TheJustMoose/74HC-CPU/hard/!CMD_DEC/Flags/pdf/Flags-B_Cu.pdf

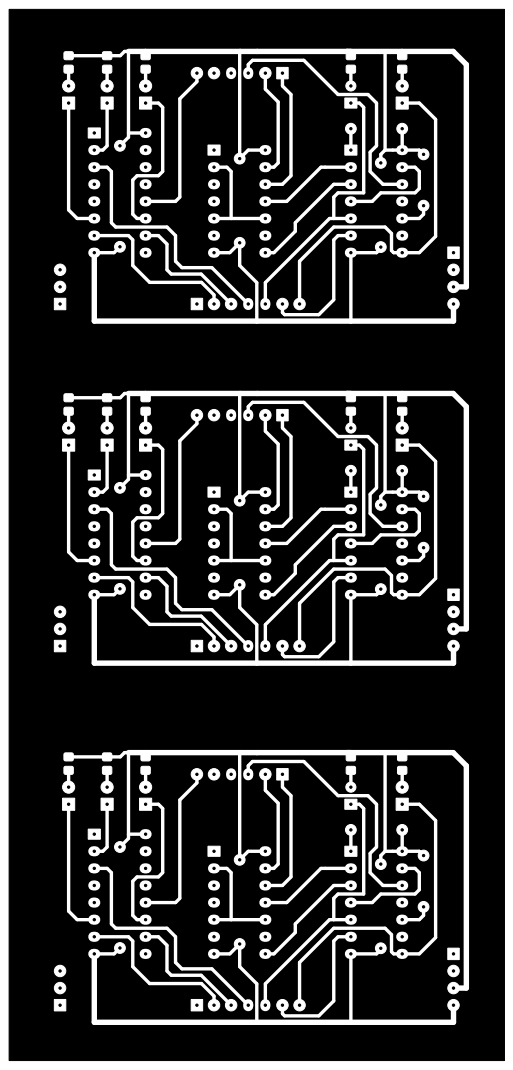
[picture p27: page 1]
