TheJustMoose/74HC-CPU/hard/!CMD_DEC/Flags/pdf/Flags-F_Cu.pdf

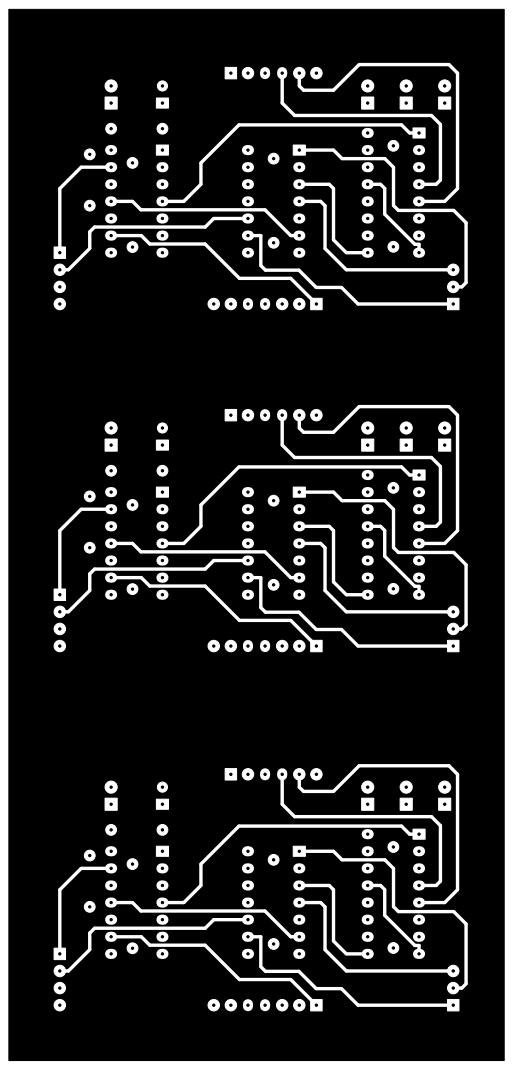
[picture p28: page 1]
