TheJustMoose/74HC-CPU/hard/!ALU/LSR/pdf/LSR-F_Cu.pdf

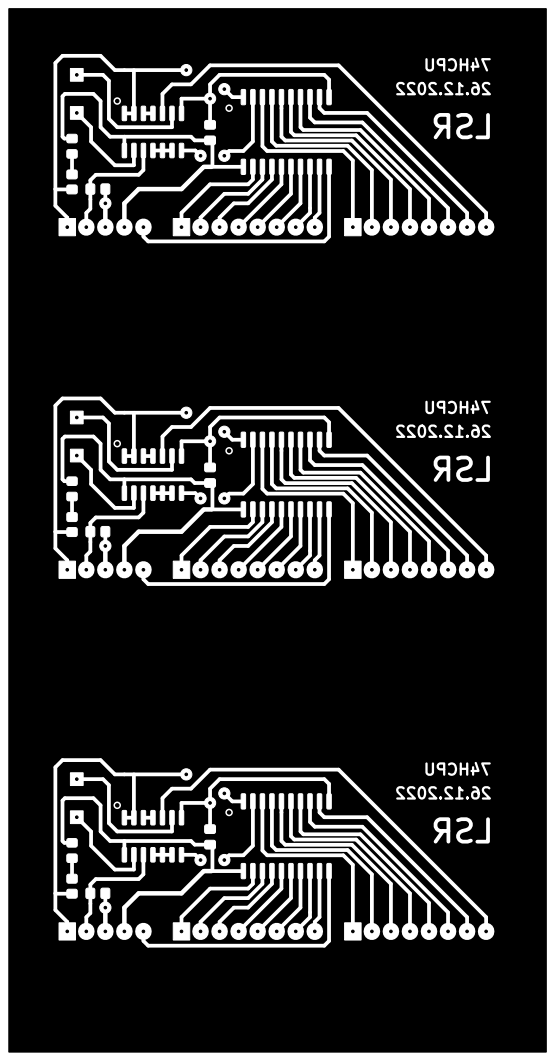
[picture p29: page 1]
