TheJustMoose/74HC-CPU/hard/!ALU/SWAP/pdf/SWAP-F_Cu.pdf

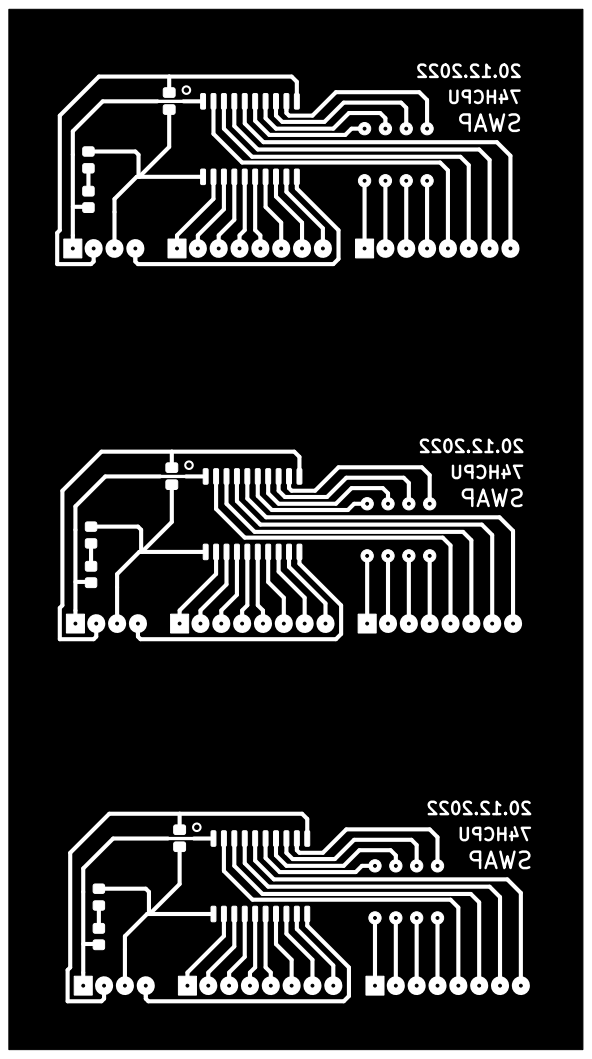
[picture p30: page 1]
