TheJustMoose/74HC-CPU/hard/!ALU/MOV/pdf/MOV-F_Cu.pdf

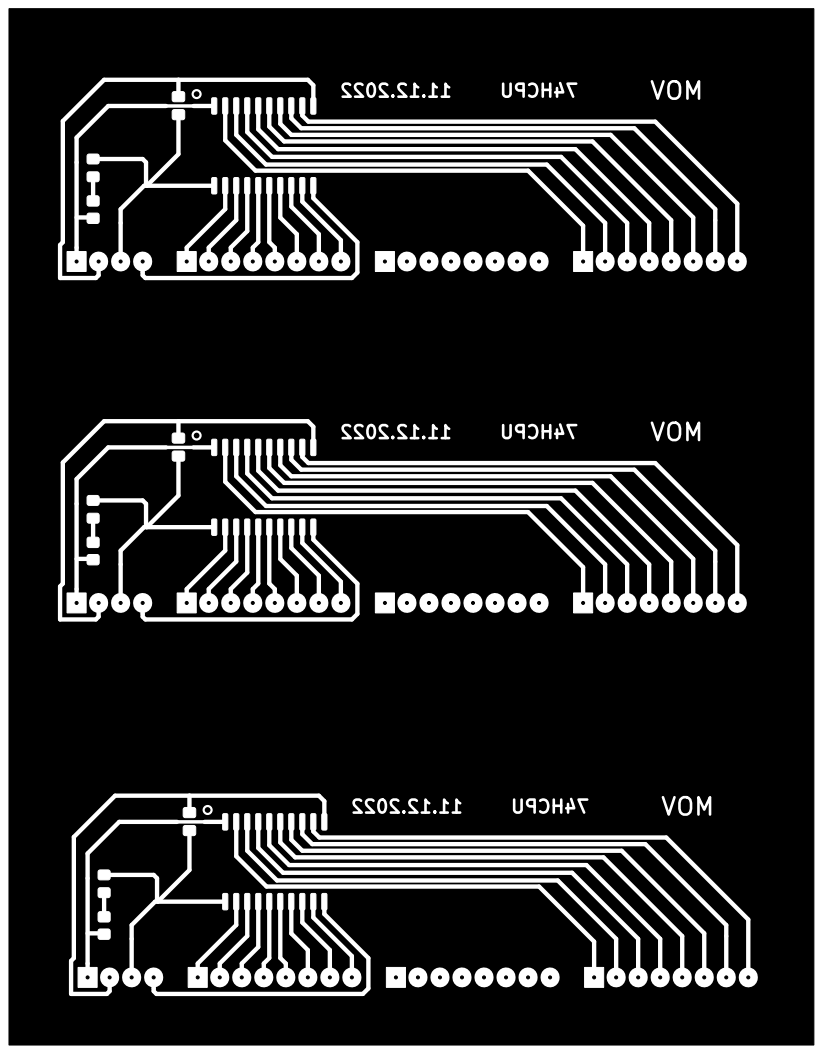
[picture p31: page 1]
