TheJustMoose/74HC-CPU/hard/!ALU/CMP/pdf/CMP-B_Cu.pdf

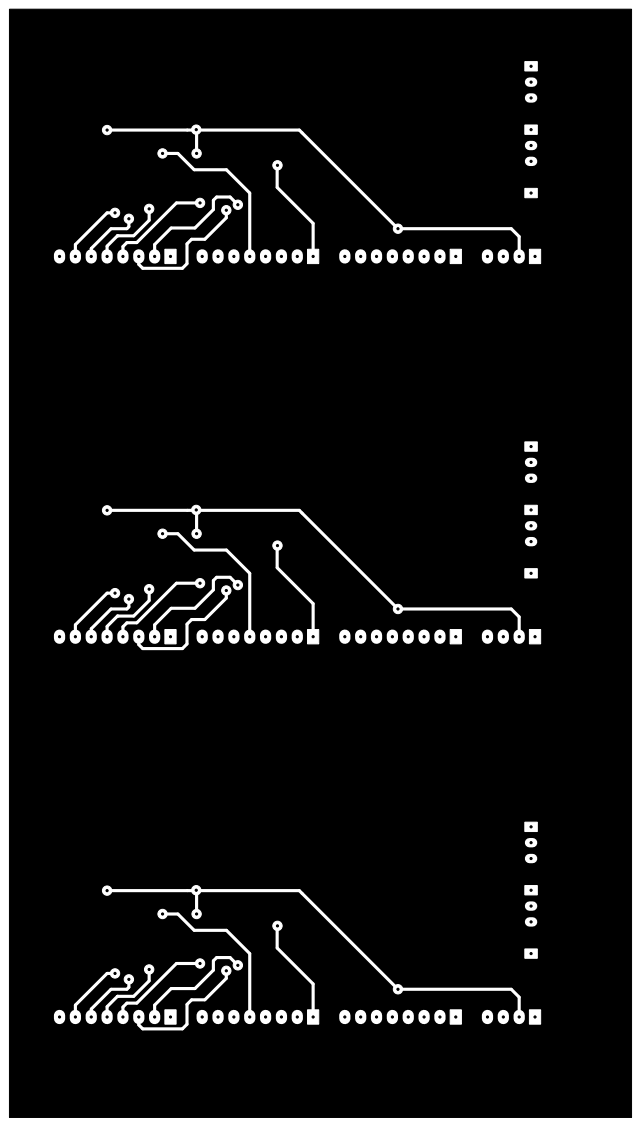
[picture p32: page 1]
