TheJustMoose/74HC-CPU/hard/!ALU/CMP/pdf/CMP-F_Cu.pdf

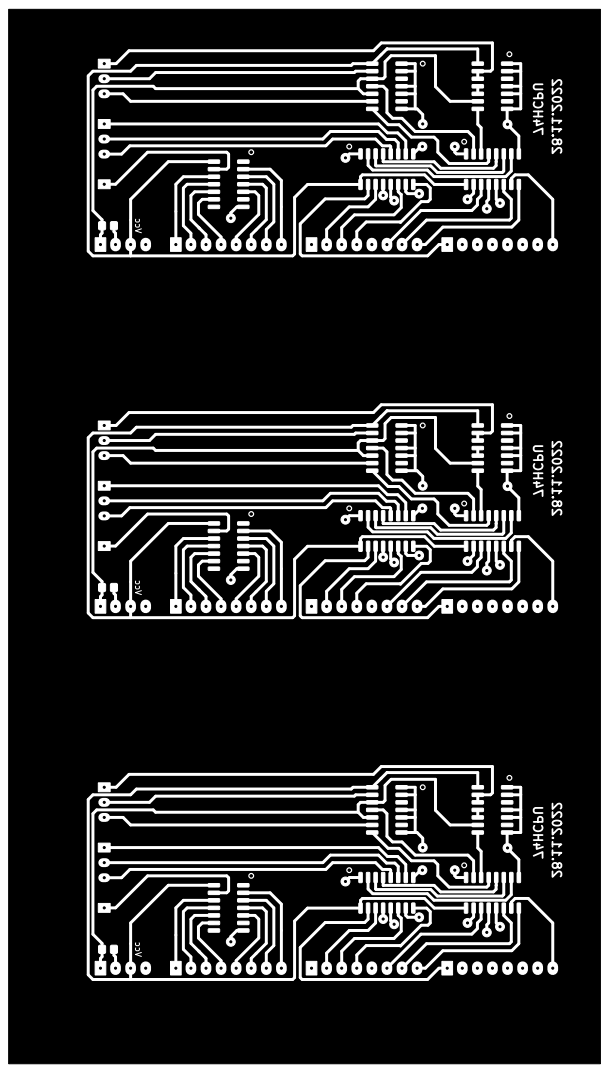
[picture p33: page 1]
