TheJustMoose/74HC-CPU/hard/!ALU/ADD/pdf/ADD-B_Cu.pdf

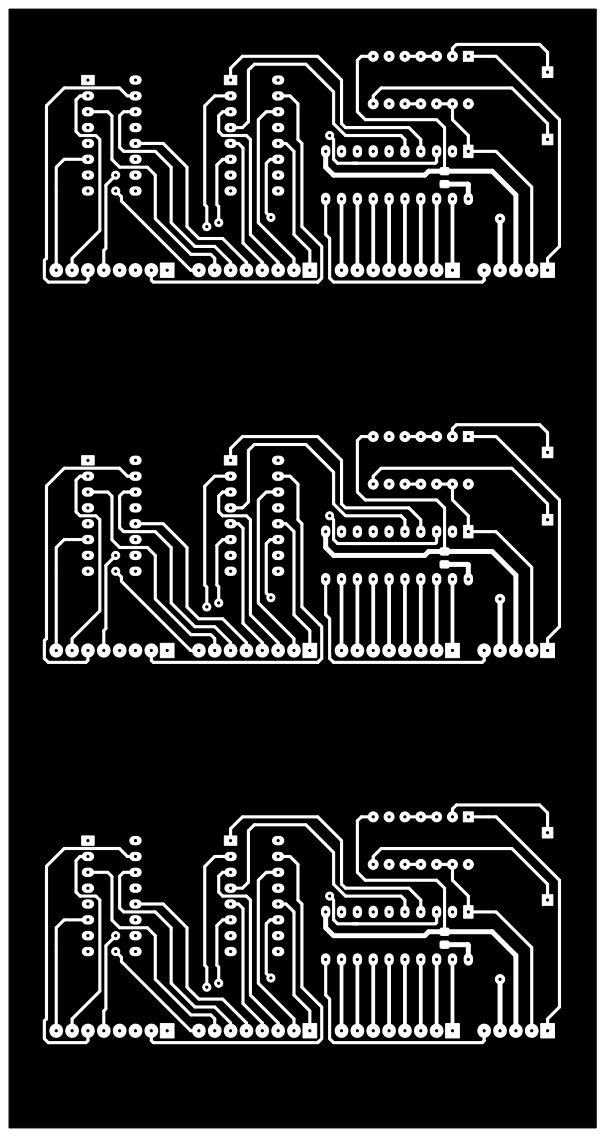
[picture p34: page 1]
