TheJustMoose/74HC-CPU/hard/!ALU/ADD/pdf/ADD-F_Cu.pdf

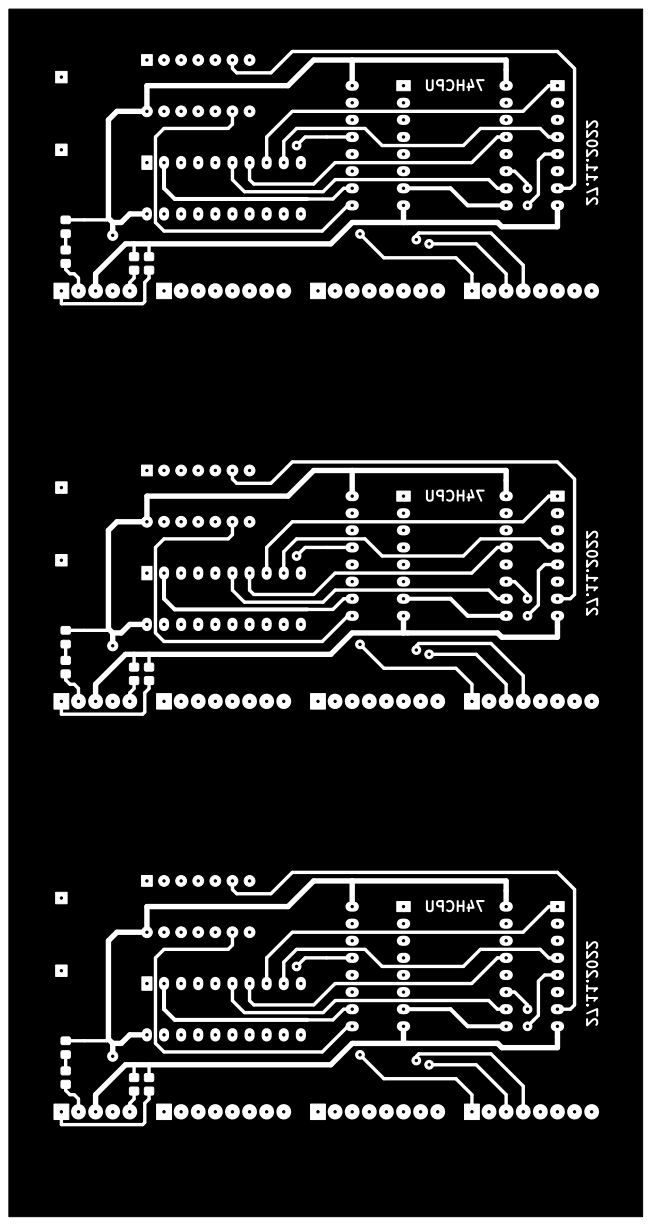
[picture p35: page 1]
