TheJustMoose/74HC-CPU/hard/Proto/273/pdf/273-F_Cu.pdf

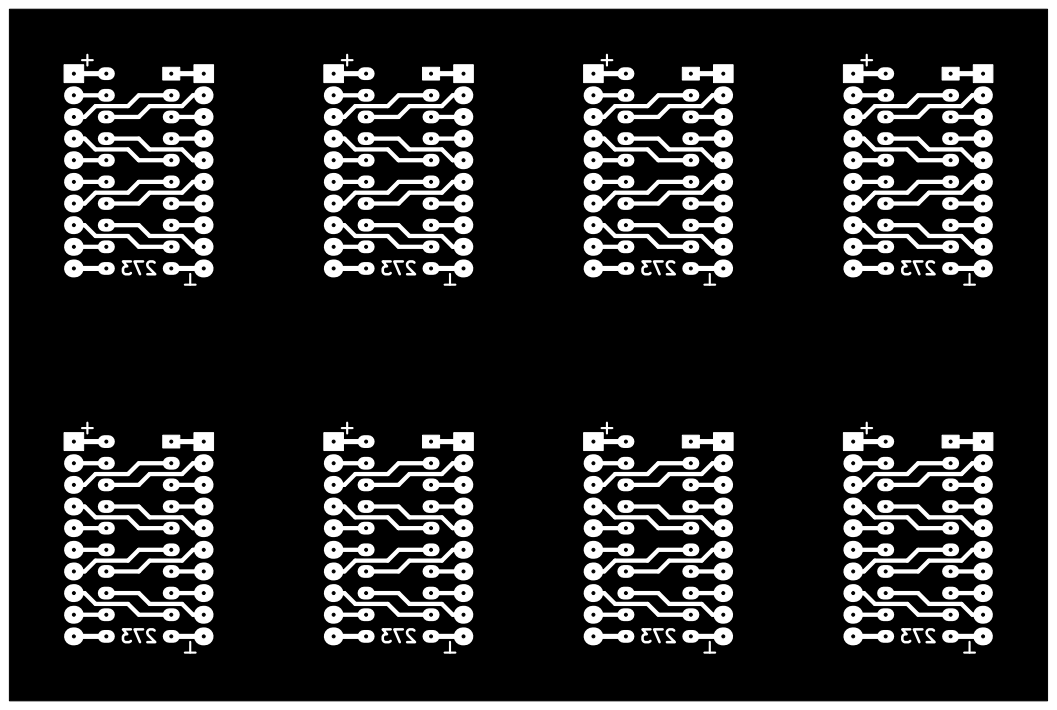
[picture p36: page 1]
