TheJustMoose/74HC-CPU/hard/!ALU/AND_SMD/pdf/AND-B_Cu.pdf

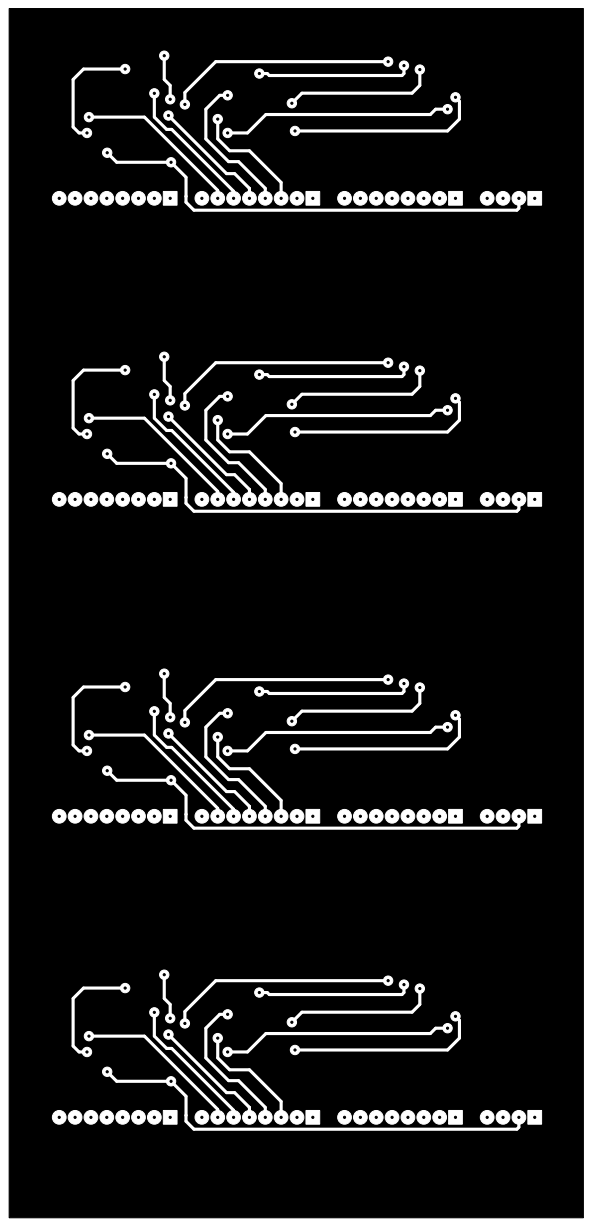
[picture p37: page 1]
