TheJustMoose/74HC-CPU/hard/!ALU/AND_SMD/pdf/AND-F_Cu.pdf

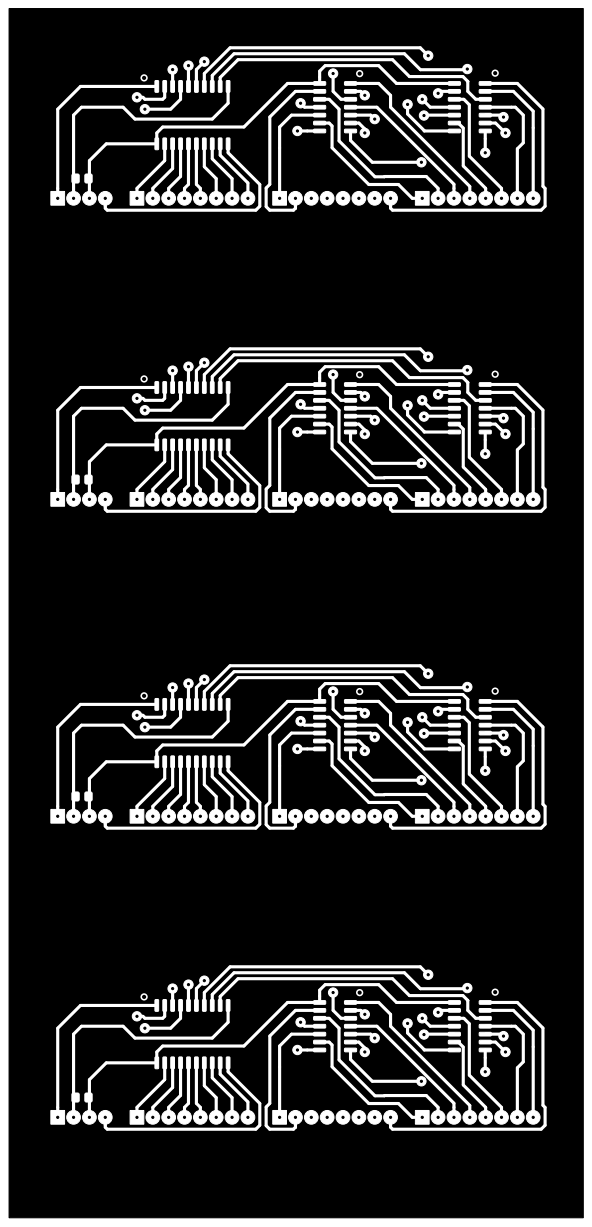
[picture p38: page 1]
