TheJustMoose/74HC-CPU/Trash/MUX8x1-v3/pdf/MUX8x1-v3-B_Cu.pdf

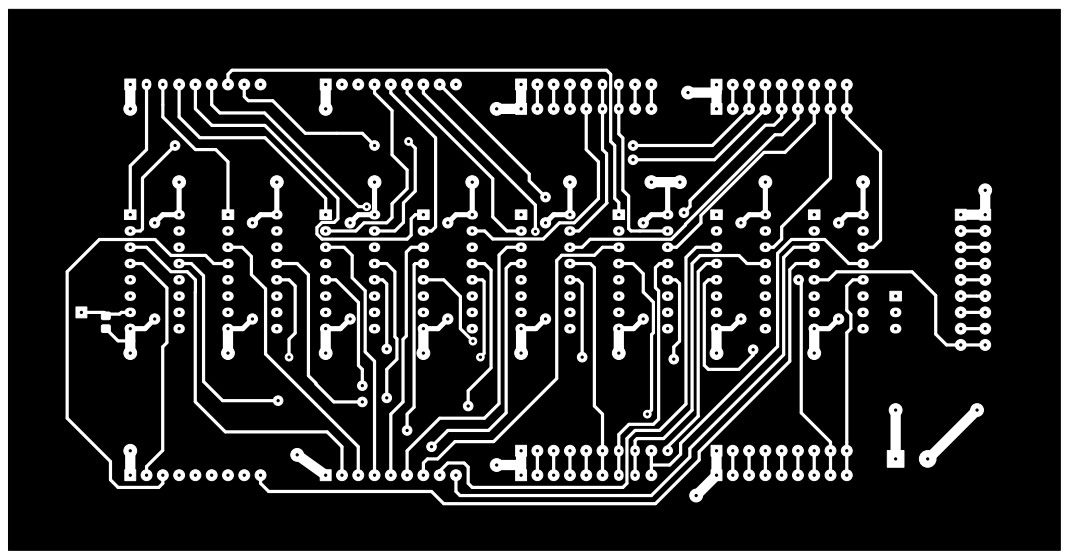
[picture p39: page 1]
