TheJustMoose/74HC-CPU/Trash/MUX8x1-v3/pdf/MUX8x1-v3-F_Cu.pdf

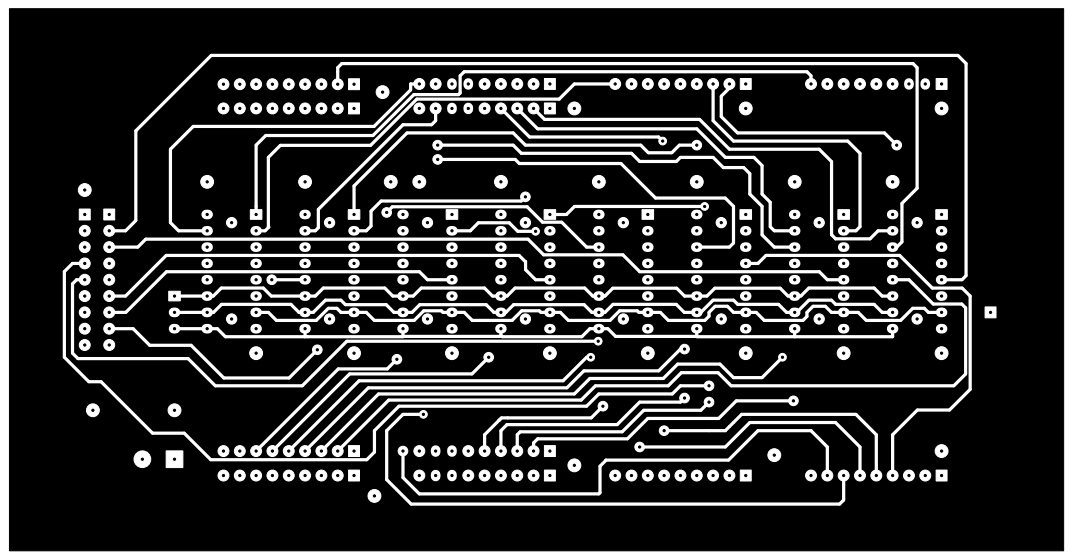
[picture p40: page 1]
