TheJustMoose/74HC-CPU/Trash/MUX8x1-v3/pdf/MUX8x1-v3-In2_Cu.pdf

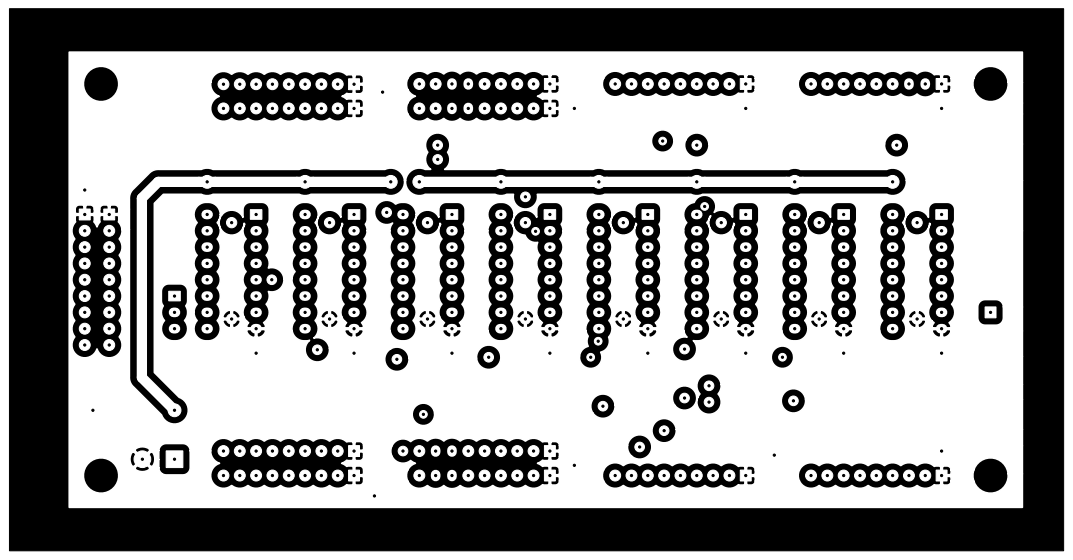
[picture p41: page 1]
