TheJustMoose/74HC-CPU/Trash/MUX4x1-v2/pdf/MUX4x1-B_Cu.pdf

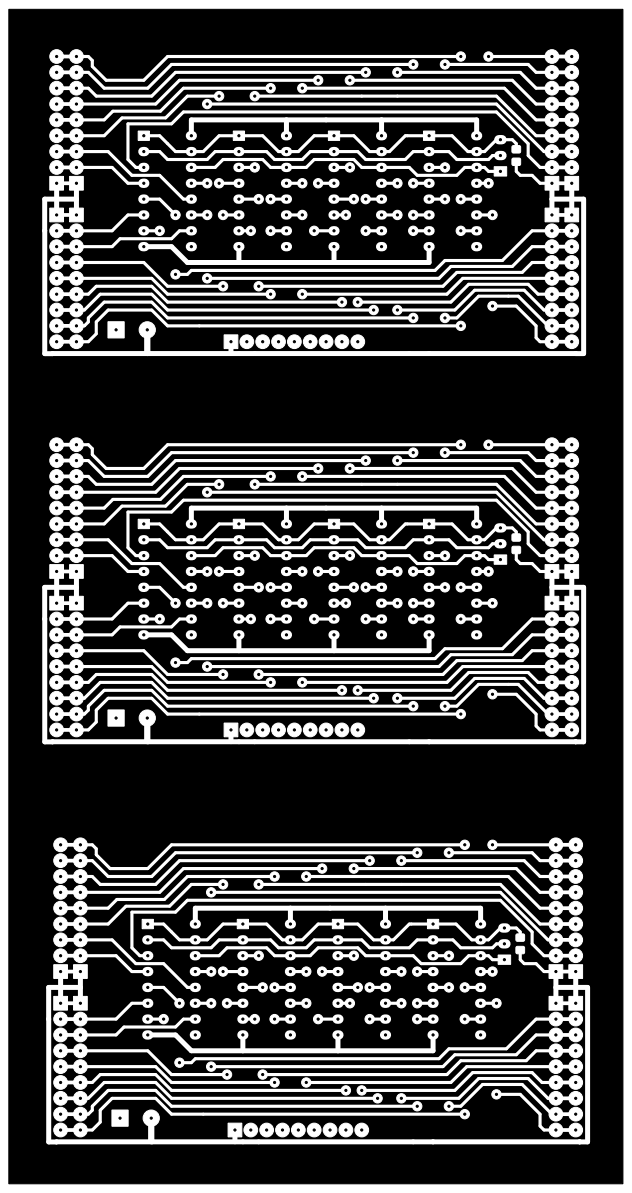
[picture p42: page 1]
