TheJustMoose/74HC-CPU/Trash/MUX4x1-v2/pdf/MUX4x1-F_Cu.pdf

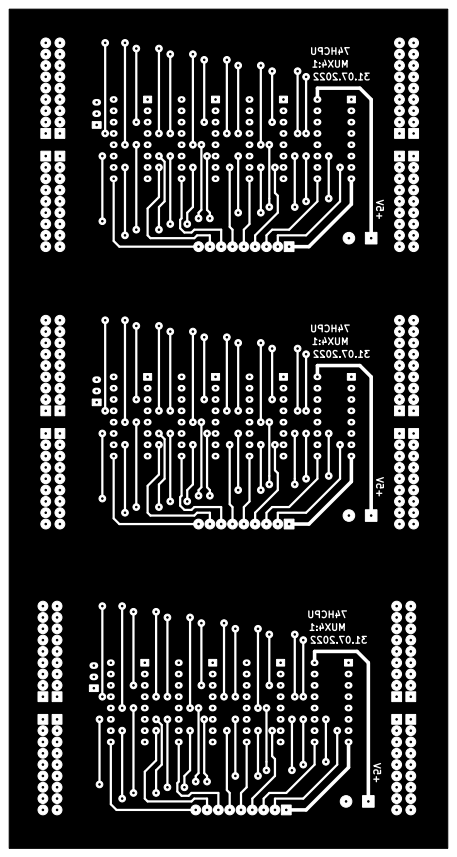
[picture p43: page 1]
