TheJustMoose/74HC-CPU/Trash/Regs-v2/pdf/Regs-v2-B_Cu.pdf

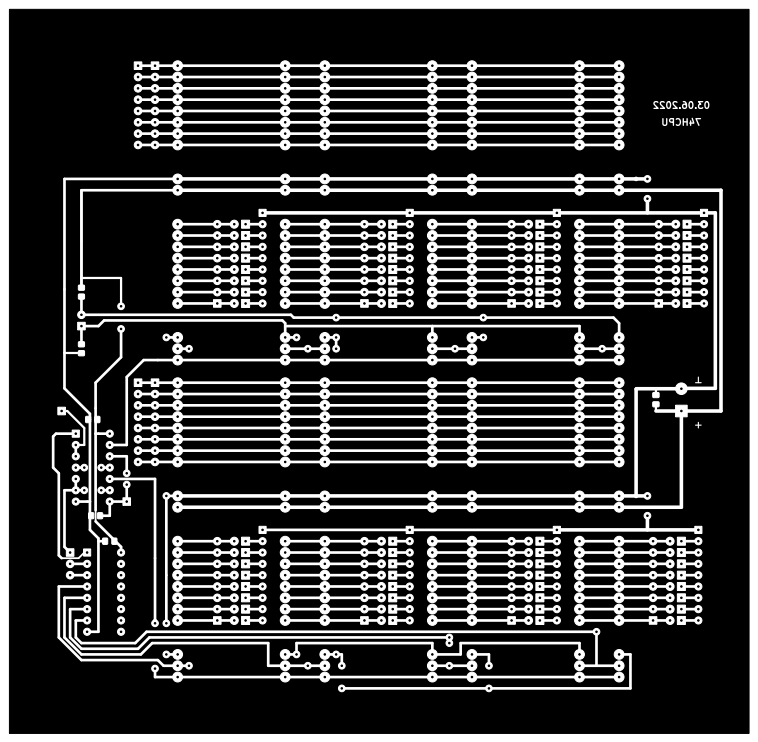
[picture p44: page 1]
