TheJustMoose/74HC-CPU/hard/!ADDR_CNT/STACK16/STACK16.kicad_pcb

## KiCad design hard/!ADDR_CNT/STACK16/STACK16.kicad_pcb (2024-06-18)

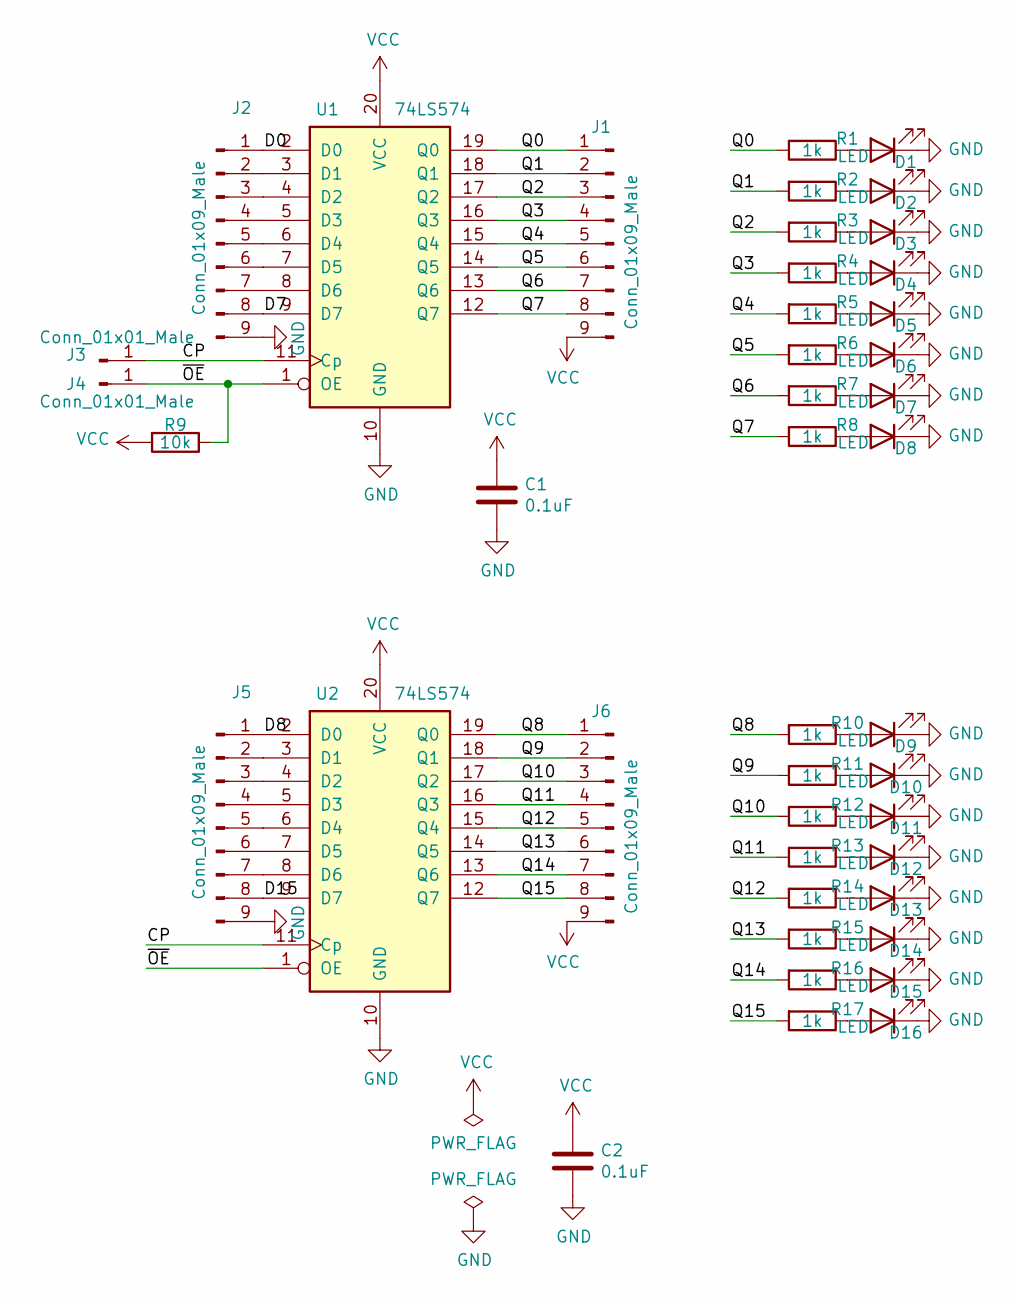
[picture p74: schematic STACK16.sch]

Parts:
C1, C2: 0.1uF; C_0805_2012Metric_Pad1.18x1.45mm_HandSolder
D1, D2, D3, D4, D5, D6, D7, D8, D9, D10, D11, D12, D13, D14, D15, D16: LED; LED_0805_2012Metric_Pad1.15x1.40mm_HandSolder
J1, J2, J5, J6: Conn_01x09_Male; PinHeader_1x09_P2.54mm_Vertical
J3, J4: Conn_01x01_Male; PinHeader_1x01_P2.54mm_Horizontal
R1, R2, R3, R4, R5, R6, R7, R8, R10, R11, R12, R13, R14, R15, R16, R17: 1k; R_0805_2012Metric_Pad1.20x1.40mm_HandSolder
R9: 10k; R_0805_2012Metric_Pad1.20x1.40mm_HandSolder
U1, U2: 74LS574; SO-20_12.8x7.5mm_P1.27mm

Connections:
/CP: J3.1, U1.11 (Cp), U2.11 (Cp)
/D0: J2.1, U1.2 (D0)
/D7: J2.8, U1.9 (D7)
/D8: J5.1, U2.2 (D0)
/D15: J5.8, U2.9 (D7)
/Q0: J1.1, R1.2, U1.19 (Q0)
/Q1: J1.2, R2.2, U1.18 (Q1)
/Q2: J1.3, R3.2, U1.17 (Q2)
/Q3: J1.4, R4.2, U1.16 (Q3)
/Q4: J1.5, R5.2, U1.15 (Q4)
/Q5: J1.6, R6.2, U1.14 (Q5)
/Q6: J1.7, R7.2, U1.13 (Q6)
/Q7: J1.8, R8.2, U1.12 (Q7)
/Q8: J6.1, R10.2, U2.19 (Q0)
/Q9: J6.2, R11.2, U2.18 (Q1)
/Q10: J6.3, R12.2, U2.17 (Q2)
/Q11: J6.4, R13.2, U2.16 (Q3)
/Q12: J6.5, R14.2, U2.15 (Q4)
/Q13: J6.6, R15.2, U2.14 (Q5)
/Q14: J6.7, R16.2, U2.13 (Q6)
/Q15: J6.8, R17.2, U2.12 (Q7)
/~OE: J4.1, R9.1, U1.1 (OE), U2.1 (OE)
GND: C1.2, C2.2, D1.1 (K), D2.1 (K), D3.1 (K), D4.1 (K), D5.1 (K), D6.1 (K), D7.1 (K), D8.1 (K), D9.1 (K), D10.1 (K), D11.1 (K), D12.1 (K), D13.1 (K), D14.1 (K), D15.1 (K), D16.1 (K), J2.9, J5.9, U1.10 (GND), U2.10 (GND)
unnamed: D1.2 (A), R1.1
unnamed: D2.2 (A), R2.1
unnamed: D3.2 (A), R3.1
unnamed: D4.2 (A), R4.1
unnamed: D5.2 (A), R5.1
unnamed: D6.2 (A), R6.1
unnamed: D7.2 (A), R7.1
unnamed: D8.2 (A), R8.1
unnamed: D9.2 (A), R10.1
unnamed: D10.2 (A), R11.1
unnamed: D11.2 (A), R12.1
unnamed: D12.2 (A), R13.1
unnamed: D13.2 (A), R14.1
unnamed: D14.2 (A), R15.1
unnamed: D15.2 (A), R16.1
unnamed: D16.2 (A), R17.1
unnamed: J2.2, U1.3 (D1)
unnamed: J2.3, U1.4 (D2)
unnamed: J2.4, U1.5 (D3)
unnamed: J2.5, U1.6 (D4)
unnamed: J2.6, U1.7 (D5)
unnamed: J2.7, U1.8 (D6)
unnamed: J5.2, U2.3 (D1)
unnamed: J5.3, U2.4 (D2)
unnamed: J5.4, U2.5 (D3)
unnamed: J5.5, U2.6 (D4)
unnamed: J5.6, U2.7 (D5)
unnamed: J5.7, U2.8 (D6)
VCC: C1.1, C2.1, J1.9, J6.9, R9.2, U1.20 (VCC), U2.20 (VCC)

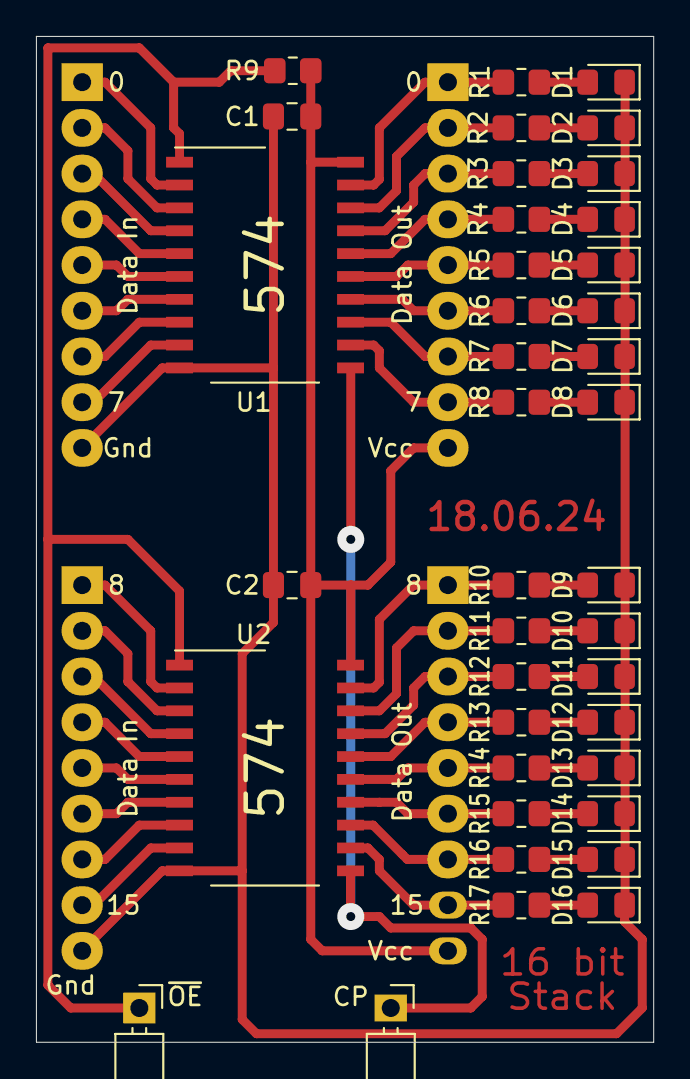
[picture p75: board STACK16.kicad_pcb from above]

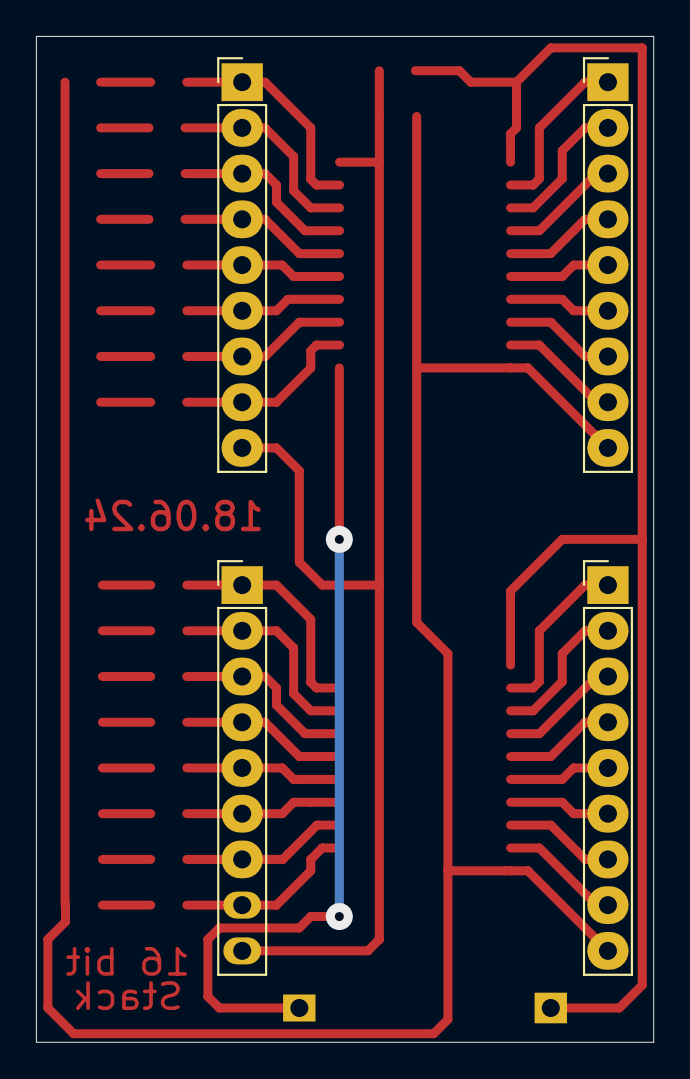
[picture p76: board STACK16.kicad_pcb from below]

Board: 2 copper layers, 34.3 x 55.9 mm, 43 parts (4 on the bottom side), 52 nets.
