TheJustMoose/74HC-CPU/hard/Proto/template-b/template-b.kicad_pcb

## KiCad design hard/Proto/template-b/template-b.kicad_pcb (2022-02-21)

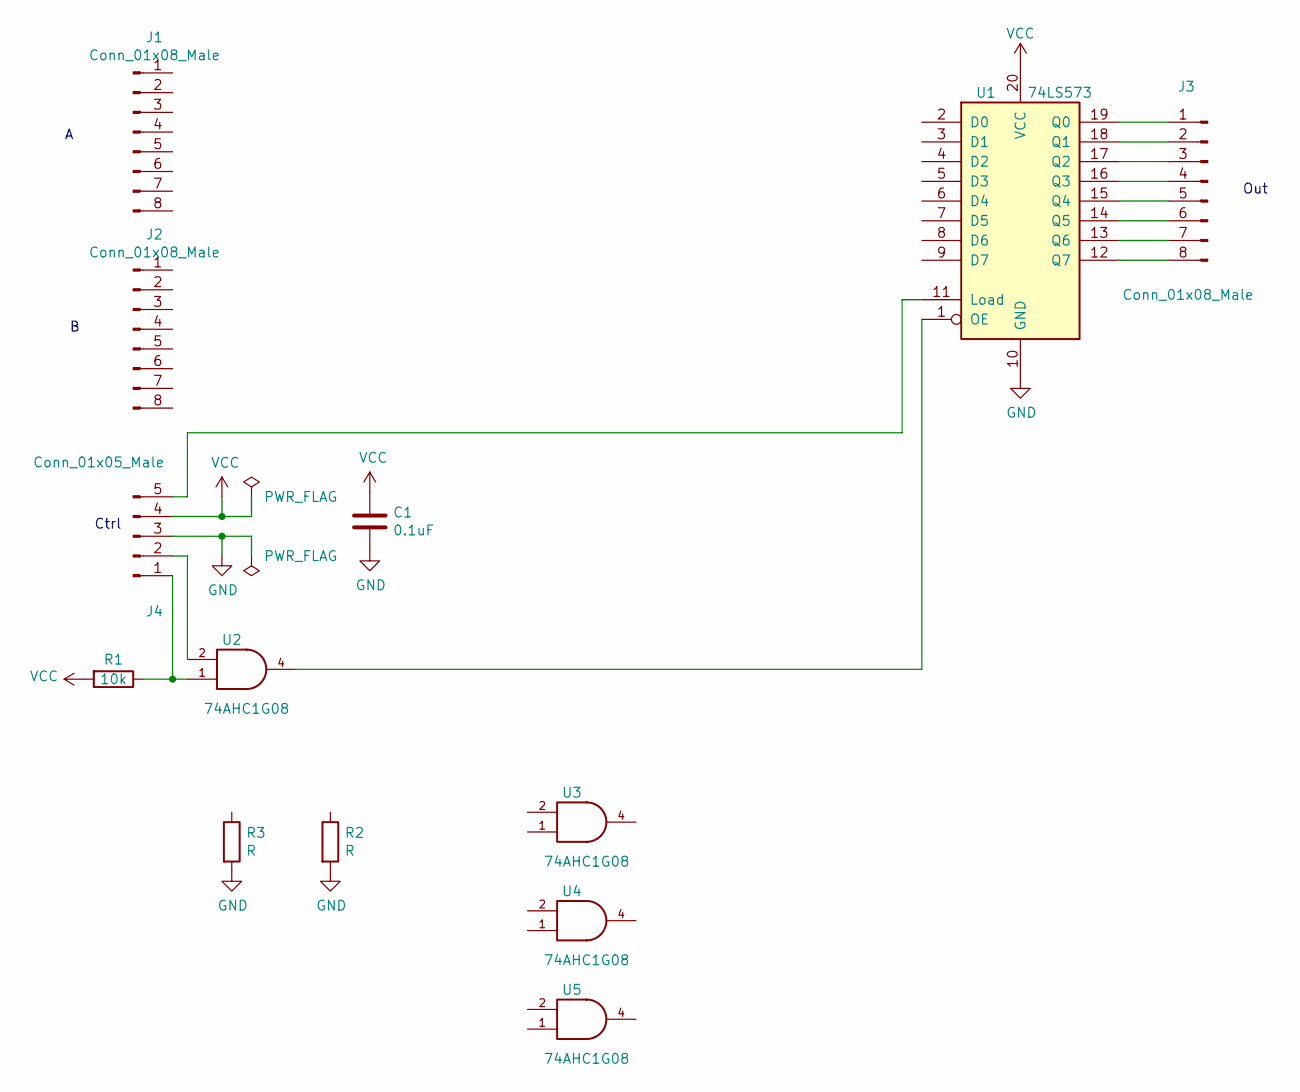
[picture p77: schematic template-b.sch]

Parts:
C1: 0.1uF; C_Disc_D4.7mm_W2.5mm_P5.00mm
J1, J2, J3: Conn_01x08_Male; PinHeader_1x08_P2.54mm_Horizontal
J4: Conn_01x05_Male; PinHeader_1x05_P2.54mm_Horizontal
R1: 10k; R_0805_2012Metric_Pad1.20x1.40mm_HandSolder
R2, R3: R; R_0805_2012Metric_Pad1.20x1.40mm_HandSolder
U1: 74LS573; DIP-20_W7.62mm
U2, U3, U4, U5: 74AHC1G08; tssop5

Connections:
GND: C1.2, J4.3, R2.2, R3.2, U1.10 (GND), U2.3 (GND), U3.3 (GND), U4.3 (GND), U5.3 (GND)
unnamed: J3.1, U1.19 (Q0)
unnamed: J3.2, U1.18 (Q1)
unnamed: J3.3, U1.17 (Q2)
unnamed: J3.4, U1.16 (Q3)
unnamed: J3.5, U1.15 (Q4)
unnamed: J3.6, U1.14 (Q5)
unnamed: J3.7, U1.13 (Q6)
unnamed: J3.8, U1.12 (Q7)
unnamed: J4.1, R1.1, U2.1
unnamed: J4.2, U2.2
unnamed: J4.5, U1.11 (Load)
unnamed: U1.1 (OE), U2.4
VCC: C1.1, J4.4, R1.2, U1.20 (VCC), U2.5 (VCC), U3.5 (VCC), U4.5 (VCC), U5.5 (VCC)

Notes on the sheet:
Out
Ctrl

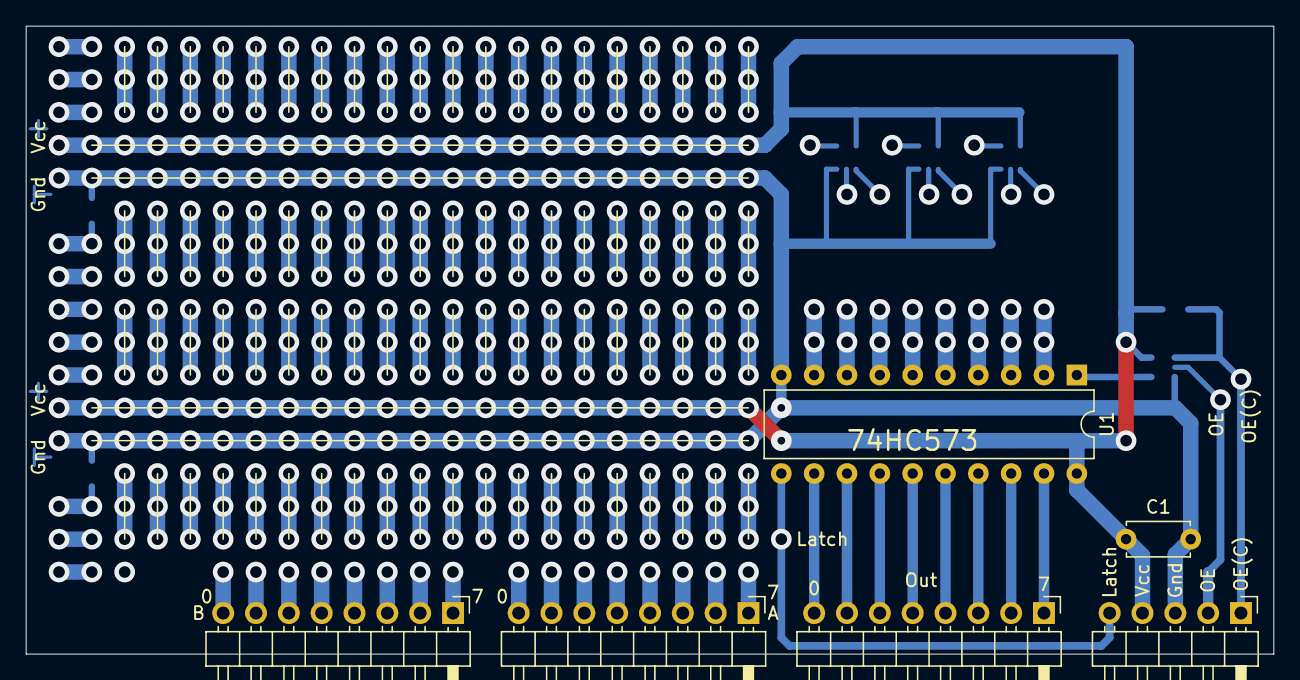
[picture p78: board template-b.kicad_pcb from above]

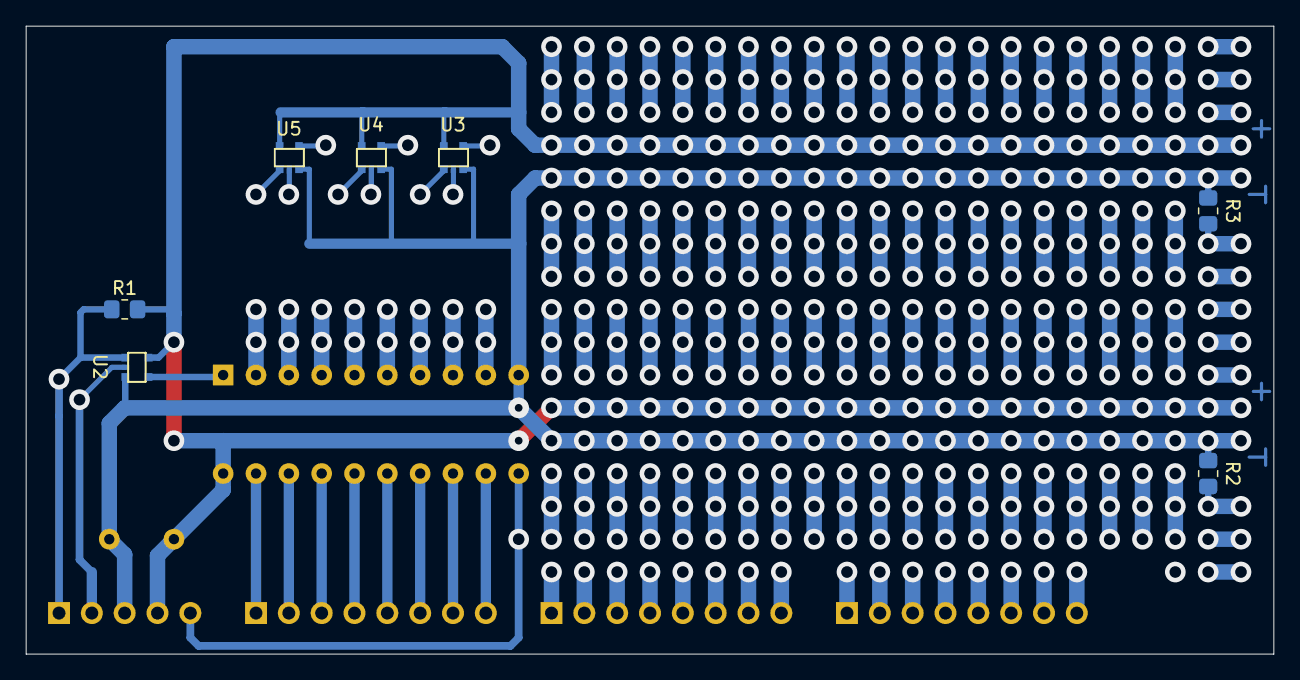
[picture p79: board template-b.kicad_pcb from below]

Board: 2 copper layers, 96.5 x 48.6 mm, 13 parts (7 on the bottom side), 14 nets.
