TheJustMoose/74HC-CPU/hard/!CMD_DEC/Flags/Flags.kicad_pcb

## KiCad design hard/!CMD_DEC/Flags/Flags.kicad_pcb (2023-05-24)

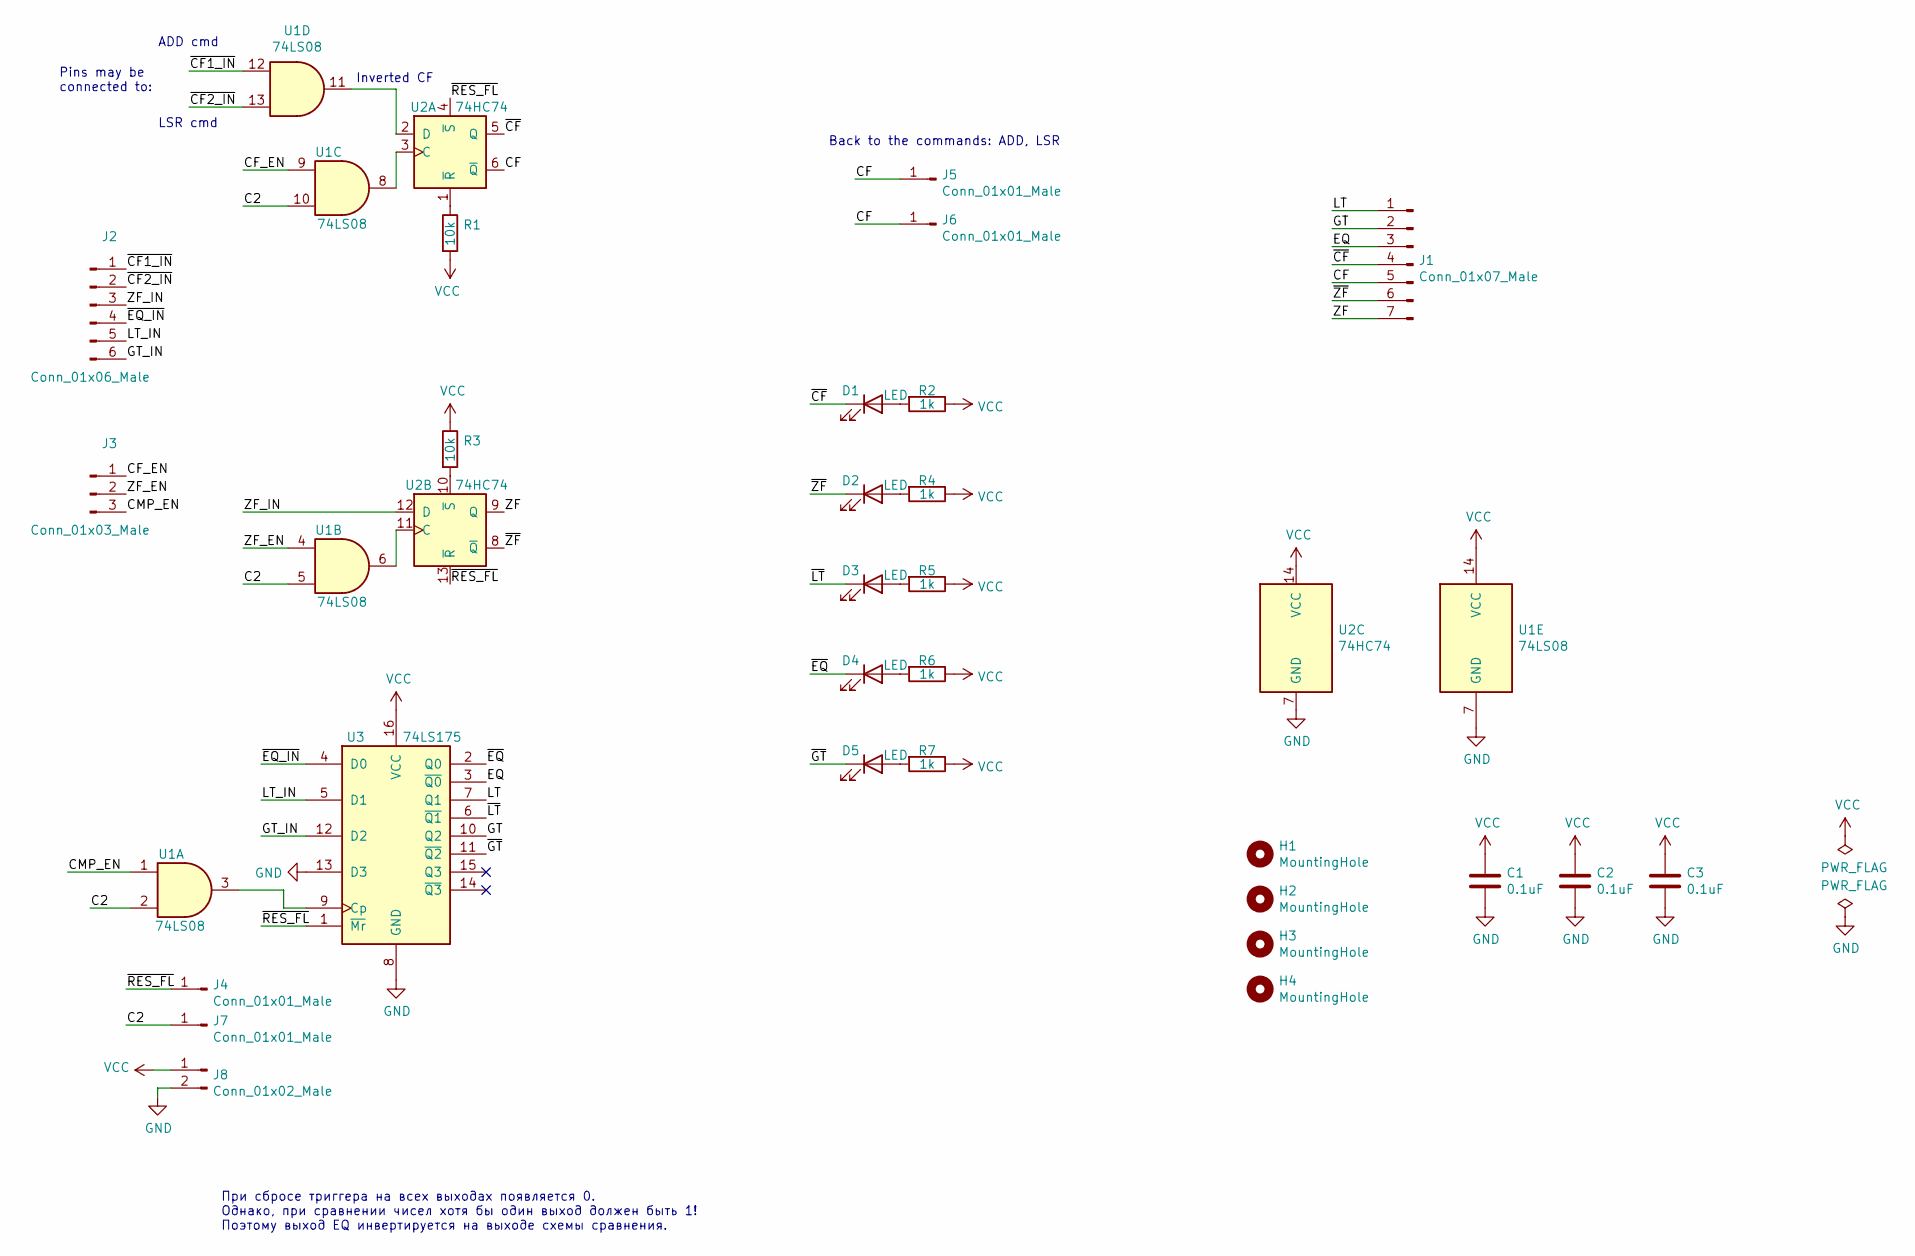
[picture p80: schematic Flags.sch]

Parts:
C1, C2: 0.1uF; C_Axial_L5.1mm_D3.1mm_P12.50mm_Horizontal
C3: 0.1uF; C_Axial_L5.1mm_D3.1mm_P15.00mm_Horizontal
D1, D2, D3, D4, D5: LED; LED_Rectangular_W5.0mm_H2.0mm
H1, H2, H3, H4: MountingHole; MountingHole_3.2mm_M3
J1: Conn_01x07_Male; PinHeader_1x07_P2.54mm_Vertical
J2: Conn_01x06_Male; PinHeader_1x06_P2.54mm_Vertical
J3: Conn_01x03_Male; PinHeader_1x03_P2.54mm_Vertical
J4, J5, J6, J7: Conn_01x01_Male; PinHeader_1x01_P2.54mm_Vertical
J8: Conn_01x02_Male; PinHeader_1x02_P2.54mm_Vertical
R1, R3: 10k; R_Axial_DIN0207_L6.3mm_D2.5mm_P7.62mm_Horizontal
R2, R4, R5, R6, R7: 1k; R_0805_2012Metric_Pad1.20x1.40mm_HandSolder
U1: 74LS08; DIP-14_W7.62mm_Socket
U2: 74HC74; DIP-14_W7.62mm_Socket
U3: 74LS175; DIP-16_W7.62mm_Socket

Connections:
/C2: J7.1, U1.2, U1.5, U1.10
/CF: J1.5, J5.1, J6.1, U2.6 (~Q)
/CF_EN: J3.1, U1.9
/CMP_EN: J3.3, U1.1
/EQ: J1.3, U3.3 (~Q0)
/GT: J1.2, U3.10 (Q2)
/GT_IN: J2.6, U3.12 (D2)
/LT: J1.1, U3.7 (Q1)
/LT_IN: J2.5, U3.5 (D1)
/ZF: J1.7, U2.9 (Q)
/ZF_EN: J3.2, U1.4
/ZF_IN: J2.3, U2.12 (D)
/~CF: D1.1 (K), J1.4, U2.5 (Q)
/~CF1_IN: J2.1, U1.12
/~CF2_IN: J2.2, U1.13
/~EQ: D4.1 (K), U3.2 (Q0)
/~EQ_IN: J2.4, U3.4 (D0)
/~GT: D5.1 (K), U3.11 (~Q2)
/~LT: D3.1 (K), U3.6 (~Q1)
/~RES_FL: J4.1, U2.4 (~S), U2.13 (~R), U3.1 (~Mr)
/~ZF: D2.1 (K), J1.6, U2.8 (~Q)
GND: C1.2, C2.2, C3.2, J8.2, U1.7 (GND), U2.7 (GND), U3.8 (GND), U3.13 (D3)
unnamed: D1.2 (A), R2.2
unnamed: D2.2 (A), R4.2
unnamed: D3.2 (A), R5.2
unnamed: D4.2 (A), R6.2
unnamed: D5.2 (A), R7.2
unnamed: R1.1, U2.1 (~R)
unnamed: R3.2, U2.10 (~S)
unnamed: U1.3, U3.9 (Cp)
unnamed: U1.6, U2.11 (C)
unnamed: U1.8, U2.3 (C)
unnamed: U1.11, U2.2 (D)
VCC: C1.1, C2.1, C3.1, J8.1, R1.2, R2.1, R3.1, R4.1, R5.1, R6.1, R7.1, U1.14 (VCC), U2.14 (VCC), U3.16 (VCC)

Notes on the sheet:
При сбросе триггера на всех выходах появляется 0. Однако, при сравнении чисел хотя бы один выход должен быть 1! Поэтому выход EQ инвертируется на выходе схемы сравнения.
ADD cmd
LSR cmd
Pins may be connected to:
Inverted CF
Back to the commands: ADD, LSR

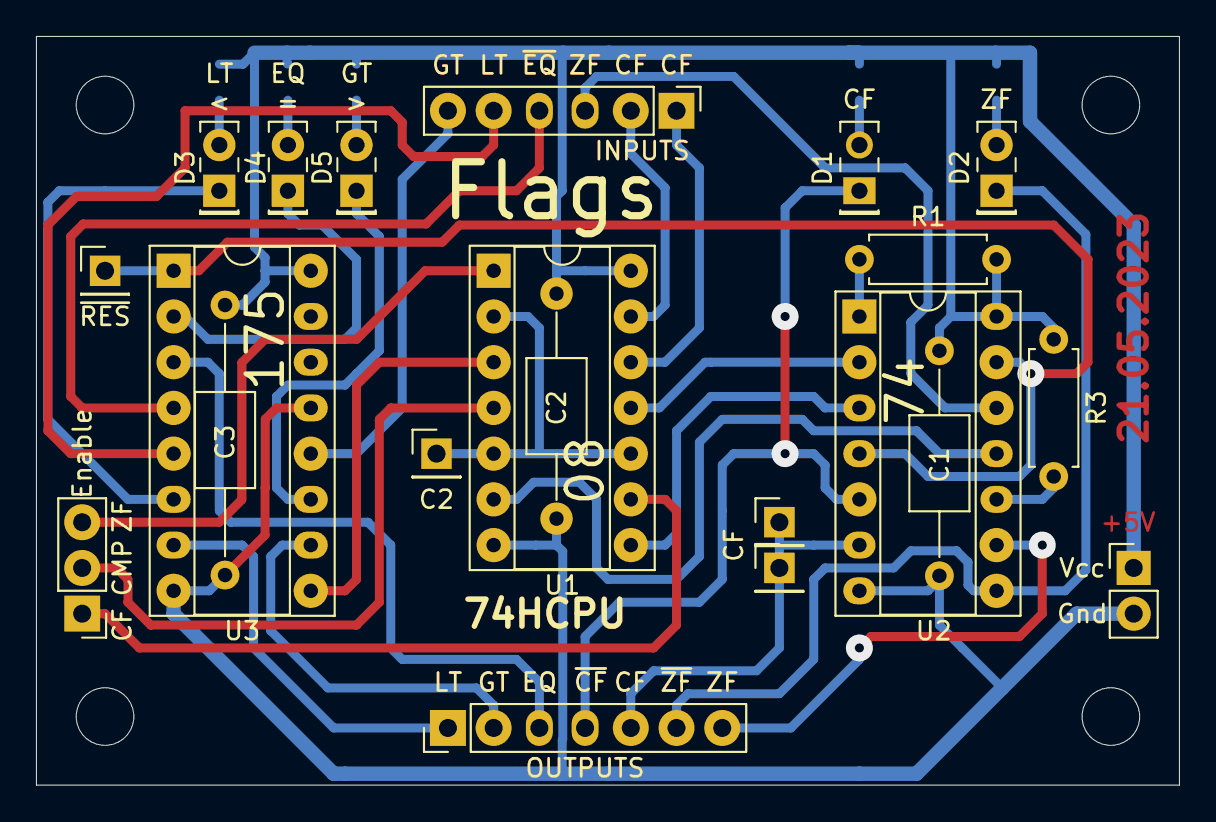
[picture p81: board Flags.kicad_pcb from above]

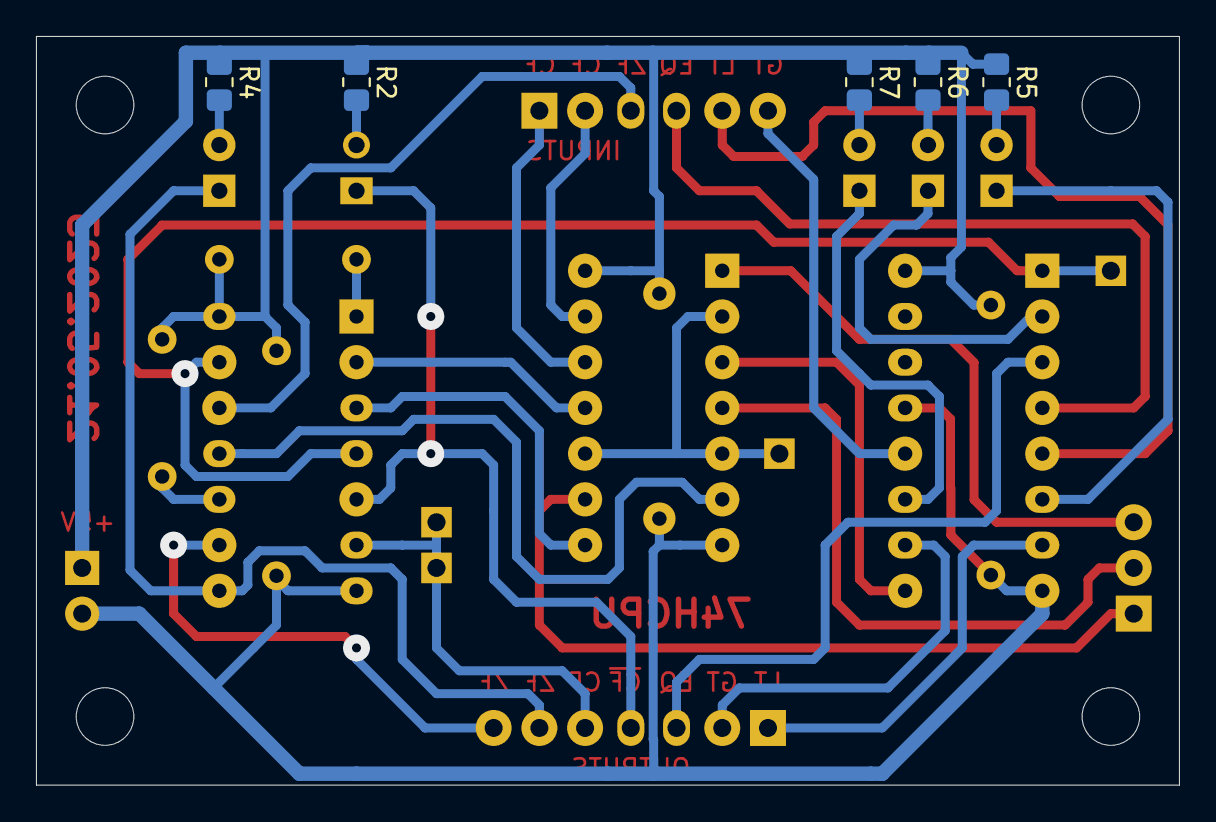
[picture p82: board Flags.kicad_pcb from below]

Board: 2 copper layers, 63.5 x 41.6 mm, 30 parts (5 on the bottom side), 34 nets.
