TheJustMoose/74HC-CPU/hard/!ALU/AND_SMD/AND.kicad_pcb

## KiCad design hard/!ALU/AND_SMD/AND.kicad_pcb (2023-02-24)

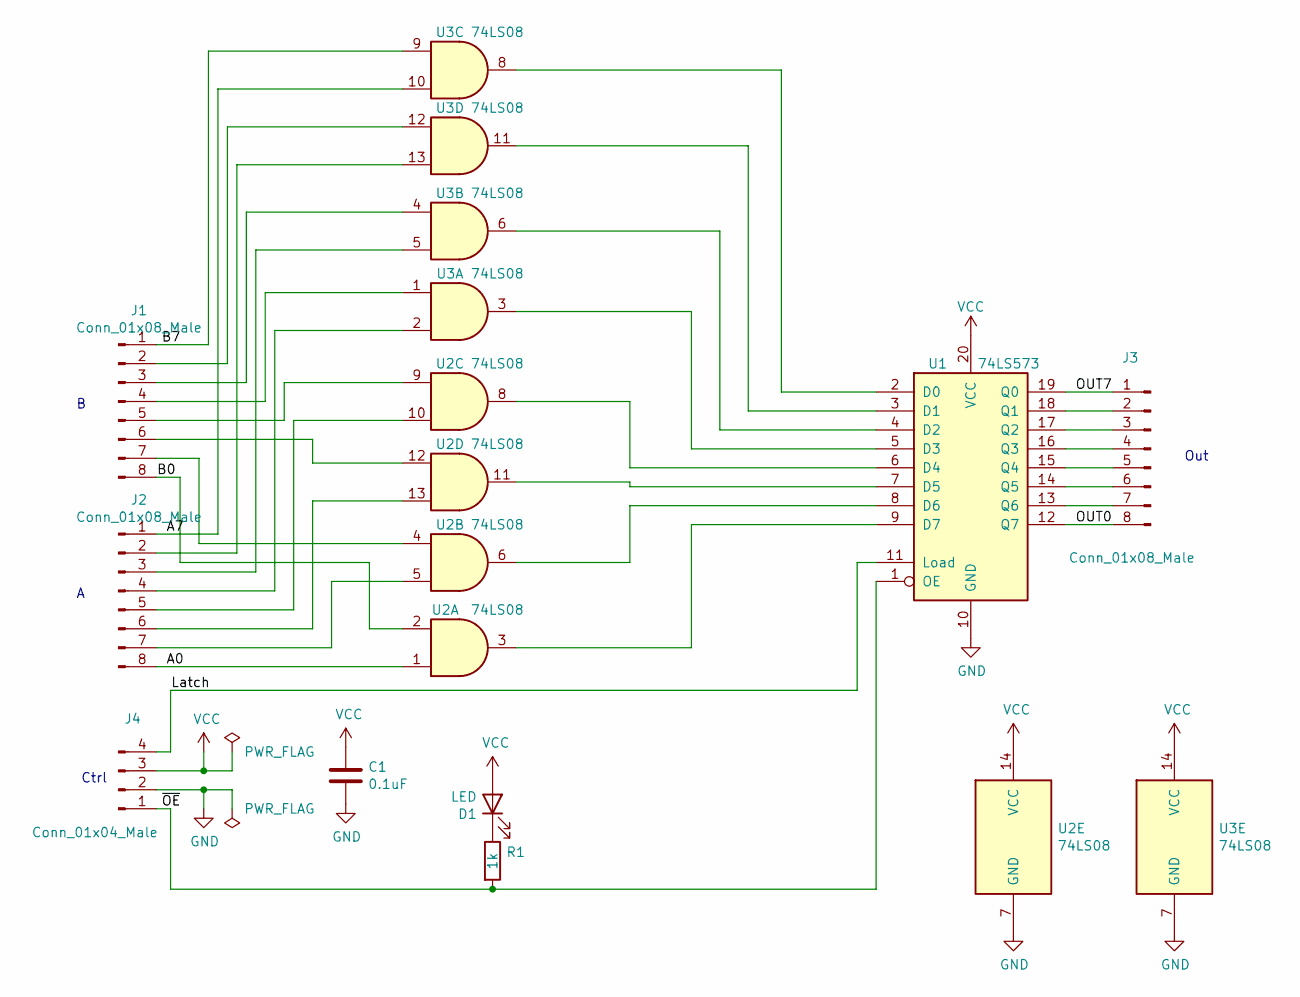
[picture p83: schematic AND.sch]

Parts:
C1: 0.1uF; C_0805_2012Metric_Pad1.18x1.45mm_HandSolder
D1: LED; LED_0805_2012Metric_Pad1.15x1.40mm_HandSolder
J1, J2, J3: Conn_01x08_Male; PinHeader_1x08_P2.54mm_Vertical
J4: Conn_01x04_Male; PinHeader_1x04_P2.54mm_Vertical
R1: 1k; R_0805_2012Metric_Pad1.20x1.40mm_HandSolder
U1: 74LS573; SOP-20_7.5x12.8mm_P1.27mm
U2, U3: 74LS08; SO-14_3.9x8.65mm_P1.27mm

Connections:
/A0: J2.8, U2.1
/A7: J2.1, U3.10
/B0: J1.8, U2.2
/B7: J1.1, U3.9
/Latch: J4.4, U1.11 (Load)
/OUT0: J3.8, U1.12 (Q7)
/OUT7: J3.1, U1.19 (Q0)
/~OE: J4.1, R1.2, U1.1 (OE)
GND: C1.2, J4.2, U1.10 (GND), U2.7 (GND), U3.7 (GND)
unnamed: D1.1 (K), R1.1
unnamed: J1.2, U3.12
unnamed: J1.3, U3.4
unnamed: J1.4, U3.1
unnamed: J1.5, U2.9
unnamed: J1.6, U2.12
unnamed: J1.7, U2.4
unnamed: J2.2, U3.13
unnamed: J2.3, U3.5
unnamed: J2.4, U3.2
unnamed: J2.5, U2.10
unnamed: J2.6, U2.13
unnamed: J2.7, U2.5
unnamed: J3.2, U1.18 (Q1)
unnamed: J3.3, U1.17 (Q2)
unnamed: J3.4, U1.16 (Q3)
unnamed: J3.5, U1.15 (Q4)
unnamed: J3.6, U1.14 (Q5)
unnamed: J3.7, U1.13 (Q6)
unnamed: U1.2 (D0), U3.8
unnamed: U1.3 (D1), U3.11
unnamed: U1.4 (D2), U3.6
unnamed: U1.5 (D3), U3.3
unnamed: U1.6 (D4), U2.8
unnamed: U1.7 (D5), U2.11
unnamed: U1.8 (D6), U2.6
unnamed: U1.9 (D7), U2.3
VCC: C1.1, D1.2 (A), J4.3, U1.20 (VCC), U2.14 (VCC), U3.14 (VCC)

Notes on the sheet:
Out
Ctrl

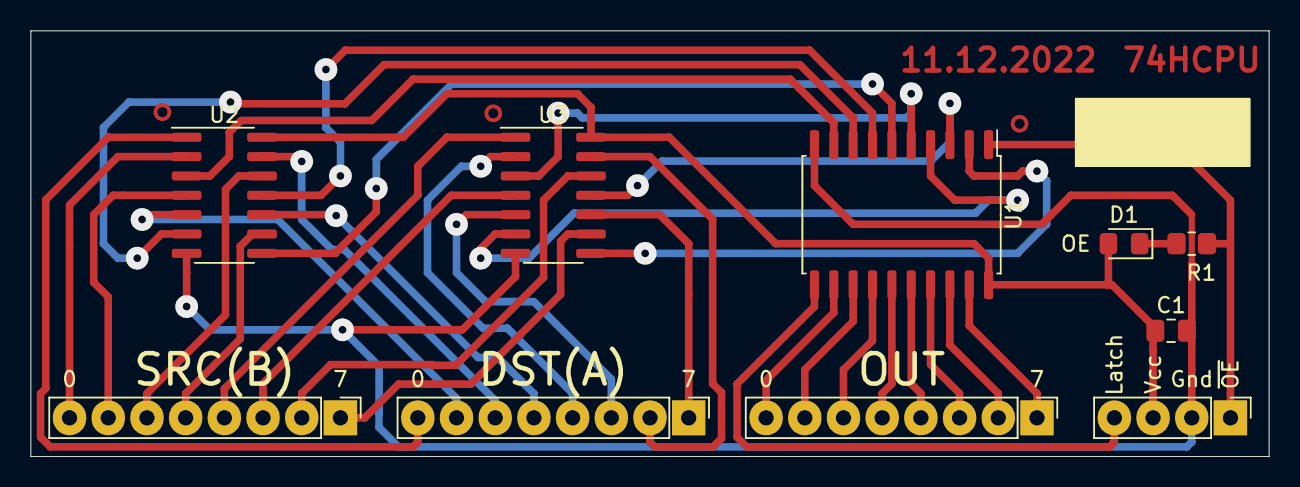
[picture p84: board AND.kicad_pcb from above]

Board: 2 copper layers, 81.3 x 27.9 mm, 10 parts (0 on the bottom side), 37 nets.
