TheJustMoose/74HC-CPU/hard/!MUL/MUL1/MUL1.kicad_pcb

## KiCad design hard/!MUL/MUL1/MUL1.kicad_pcb (2023-06-27)

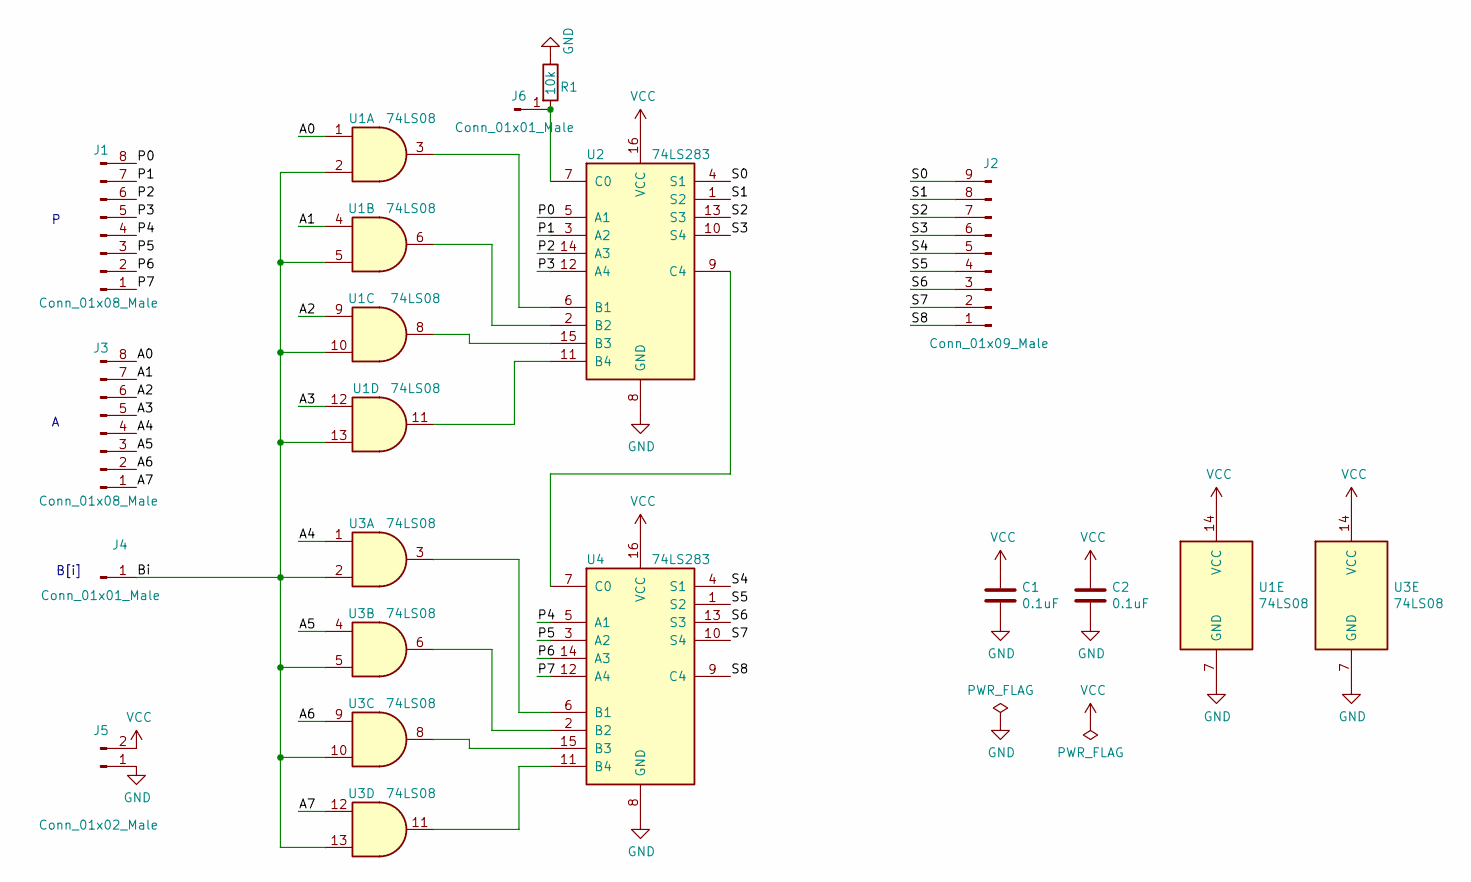
[picture p85: schematic MUL1.sch]

Parts:
C1, C2: 0.1uF; C_Disc_D7.5mm_W5.0mm_P10.00mm
J1, J3: Conn_01x08_Male; PinHeader_1x08_P2.54mm_Horizontal
J2: Conn_01x09_Male; PinHeader_1x09_P2.54mm_Horizontal
J4: Conn_01x01_Male; PinHeader_1x01_P2.54mm_Horizontal
J5: Conn_01x02_Male; PinHeader_1x02_P2.54mm_Horizontal
J6: Conn_01x01_Male; PinHeader_1x01_P2.54mm_Vertical
R1: 10k; R_0805_2012Metric_Pad1.20x1.40mm_HandSolder
U1, U3: 74LS08; DIP-14_W7.62mm_Socket
U2, U4: 74LS283; DIP-16_W7.62mm_Socket

Connections:
/A0: J3.8, U1.1
/A1: J3.7, U1.4
/A2: J3.6, U1.9
/A3: J3.5, U1.12
/A4: J3.4, U3.1
/A5: J3.3, U3.4
/A6: J3.2, U3.9
/A7: J3.1, U3.12
/Bi: J4.1, U1.2, U1.5, U1.10, U1.13, U3.2, U3.5, U3.10, U3.13
/P0: J1.8, U2.5 (A1)
/P1: J1.7, U2.3 (A2)
/P2: J1.6, U2.14 (A3)
/P3: J1.5, U2.12 (A4)
/P4: J1.4, U4.5 (A1)
/P5: J1.3, U4.3 (A2)
/P6: J1.2, U4.14 (A3)
/P7: J1.1, U4.12 (A4)
/S0: J2.9, U2.4 (S1)
/S1: J2.8, U2.1 (S2)
/S2: J2.7, U2.13 (S3)
/S3: J2.6, U2.10 (S4)
/S4: J2.5, U4.4 (S1)
/S5: J2.4, U4.1 (S2)
/S6: J2.3, U4.13 (S3)
/S7: J2.2, U4.10 (S4)
/S8: J2.1, U4.9 (C4)
GND: C1.2, C2.2, J5.1, R1.1, U1.7 (GND), U2.8 (GND), U3.7 (GND), U4.8 (GND)
unnamed: J6.1, R1.2, U2.7 (C0)
unnamed: U1.3, U2.6 (B1)
unnamed: U1.6, U2.2 (B2)
unnamed: U1.8, U2.15 (B3)
unnamed: U1.11, U2.11 (B4)
unnamed: U2.9 (C4), U4.7 (C0)
unnamed: U3.3, U4.6 (B1)
unnamed: U3.6, U4.2 (B2)
unnamed: U3.8, U4.15 (B3)
unnamed: U3.11, U4.11 (B4)
VCC: C1.1, C2.1, J5.2, U1.14 (VCC), U2.16 (VCC), U3.14 (VCC), U4.16 (VCC)

Notes on the sheet:
B[i]

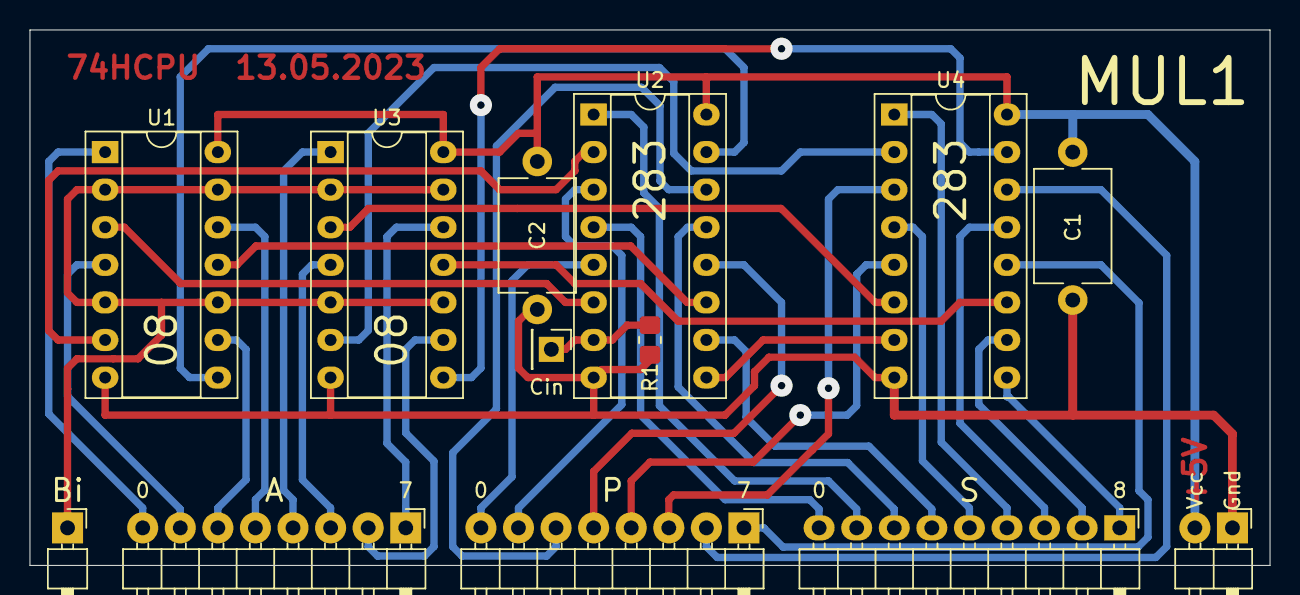
[picture p86: board MUL1.kicad_pcb from above]

Board: 2 copper layers, 83.8 x 36.2 mm, 13 parts (0 on the bottom side), 38 nets.
