TheJustMoose/74HC-CPU/hard/!RAM/RAM.kicad_pcb

## KiCad design hard/!RAM/RAM.kicad_pcb (2024-08-14)

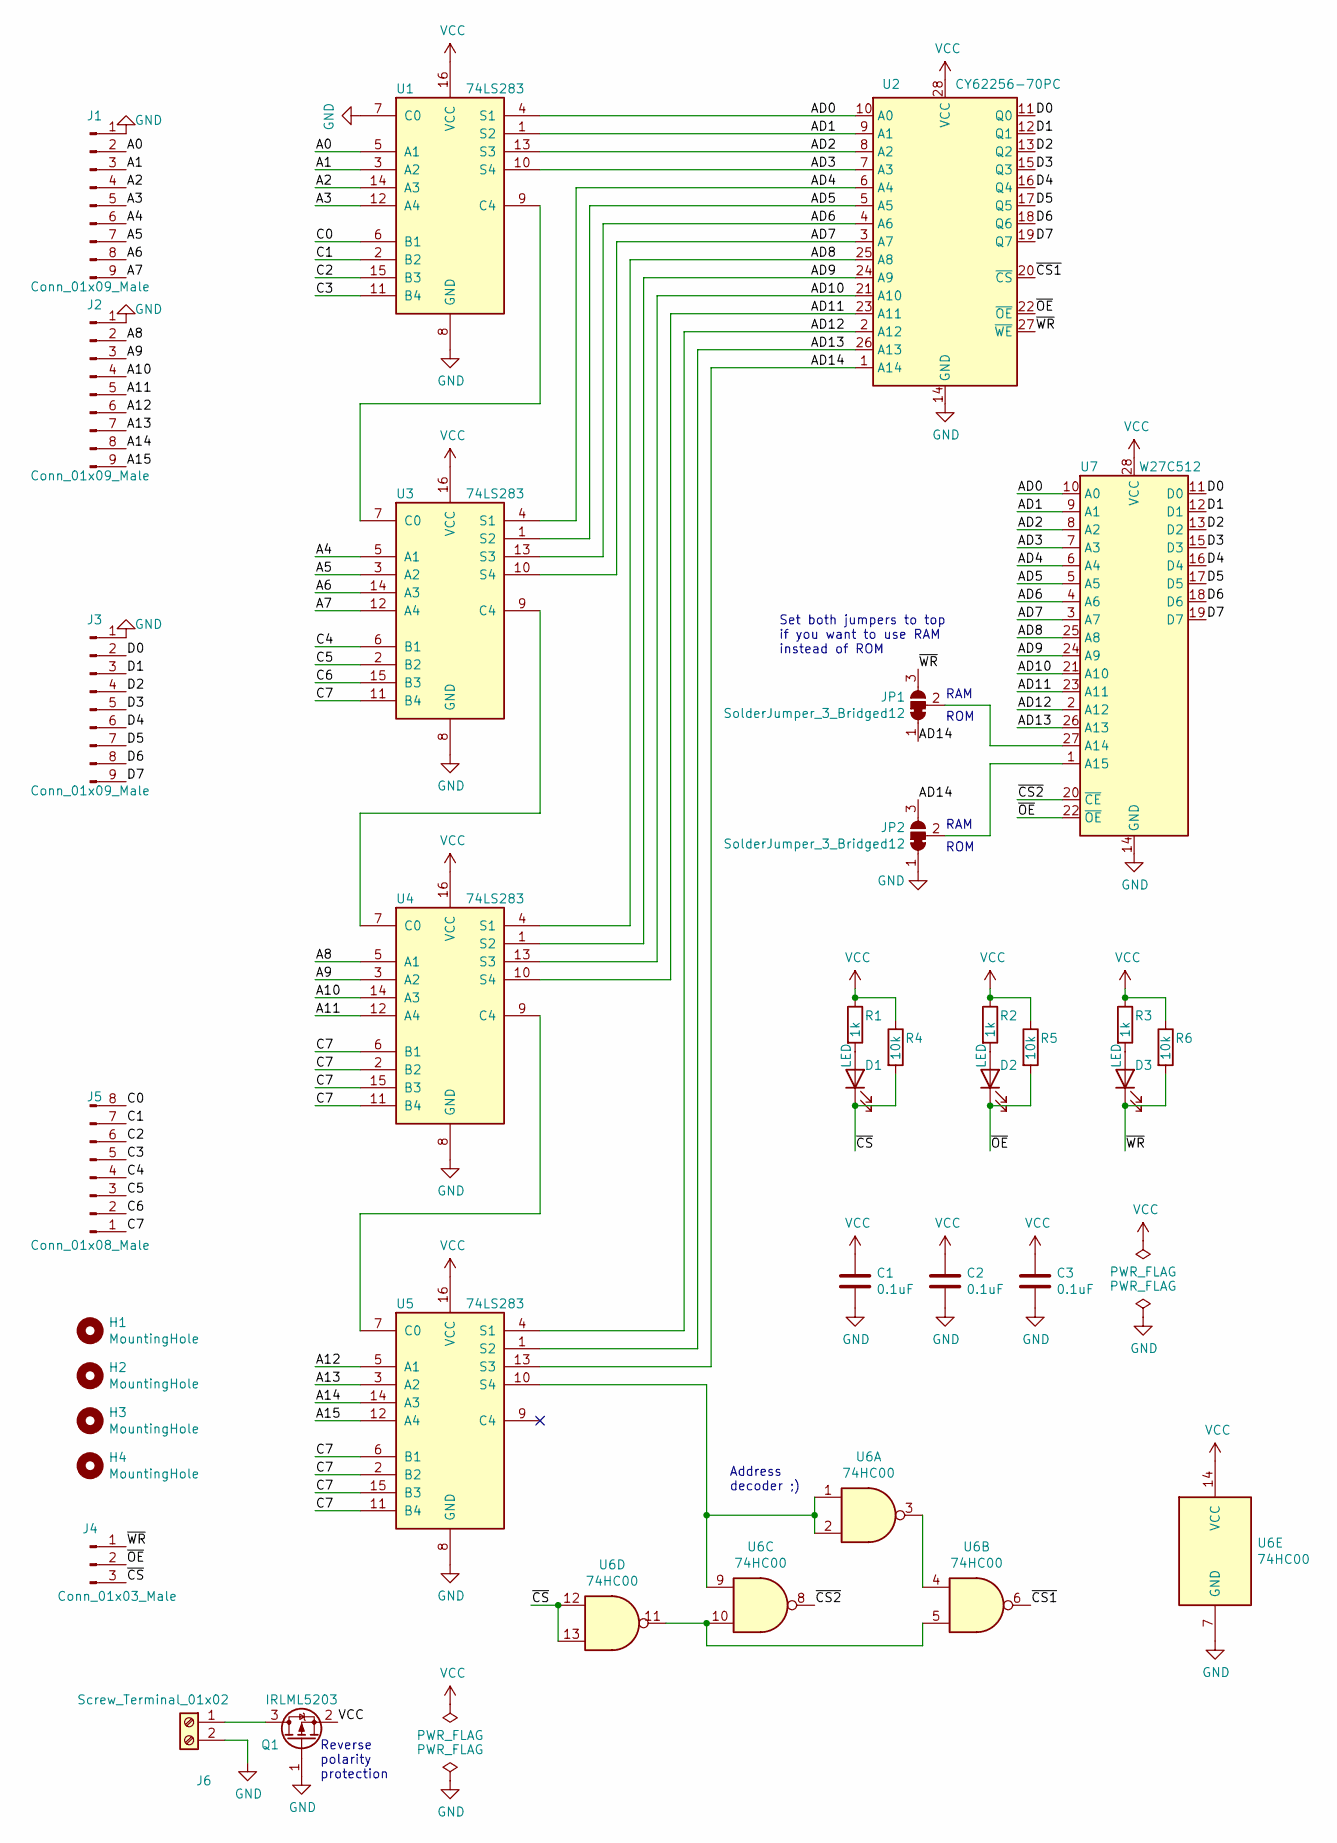
[picture p87: schematic RAM.sch]

Parts:
C1, C2, C3: 0.1uF; C_Disc_D7.5mm_W5.0mm_P10.00mm
D1, D2, D3: LED; LED_Rectangular_W5.0mm_H2.0mm
H1, H2, H3, H4: MountingHole; MountingHole_3.2mm_M3
J1, J2, J3: Conn_01x09_Male; PinHeader_1x09_P2.54mm_Vertical
J4: Conn_01x03_Male; PinHeader_1x03_P2.54mm_Vertical
J5: Conn_01x08_Male; PinHeader_1x08_P2.54mm_Vertical
J6: Screw_Terminal_01x02; TerminalBlock_Phoenix_MKDS-1,5-2_1x02_P5.00mm_Horizontal
JP1, JP2: SolderJumper_3_Bridged12; SolderJumper-3_P1.3mm_Open_Pad1.0x1.5mm_NumberLabels
Q1: IRLML5203; SOT-23
R1, R2, R3: 1k; R_0805_2012Metric_Pad1.20x1.40mm_HandSolder
R4, R5, R6: 10k; R_0805_2012Metric_Pad1.20x1.40mm_HandSolder
U1, U3, U4, U5: 74LS283; DIP-16_W7.62mm
U2: CY62256-70PC; DIP-28_W15.24mm
U6: 74HC00; DIP-14_W7.62mm
U7: W27C512; DIP-28_W15.24mm

Connections:
/A0: J1.2, U1.5 (A1)
/A1: J1.3, U1.3 (A2)
/A2: J1.4, U1.14 (A3)
/A3: J1.5, U1.12 (A4)
/A4: J1.6, U3.5 (A1)
/A5: J1.7, U3.3 (A2)
/A6: J1.8, U3.14 (A3)
/A7: J1.9, U3.12 (A4)
/A8: J2.2, U4.5 (A1)
/A9: J2.3, U4.3 (A2)
/A10: J2.4, U4.14 (A3)
/A11: J2.5, U4.12 (A4)
/A12: J2.6, U5.5 (A1)
/A13: J2.7, U5.3 (A2)
/A14: J2.8, U5.14 (A3)
/A15: J2.9, U5.12 (A4)
/AD0: U1.4 (S1), U2.10 (A0), U7.10 (A0)
/AD1: U1.1 (S2), U2.9 (A1), U7.9 (A1)
/AD2: U1.13 (S3), U2.8 (A2), U7.8 (A2)
/AD3: U1.10 (S4), U2.7 (A3), U7.7 (A3)
/AD4: U2.6 (A4), U3.4 (S1), U7.6 (A4)
/AD5: U2.5 (A5), U3.1 (S2), U7.5 (A5)
/AD6: U2.4 (A6), U3.13 (S3), U7.4 (A6)
/AD7: U2.3 (A7), U3.10 (S4), U7.3 (A7)
/AD8: U2.25 (A8), U4.4 (S1), U7.25 (A8)
/AD9: U2.24 (A9), U4.1 (S2), U7.24 (A9)
/AD10: U2.21 (A10), U4.13 (S3), U7.21 (A10)
/AD11: U2.23 (A11), U4.10 (S4), U7.23 (A11)
/AD12: U2.2 (A12), U5.4 (S1), U7.2 (A12)
/AD13: U2.26 (A13), U5.1 (S2), U7.26 (A13)
/AD14: JP1.1 (A), JP2.3 (B), U2.1 (A14), U5.13 (S3)
/C0: J5.8, U1.6 (B1)
/C1: J5.7, U1.2 (B2)
/C2: J5.6, U1.15 (B3)
/C3: J5.5, U1.11 (B4)
/C4: J5.4, U3.6 (B1)
/C5: J5.3, U3.2 (B2)
/C6: J5.2, U3.15 (B3)
/C7: J5.1, U3.11 (B4), U4.2 (B2), U4.6 (B1), U4.11 (B4), U4.15 (B3), U5.2 (B2), U5.6 (B1), U5.11 (B4), U5.15 (B3)
/D0: J3.2, U2.11 (Q0), U7.11 (D0)
/D1: J3.3, U2.12 (Q1), U7.12 (D1)
/D2: J3.4, U2.13 (Q2), U7.13 (D2)
/D3: J3.5, U2.15 (Q3), U7.15 (D3)
/D4: J3.6, U2.16 (Q4), U7.16 (D4)
/D5: J3.7, U2.17 (Q5), U7.17 (D5)
/D6: J3.8, U2.18 (Q6), U7.18 (D6)
/D7: J3.9, U2.19 (Q7), U7.19 (D7)
/~CS: D1.1 (K), J4.3, R4.2, U6.12, U6.13
/~CS1: U2.20 (~CS), U6.6
/~CS2: U6.8, U7.20 (~CE)
/~OE: D2.1 (K), J4.2, R5.2, U2.22 (~OE), U7.22 (~OE)
/~WR: D3.1 (K), J4.1, JP1.3 (B), R6.2, U2.27 (~WE)
GND: C1.2, C2.2, C3.2, J1.1, J2.1, J3.1, J6.2, JP2.1 (A), Q1.1 (G), U1.7 (C0), U1.8 (GND), U2.14 (GND), U3.8 (GND), U4.8 (GND), U5.8 (GND), U6.7 (GND), U7.14 (GND)
unnamed: D1.2 (A), R1.2
unnamed: D2.2 (A), R2.2
unnamed: D3.2 (A), R3.2
unnamed: J6.1, Q1.3 (D)
unnamed: JP1.2 (C), U7.27 (A14)
unnamed: JP2.2 (C), U7.1 (A15)
unnamed: U1.9 (C4), U3.7 (C0)
unnamed: U3.9 (C4), U4.7 (C0)
unnamed: U4.9 (C4), U5.7 (C0)
unnamed: U5.10 (S4), U6.1, U6.2, U6.9
unnamed: U6.3, U6.4
unnamed: U6.5, U6.10, U6.11
VCC: C1.1, C2.1, C3.1, Q1.2 (S), R1.1, R2.1, R3.1, R4.1, R5.1, R6.1, U1.16 (VCC), U2.28 (VCC), U3.16 (VCC), U4.16 (VCC), U5.16 (VCC), U6.14 (VCC), U7.28 (VCC)

Notes on the sheet:
Address decoder ;)
RAM
ROM
Set both jumpers to top if you want to use RAM instead of ROM
Reverse polarity protection

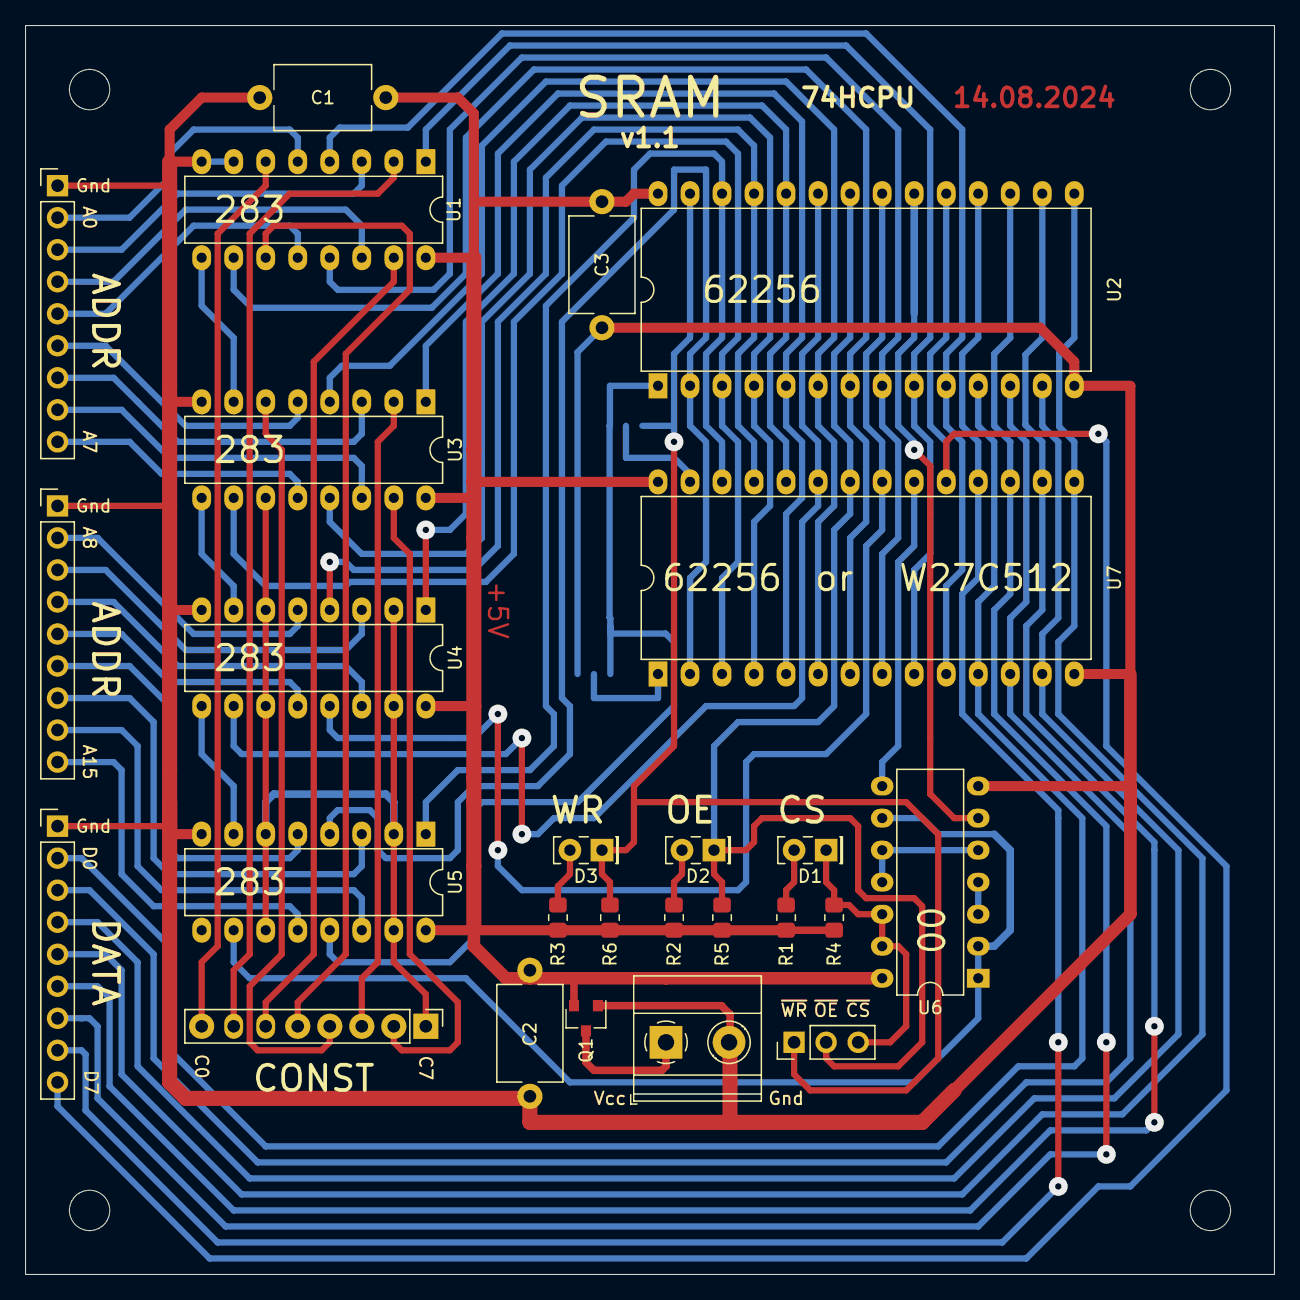
[picture p88: board RAM.kicad_pcb from above]

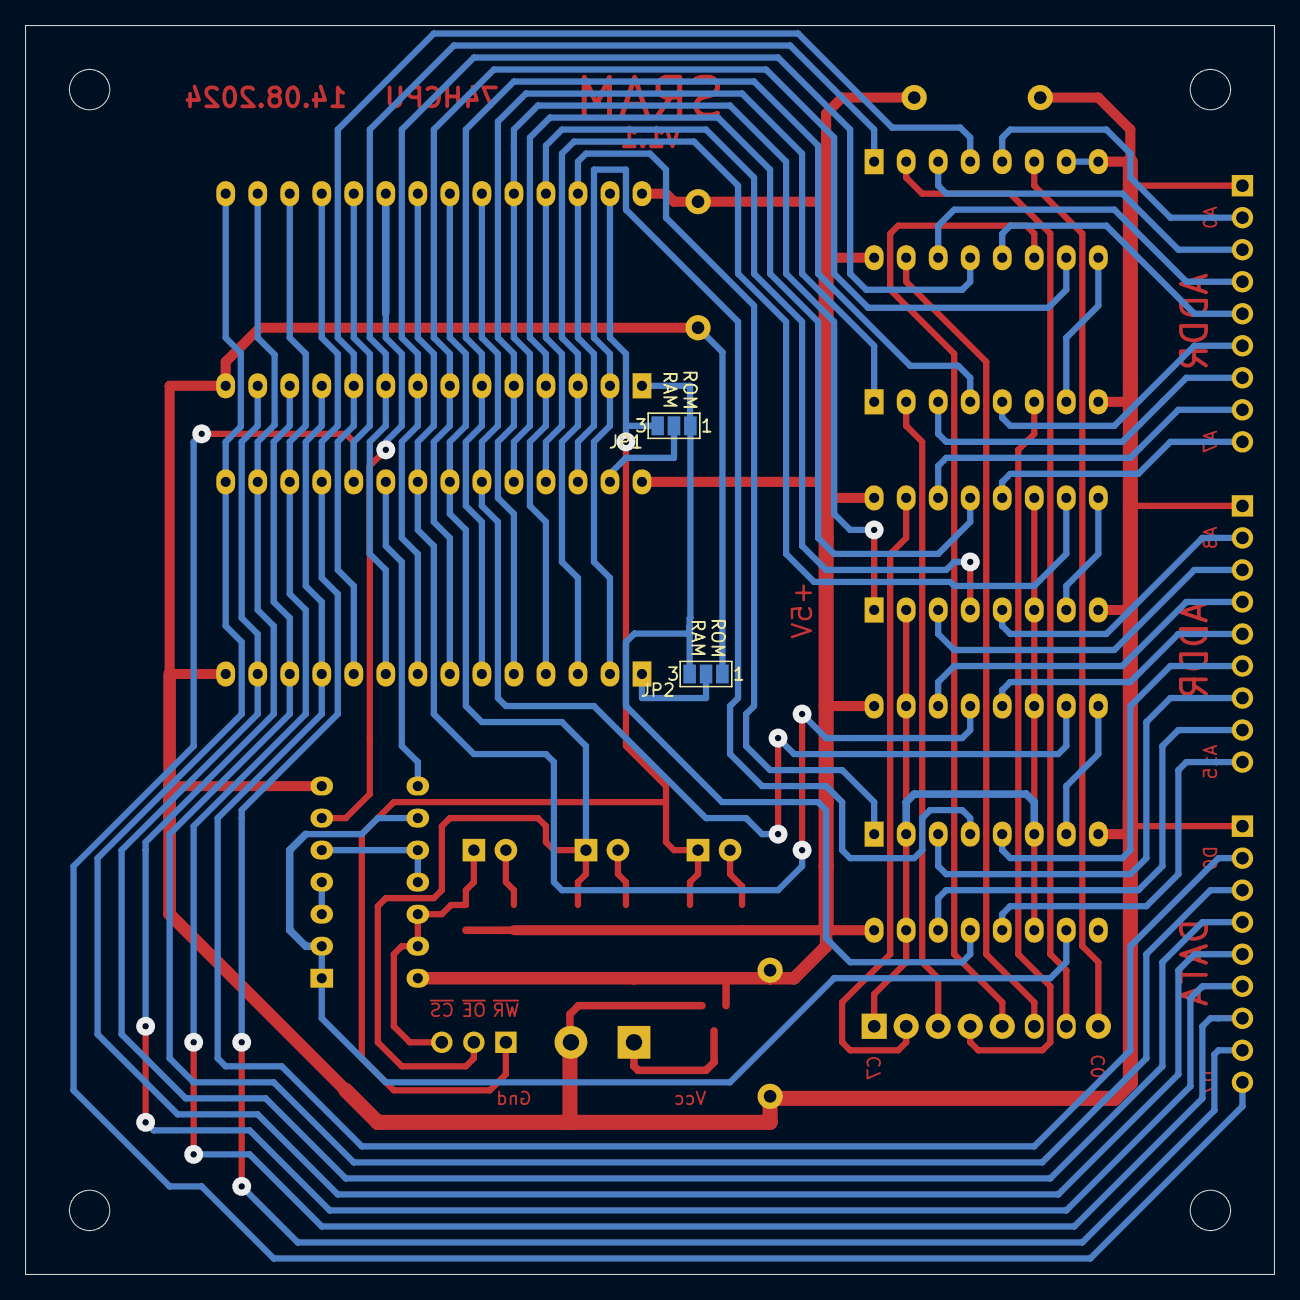
[picture p89: board RAM.kicad_pcb from below]

Board: 2 copper layers, 99.1 x 99.1 mm, 32 parts (2 on the bottom side), 66 nets.
