TheJustMoose/74HC-CPU/hard/!ALU/ADD/ADD.kicad_pcb

## KiCad design hard/!ALU/ADD/ADD.kicad_pcb (2023-07-06)

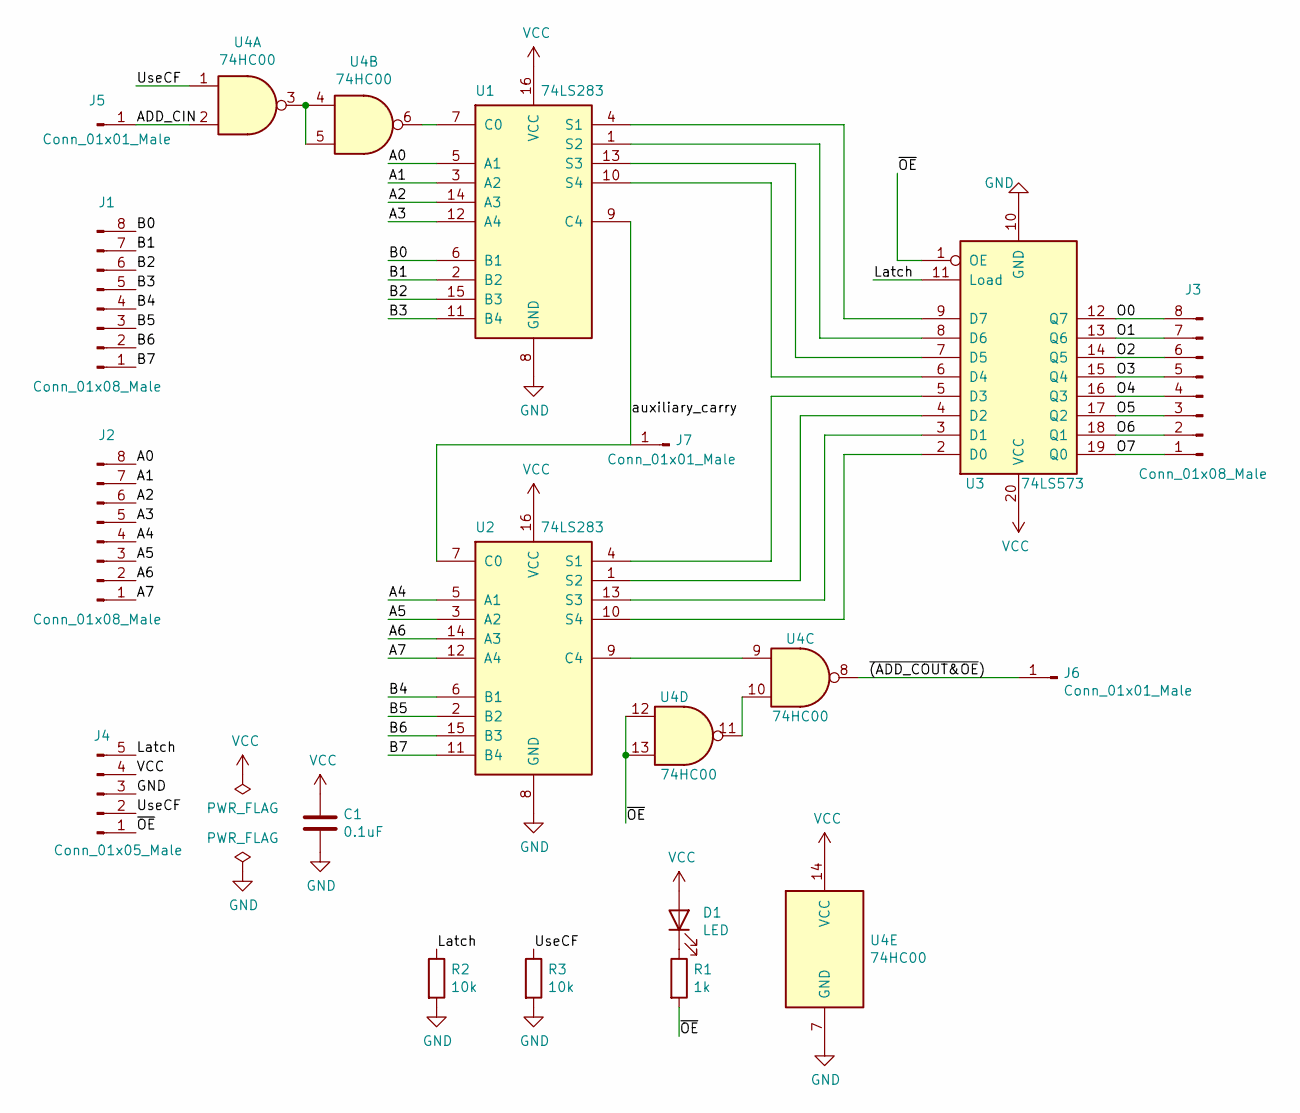
[picture p90: schematic ADD.sch]

Parts:
C1: 0.1uF; C_0805_2012Metric_Pad1.18x1.45mm_HandSolder
D1: LED; LED_0805_2012Metric_Pad1.15x1.40mm_HandSolder
J1, J2, J3: Conn_01x08_Male; PinHeader_1x08_P2.54mm_Horizontal
J4: Conn_01x05_Male; PinHeader_1x05_P2.54mm_Horizontal
J5, J6, J7: Conn_01x01_Male; PinHeader_1x01_P2.54mm_Vertical
R1: 1k; R_0805_2012Metric_Pad1.20x1.40mm_HandSolder
R2, R3: 10k; R_0805_2012Metric_Pad1.20x1.40mm_HandSolder
U1, U2: 74LS283; DIP-16_W7.62mm
U3: 74LS573; DIP-20_W7.62mm
U4: 74HC00; DIP-14_W7.62mm

Connections:
/A0: J2.8, U1.5 (A1)
/A1: J2.7, U1.3 (A2)
/A2: J2.6, U1.14 (A3)
/A3: J2.5, U1.12 (A4)
/A4: J2.4, U2.5 (A1)
/A5: J2.3, U2.3 (A2)
/A6: J2.2, U2.14 (A3)
/A7: J2.1, U2.12 (A4)
/ADD_CIN: J5.1, U4.2
/B0: J1.8, U1.6 (B1)
/B1: J1.7, U1.2 (B2)
/B2: J1.6, U1.15 (B3)
/B3: J1.5, U1.11 (B4)
/B4: J1.4, U2.6 (B1)
/B5: J1.3, U2.2 (B2)
/B6: J1.2, U2.15 (B3)
/B7: J1.1, U2.11 (B4)
/Latch: J4.5, R2.1, U3.11 (Load)
/O0: J3.8, U3.12 (Q7)
/O1: J3.7, U3.13 (Q6)
/O2: J3.6, U3.14 (Q5)
/O3: J3.5, U3.15 (Q4)
/O4: J3.4, U3.16 (Q3)
/O5: J3.3, U3.17 (Q2)
/O6: J3.2, U3.18 (Q1)
/O7: J3.1, U3.19 (Q0)
/UseCF: J4.2, R3.1, U4.1
/auxiliary_carry: J7.1, U1.9 (C4), U2.7 (C0)
/~(ADD_COUT&OE): J6.1, U4.8
/~OE: J4.1, R1.2, U3.1 (OE), U4.12, U4.13
GND: C1.2, J4.3, R2.2, R3.2, U1.8 (GND), U2.8 (GND), U3.10 (GND), U4.7 (GND)
unnamed: D1.1 (K), R1.1
unnamed: U1.1 (S2), U3.8 (D6)
unnamed: U1.4 (S1), U3.9 (D7)
unnamed: U1.7 (C0), U4.6
unnamed: U1.10 (S4), U3.6 (D4)
unnamed: U1.13 (S3), U3.7 (D5)
unnamed: U2.1 (S2), U3.4 (D2)
unnamed: U2.4 (S1), U3.5 (D3)
unnamed: U2.9 (C4), U4.9
unnamed: U2.10 (S4), U3.2 (D0)
unnamed: U2.13 (S3), U3.3 (D1)
unnamed: U4.3, U4.4, U4.5
unnamed: U4.10, U4.11
VCC: C1.1, D1.2 (A), J4.4, U1.16 (VCC), U2.16 (VCC), U3.20 (VCC), U4.14 (VCC)
