TheJustMoose/74HC-CPU/hard/!ALU/ADD/ADD.kicad_pcb

## KiCad design hard/!ALU/ADD/ADD.kicad_pcb (continued)

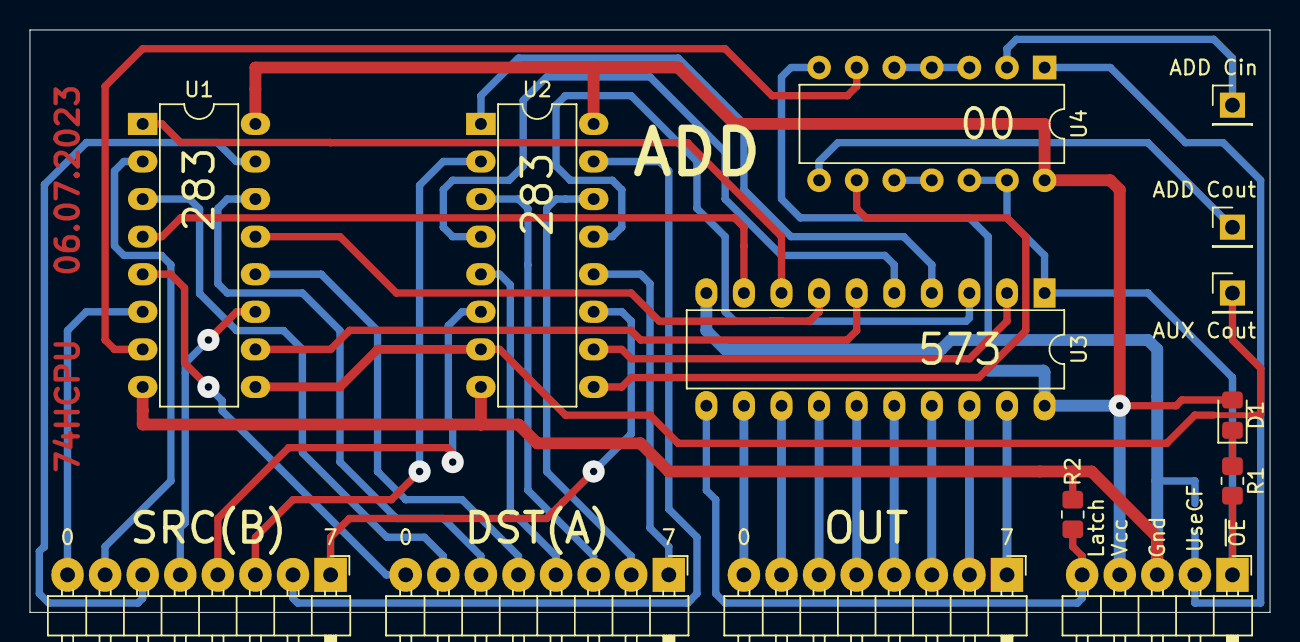
[picture p91: board ADD.kicad_pcb from above]

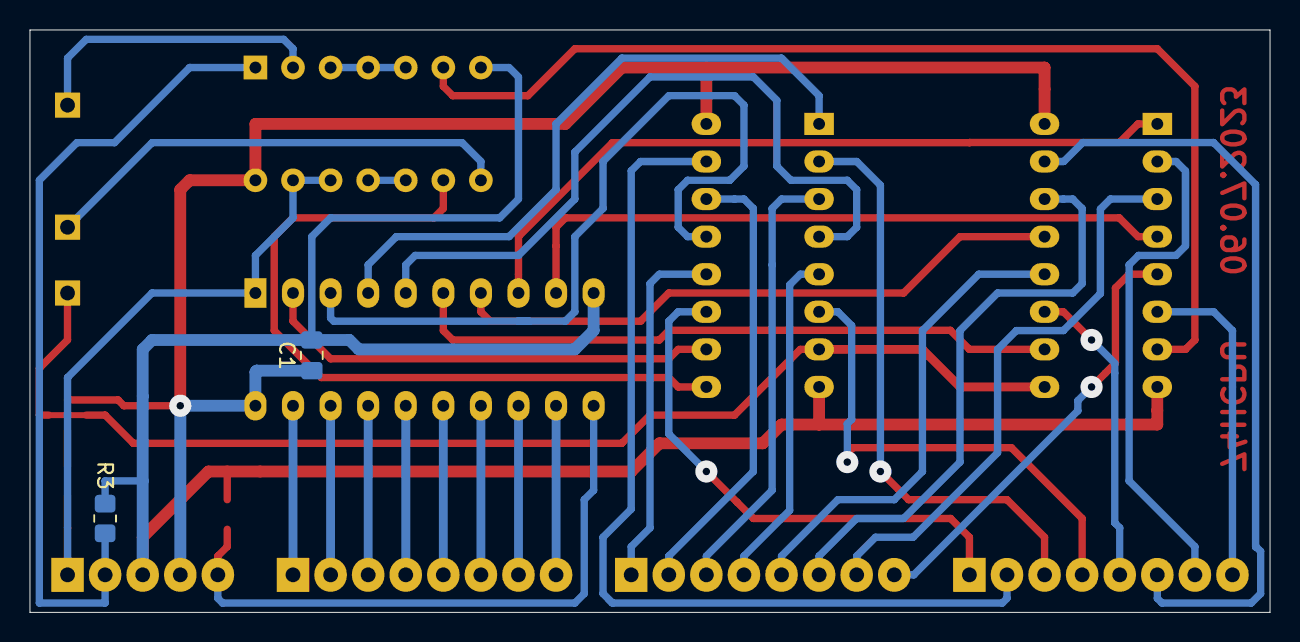
[picture p92: board ADD.kicad_pcb from below]

Board: 2 copper layers, 83.8 x 39.4 mm, 16 parts (2 on the bottom side), 45 nets.
