TheJustMoose/74HC-CPU/hard/INV-BB/INV.kicad_pcb

## KiCad design hard/INV-BB/INV.kicad_pcb (2023-07-12)

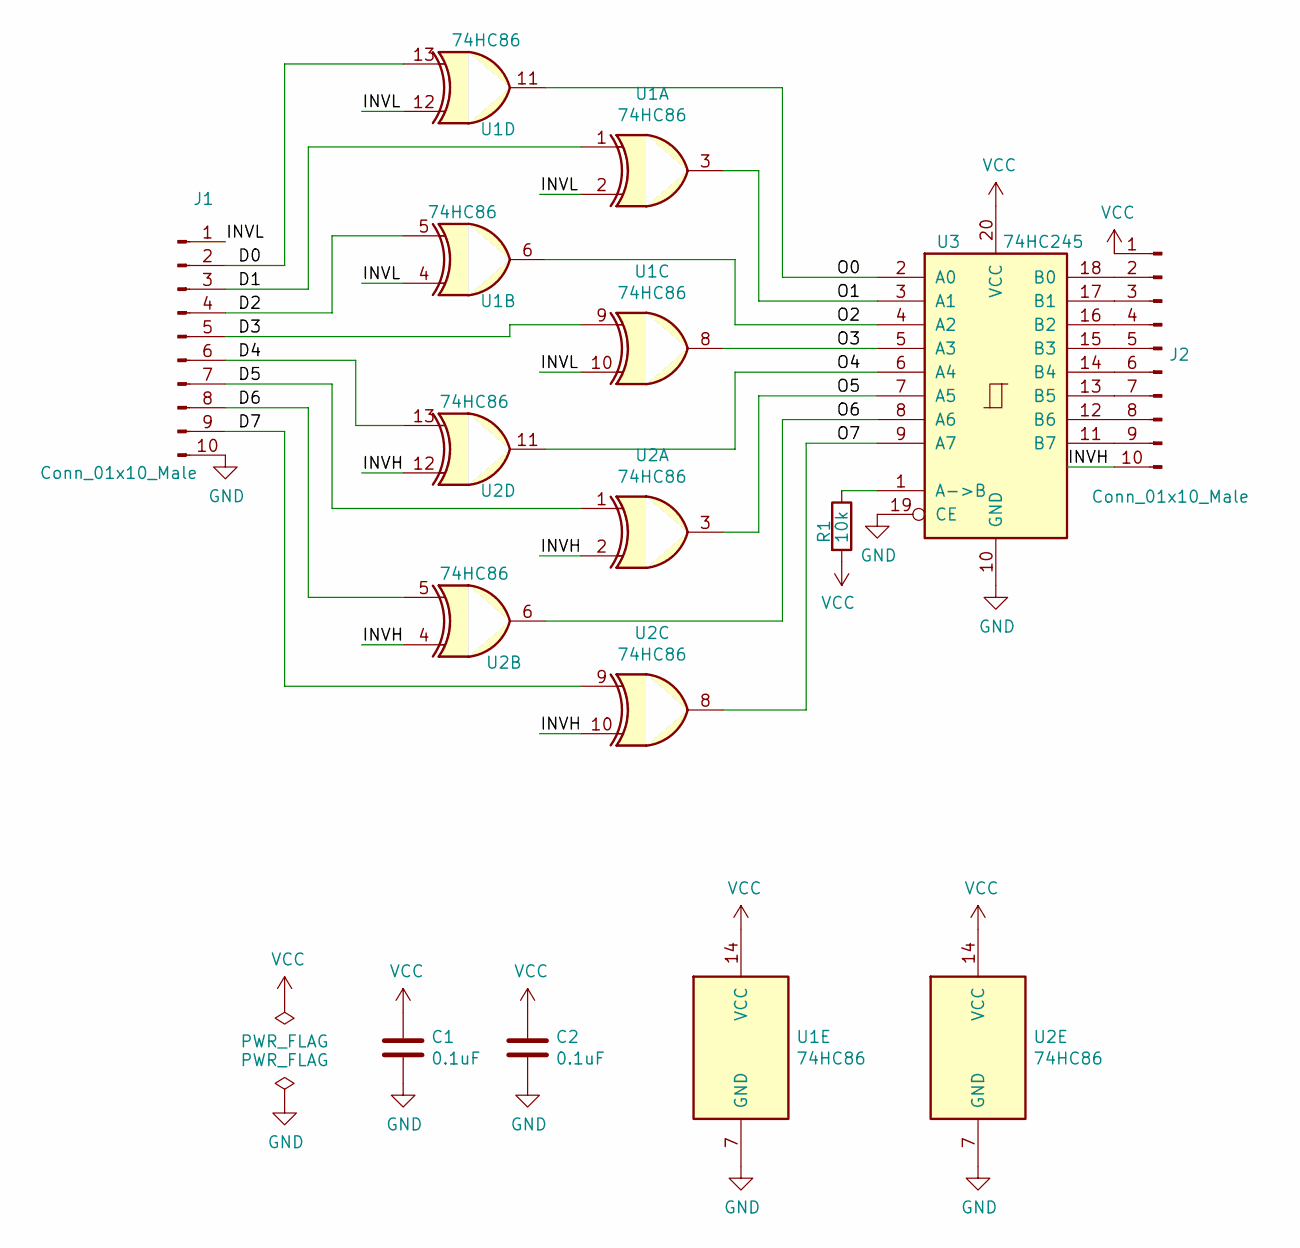
[picture p93: schematic INV.sch]

Parts:
C1: 0.1uF; C_0805_2012Metric_Pad1.18x1.45mm_HandSolder
C2: 0.1uF; C_Axial_L3.8mm_D2.6mm_P12.50mm_Horizontal
J1, J2: Conn_01x10_Male; PinHeader_1x10_P2.54mm_Vertical
R1: 10k; R_0805_2012Metric_Pad1.20x1.40mm_HandSolder
U1, U2: 74HC86; SO-14_3.9x8.65mm_P1.27mm
U3: 74HC245; SOP-20_7.5x12.8mm_P1.27mm

Connections:
/D0: J1.2, U1.13
/D1: J1.3, U1.1
/D2: J1.4, U1.5
/D3: J1.5, U1.9
/D4: J1.6, U2.13
/D5: J1.7, U2.1
/D6: J1.8, U2.5
/D7: J1.9, U2.9
/INVH: J2.10, U2.2, U2.4, U2.10, U2.12
/INVL: J1.1, U1.2, U1.4, U1.10, U1.12
/O0: U1.11, U3.2 (A0)
/O1: U1.3, U3.3 (A1)
/O2: U1.6, U3.4 (A2)
/O3: U1.8, U3.5 (A3)
/O4: U2.11, U3.6 (A4)
/O5: U2.3, U3.7 (A5)
/O6: U2.6, U3.8 (A6)
/O7: U2.8, U3.9 (A7)
GND: C1.2, C2.2, J1.10, U1.7 (GND), U2.7 (GND), U3.10 (GND), U3.19 (CE)
unnamed: J2.2, U3.18 (B0)
unnamed: J2.3, U3.17 (B1)
unnamed: J2.4, U3.16 (B2)
unnamed: J2.5, U3.15 (B3)
unnamed: J2.6, U3.14 (B4)
unnamed: J2.7, U3.13 (B5)
unnamed: J2.8, U3.12 (B6)
unnamed: J2.9, U3.11 (B7)
unnamed: R1.1, U3.1 (A->B)
VCC: C1.1, C2.1, J2.1, R1.2, U1.14 (VCC), U2.14 (VCC), U3.20 (VCC)

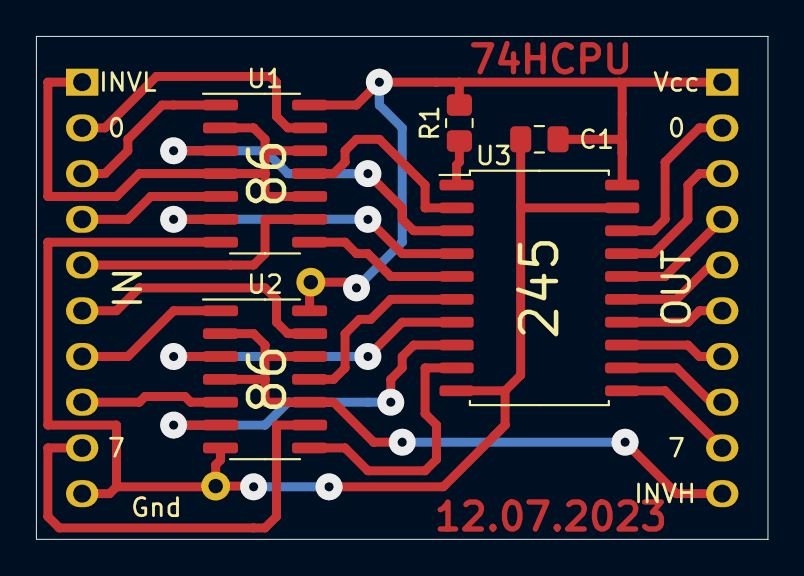
[picture p94: board hard/INV-BB/INV.kicad_pcb from above]

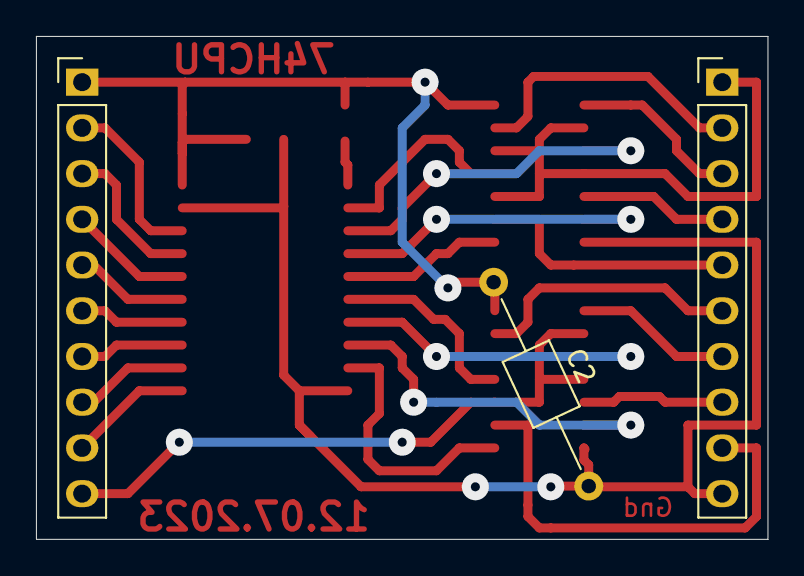
[picture p95: board hard/INV-BB/INV.kicad_pcb from below]

Board: 2 copper layers, 40.6 x 27.9 mm, 8 parts (3 on the bottom side), 29 nets.
