TheJustMoose/74HC-CPU/hard/MUX4x1-v4.2/MUX4x1.kicad_pcb

## KiCad design hard/MUX4x1-v4.2/MUX4x1.kicad_pcb (2023-06-30)

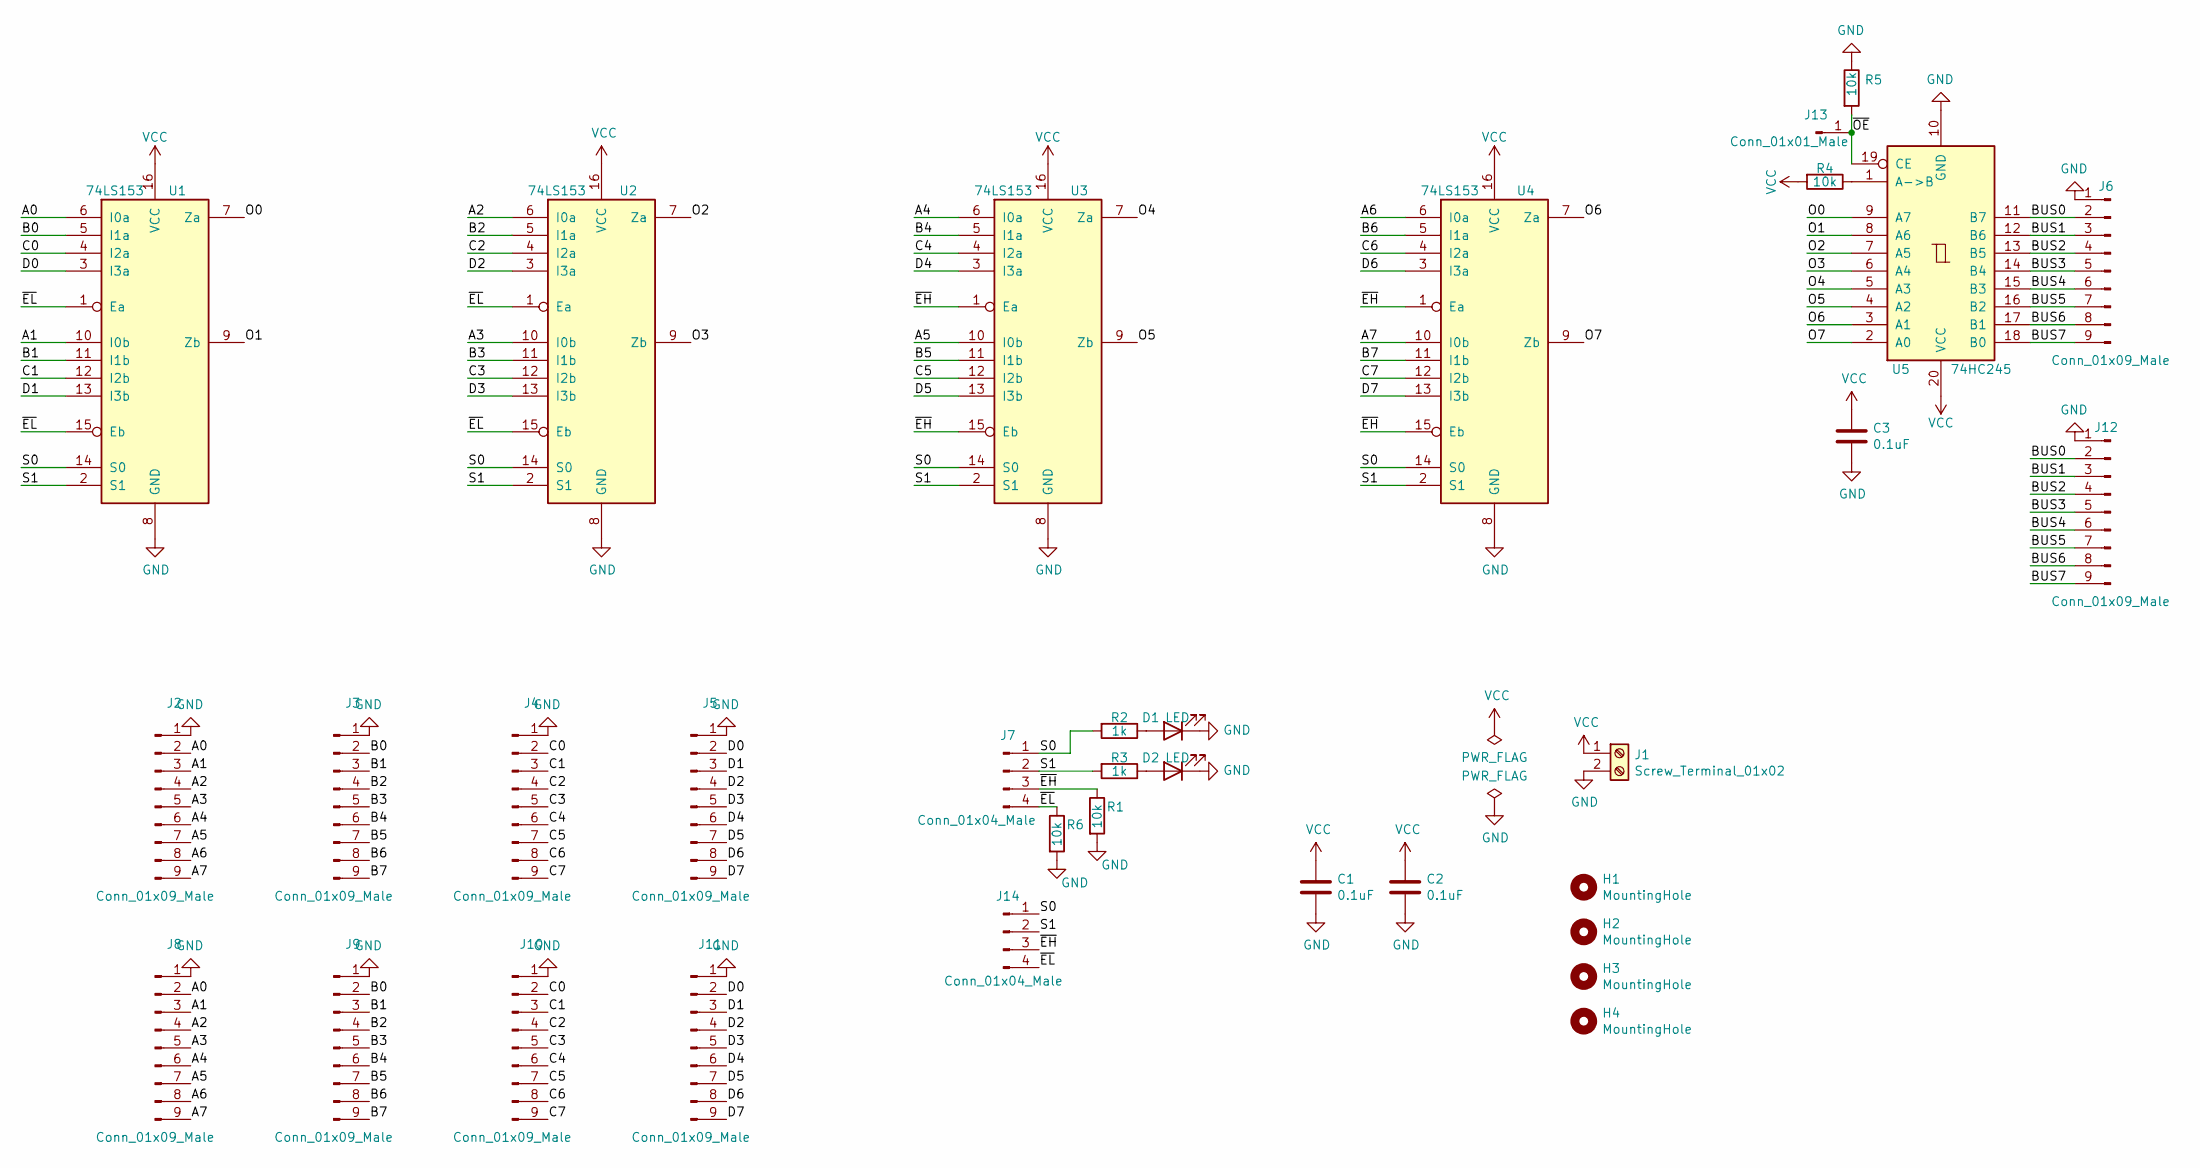
[picture p96: schematic MUX4x1.sch]

Parts:
C1, C2, C3: 0.1uF; C_0805_2012Metric_Pad1.18x1.45mm_HandSolder
D1, D2: LED; LED_0805_2012Metric_Pad1.15x1.40mm_HandSolder
H1, H2, H3, H4: MountingHole; MountingHole_3.2mm_M3
J1: Screw_Terminal_01x02; TerminalBlock_Phoenix_PT-1,5-2-5.0-H_1x02_P5.00mm_Horizontal
J2, J3, J4, J5, J6, J8, J9, J10, J11, J12: Conn_01x09_Male; PinHeader_1x09_P2.54mm_Vertical
J7, J14: Conn_01x04_Male; PinHeader_1x04_P2.54mm_Vertical
J13: Conn_01x01_Male; PinHeader_1x01_P2.54mm_Vertical
R1, R4, R5, R6: 10k; R_0805_2012Metric_Pad1.20x1.40mm_HandSolder
R2, R3: 1k; R_0805_2012Metric_Pad1.20x1.40mm_HandSolder
U1, U2, U3, U4: 74LS153; DIP-16_W7.62mm_Socket
U5: 74HC245; DIP-20_W7.62mm_Socket

Connections:
/A0: J2.2, J8.2, U1.6 (I0a)
/A1: J2.3, J8.3, U1.10 (I0b)
/A2: J2.4, J8.4, U2.6 (I0a)
/A3: J2.5, J8.5, U2.10 (I0b)
/A4: J2.6, J8.6, U3.6 (I0a)
/A5: J2.7, J8.7, U3.10 (I0b)
/A6: J2.8, J8.8, U4.6 (I0a)
/A7: J2.9, J8.9, U4.10 (I0b)
/B0: J3.2, J9.2, U1.5 (I1a)
/B1: J3.3, J9.3, U1.11 (I1b)
/B2: J3.4, J9.4, U2.5 (I1a)
/B3: J3.5, J9.5, U2.11 (I1b)
/B4: J3.6, J9.6, U3.5 (I1a)
/B5: J3.7, J9.7, U3.11 (I1b)
/B6: J3.8, J9.8, U4.5 (I1a)
/B7: J3.9, J9.9, U4.11 (I1b)
/BUS0: J6.2, J12.2, U5.11 (B7)
/BUS1: J6.3, J12.3, U5.12 (B6)
/BUS2: J6.4, J12.4, U5.13 (B5)
/BUS3: J6.5, J12.5, U5.14 (B4)
/BUS4: J6.6, J12.6, U5.15 (B3)
/BUS5: J6.7, J12.7, U5.16 (B2)
/BUS6: J6.8, J12.8, U5.17 (B1)
/BUS7: J6.9, J12.9, U5.18 (B0)
/C0: J4.2, J10.2, U1.4 (I2a)
/C1: J4.3, J10.3, U1.12 (I2b)
/C2: J4.4, J10.4, U2.4 (I2a)
/C3: J4.5, J10.5, U2.12 (I2b)
/C4: J4.6, J10.6, U3.4 (I2a)
/C5: J4.7, J10.7, U3.12 (I2b)
/C6: J4.8, J10.8, U4.4 (I2a)
/C7: J4.9, J10.9, U4.12 (I2b)
/D0: J5.2, J11.2, U1.3 (I3a)
/D1: J5.3, J11.3, U1.13 (I3b)
/D2: J5.4, J11.4, U2.3 (I3a)
/D3: J5.5, J11.5, U2.13 (I3b)
/D4: J5.6, J11.6, U3.3 (I3a)
/D5: J5.7, J11.7, U3.13 (I3b)
/D6: J5.8, J11.8, U4.3 (I3a)
/D7: J5.9, J11.9, U4.13 (I3b)
/O0: U1.7 (Za), U5.9 (A7)
/O1: U1.9 (Zb), U5.8 (A6)
/O2: U2.7 (Za), U5.7 (A5)
/O3: U2.9 (Zb), U5.6 (A4)
/O4: U3.7 (Za), U5.5 (A3)
/O5: U3.9 (Zb), U5.4 (A2)
/O6: U4.7 (Za), U5.3 (A1)
/O7: U4.9 (Zb), U5.2 (A0)
/S0: J7.1, J14.1, R2.2, U1.14 (S0), U2.14 (S0), U3.14 (S0), U4.14 (S0)
/S1: J7.2, J14.2, R3.2, U1.2 (S1), U2.2 (S1), U3.2 (S1), U4.2 (S1)
/~EH: J7.3, J14.3, R1.1, U3.1 (Ea), U3.15 (Eb), U4.1 (Ea), U4.15 (Eb)
/~EL: J7.4, J14.4, R6.1, U1.1 (Ea), U1.15 (Eb), U2.1 (Ea), U2.15 (Eb)
/~OE: J13.1, R5.2, U5.19 (CE)
GND: C1.2, C2.2, C3.2, D1.1 (K), D2.1 (K), J1.2, J2.1, J3.1, J4.1, J5.1, J6.1, J8.1, J9.1, J10.1, J11.1, J12.1, R1.2, R5.1, R6.2, U1.8 (GND), U2.8 (GND), U3.8 (GND), U4.8 (GND), U5.10 (GND)
unnamed: D1.2 (A), R2.1
unnamed: D2.2 (A), R3.1
unnamed: R4.1, U5.1 (A->B)
VCC: C1.1, C2.1, C3.1, J1.1, R4.2, U1.16 (VCC), U2.16 (VCC), U3.16 (VCC), U4.16 (VCC), U5.20 (VCC)

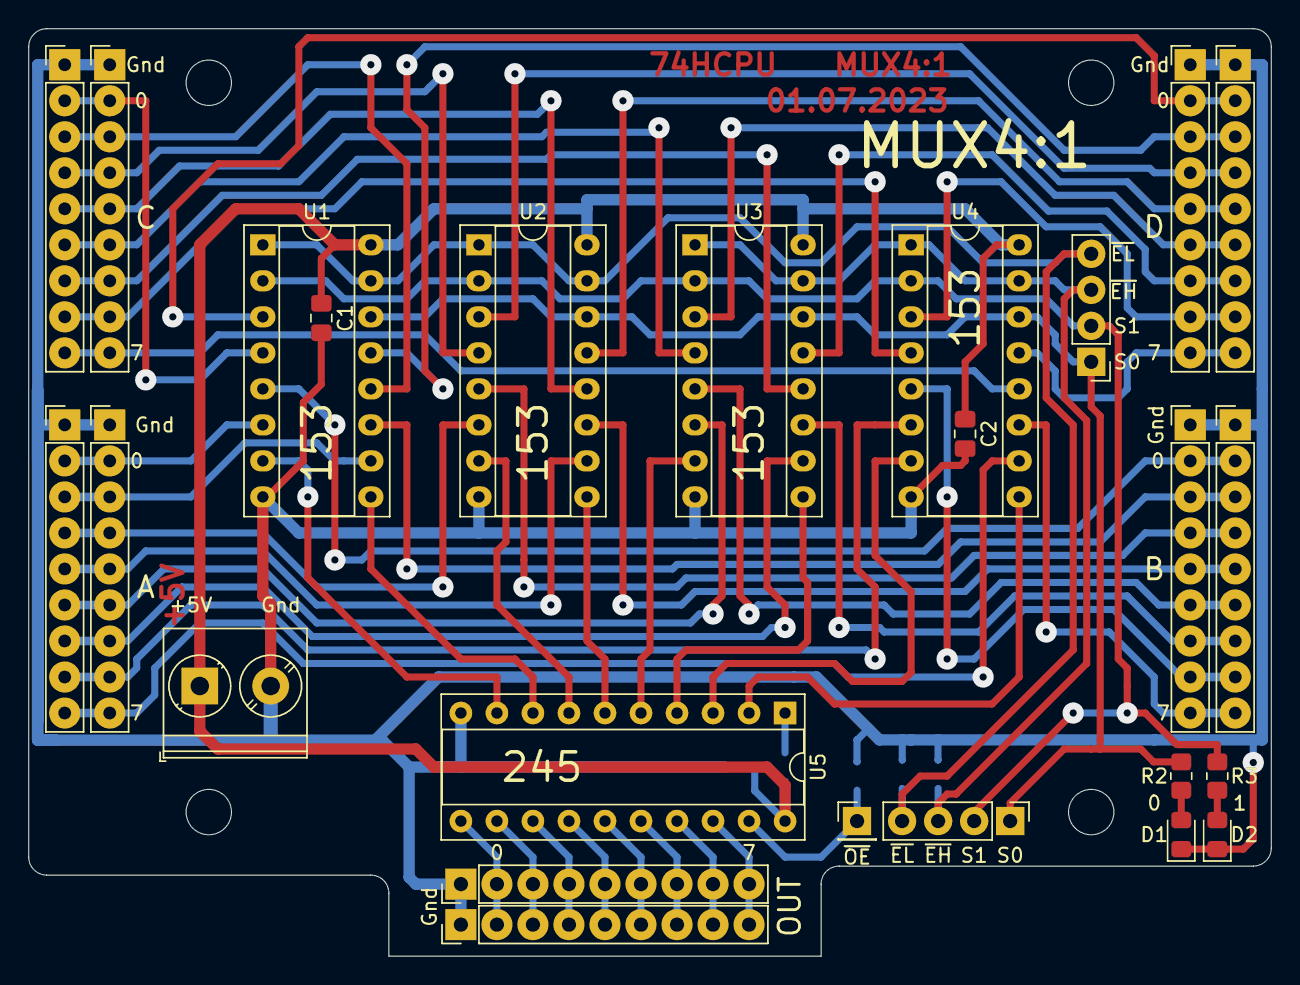
[picture p97: board MUX4x1.kicad_pcb from above]

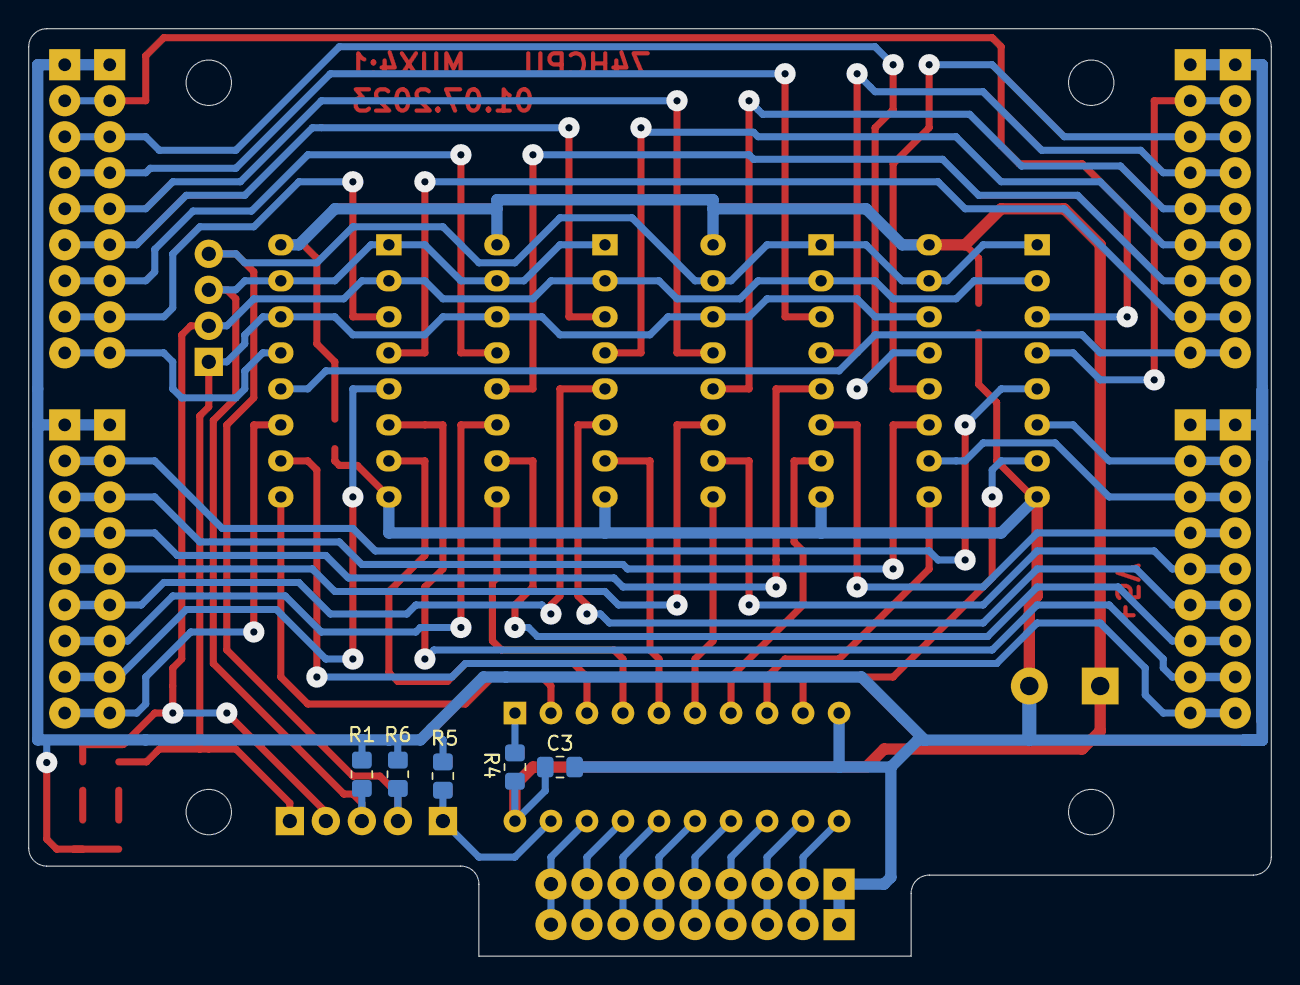
[picture p98: board MUX4x1.kicad_pcb from below]

Board: 2 copper layers, 87.6 x 65.4 mm, 34 parts (5 on the bottom side), 58 nets.
