TheJustMoose/74HC-CPU/hard/MUX2x1/MUX2x1.kicad_pcb

## KiCad design hard/MUX2x1/MUX2x1.kicad_pcb (2022-10-22)

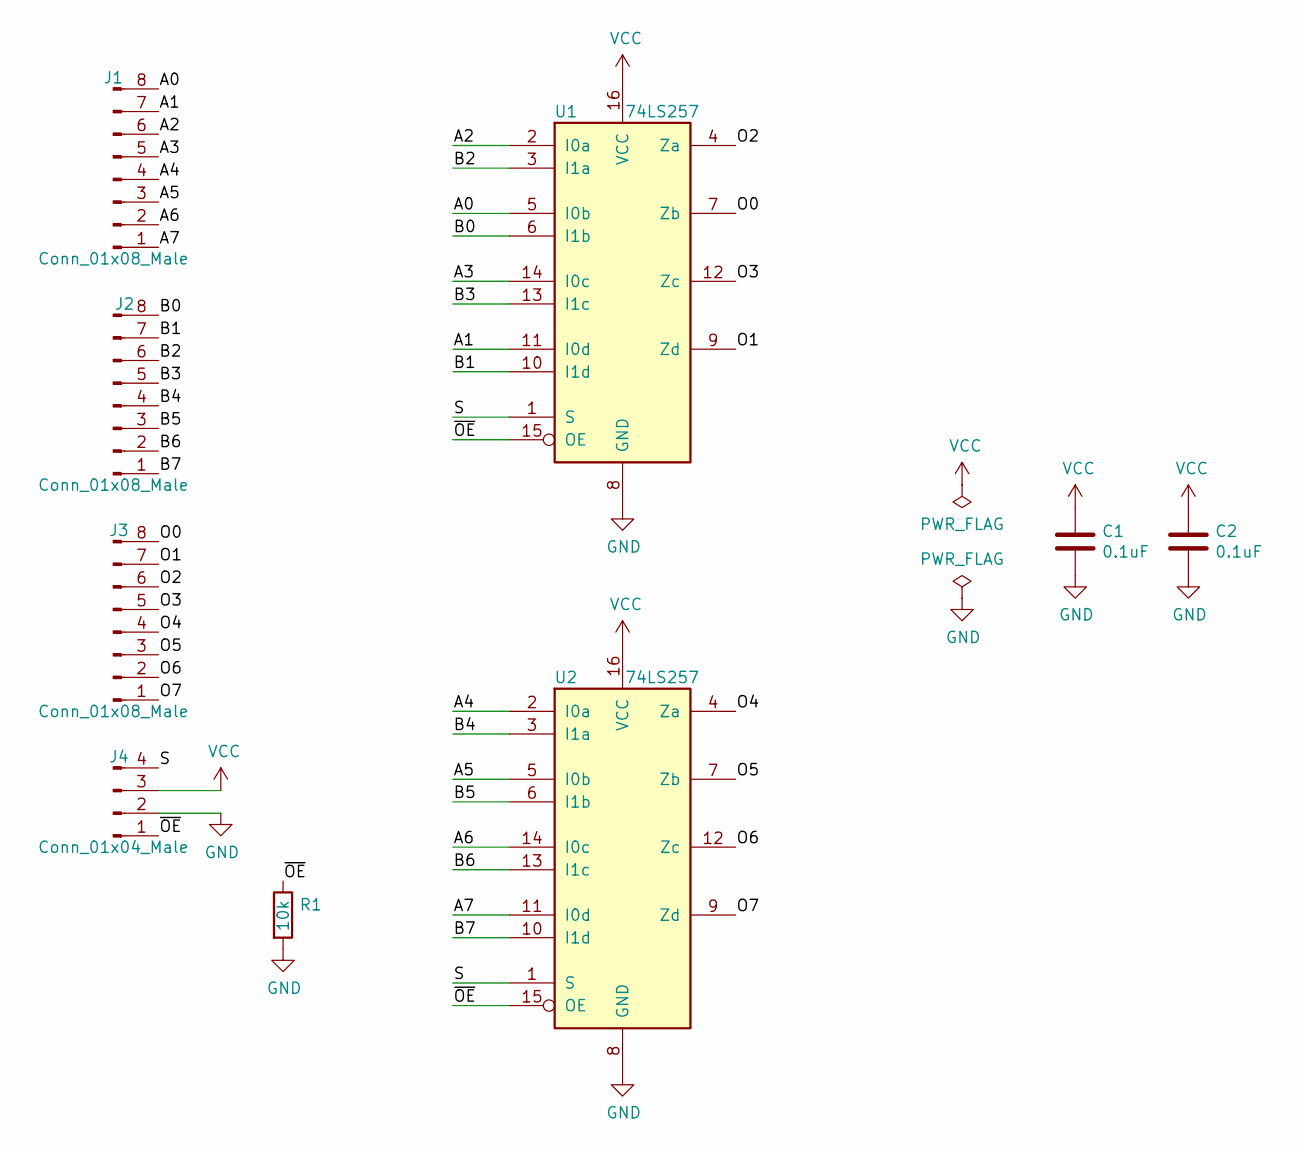
[picture p99: schematic MUX2x1.sch]

Parts:
C1, C2: 0.1uF; C_0805_2012Metric_Pad1.18x1.45mm_HandSolder
J1, J2, J3: Conn_01x08_Male; PinHeader_1x08_P2.54mm_Horizontal
J4: Conn_01x04_Male; PinHeader_1x04_P2.54mm_Horizontal
R1: 10k; R_0805_2012Metric_Pad1.20x1.40mm_HandSolder
U1, U2: 74LS257; DIP-16_W7.62mm_Socket

Connections:
/A0: J1.8, U1.5 (I0b)
/A1: J1.7, U1.11 (I0d)
/A2: J1.6, U1.2 (I0a)
/A3: J1.5, U1.14 (I0c)
/A4: J1.4, U2.2 (I0a)
/A5: J1.3, U2.5 (I0b)
/A6: J1.2, U2.14 (I0c)
/A7: J1.1, U2.11 (I0d)
/B0: J2.8, U1.6 (I1b)
/B1: J2.7, U1.10 (I1d)
/B2: J2.6, U1.3 (I1a)
/B3: J2.5, U1.13 (I1c)
/B4: J2.4, U2.3 (I1a)
/B5: J2.3, U2.6 (I1b)
/B6: J2.2, U2.13 (I1c)
/B7: J2.1, U2.10 (I1d)
/O0: J3.8, U1.7 (Zb)
/O1: J3.7, U1.9 (Zd)
/O2: J3.6, U1.4 (Za)
/O3: J3.5, U1.12 (Zc)
/O4: J3.4, U2.4 (Za)
/O5: J3.3, U2.7 (Zb)
/O6: J3.2, U2.12 (Zc)
/O7: J3.1, U2.9 (Zd)
/S: J4.4, U1.1 (S), U2.1 (S)
/~OE: J4.1, R1.1, U1.15 (OE), U2.15 (OE)
GND: C1.2, C2.2, J4.2, R1.2, U1.8 (GND), U2.8 (GND)
VCC: C1.1, C2.1, J4.3, U1.16 (VCC), U2.16 (VCC)

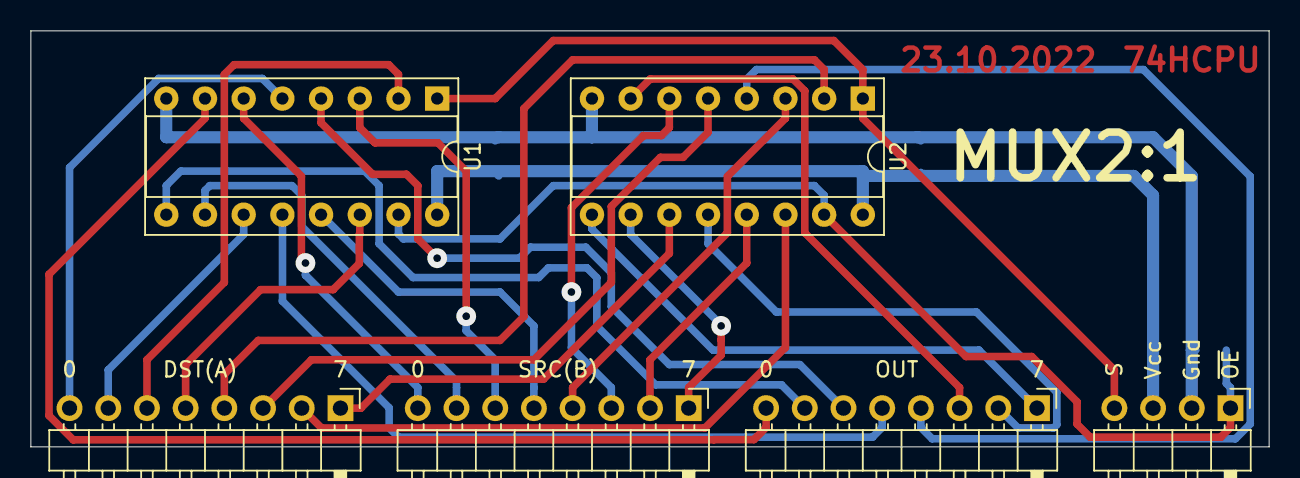
[picture p100: board MUX2x1.kicad_pcb from above]

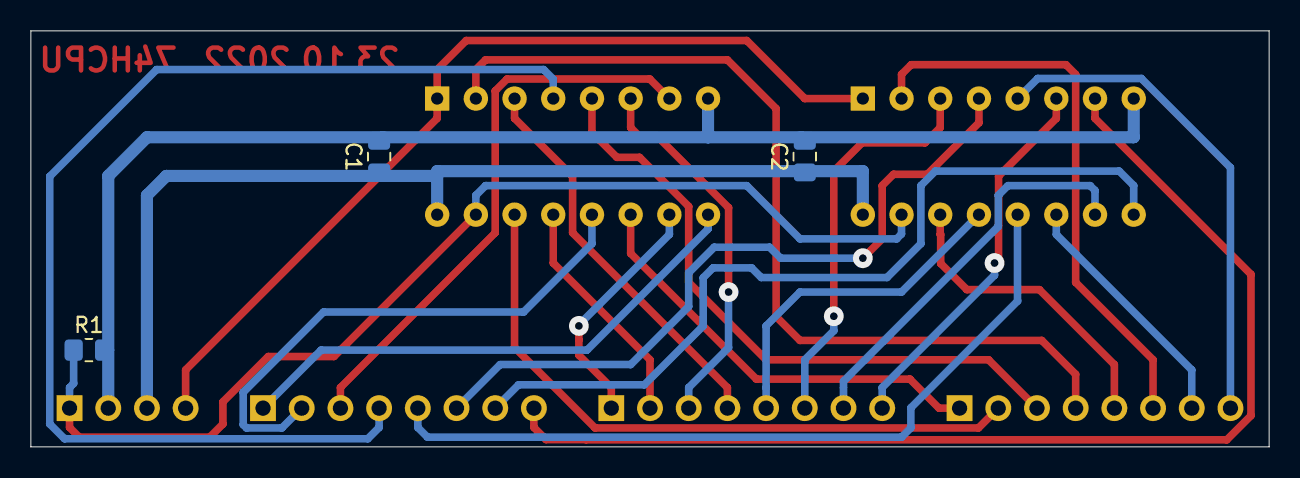
[picture p101: board MUX2x1.kicad_pcb from below]

Board: 2 copper layers, 81.3 x 27.3 mm, 9 parts (3 on the bottom side), 28 nets.
