TheJustMoose/74HC-CPU/hard/!ALU/ALU_PCB/ALU.kicad_pcb

## KiCad design hard/!ALU/ALU_PCB/ALU.kicad_pcb (2024-08-14)

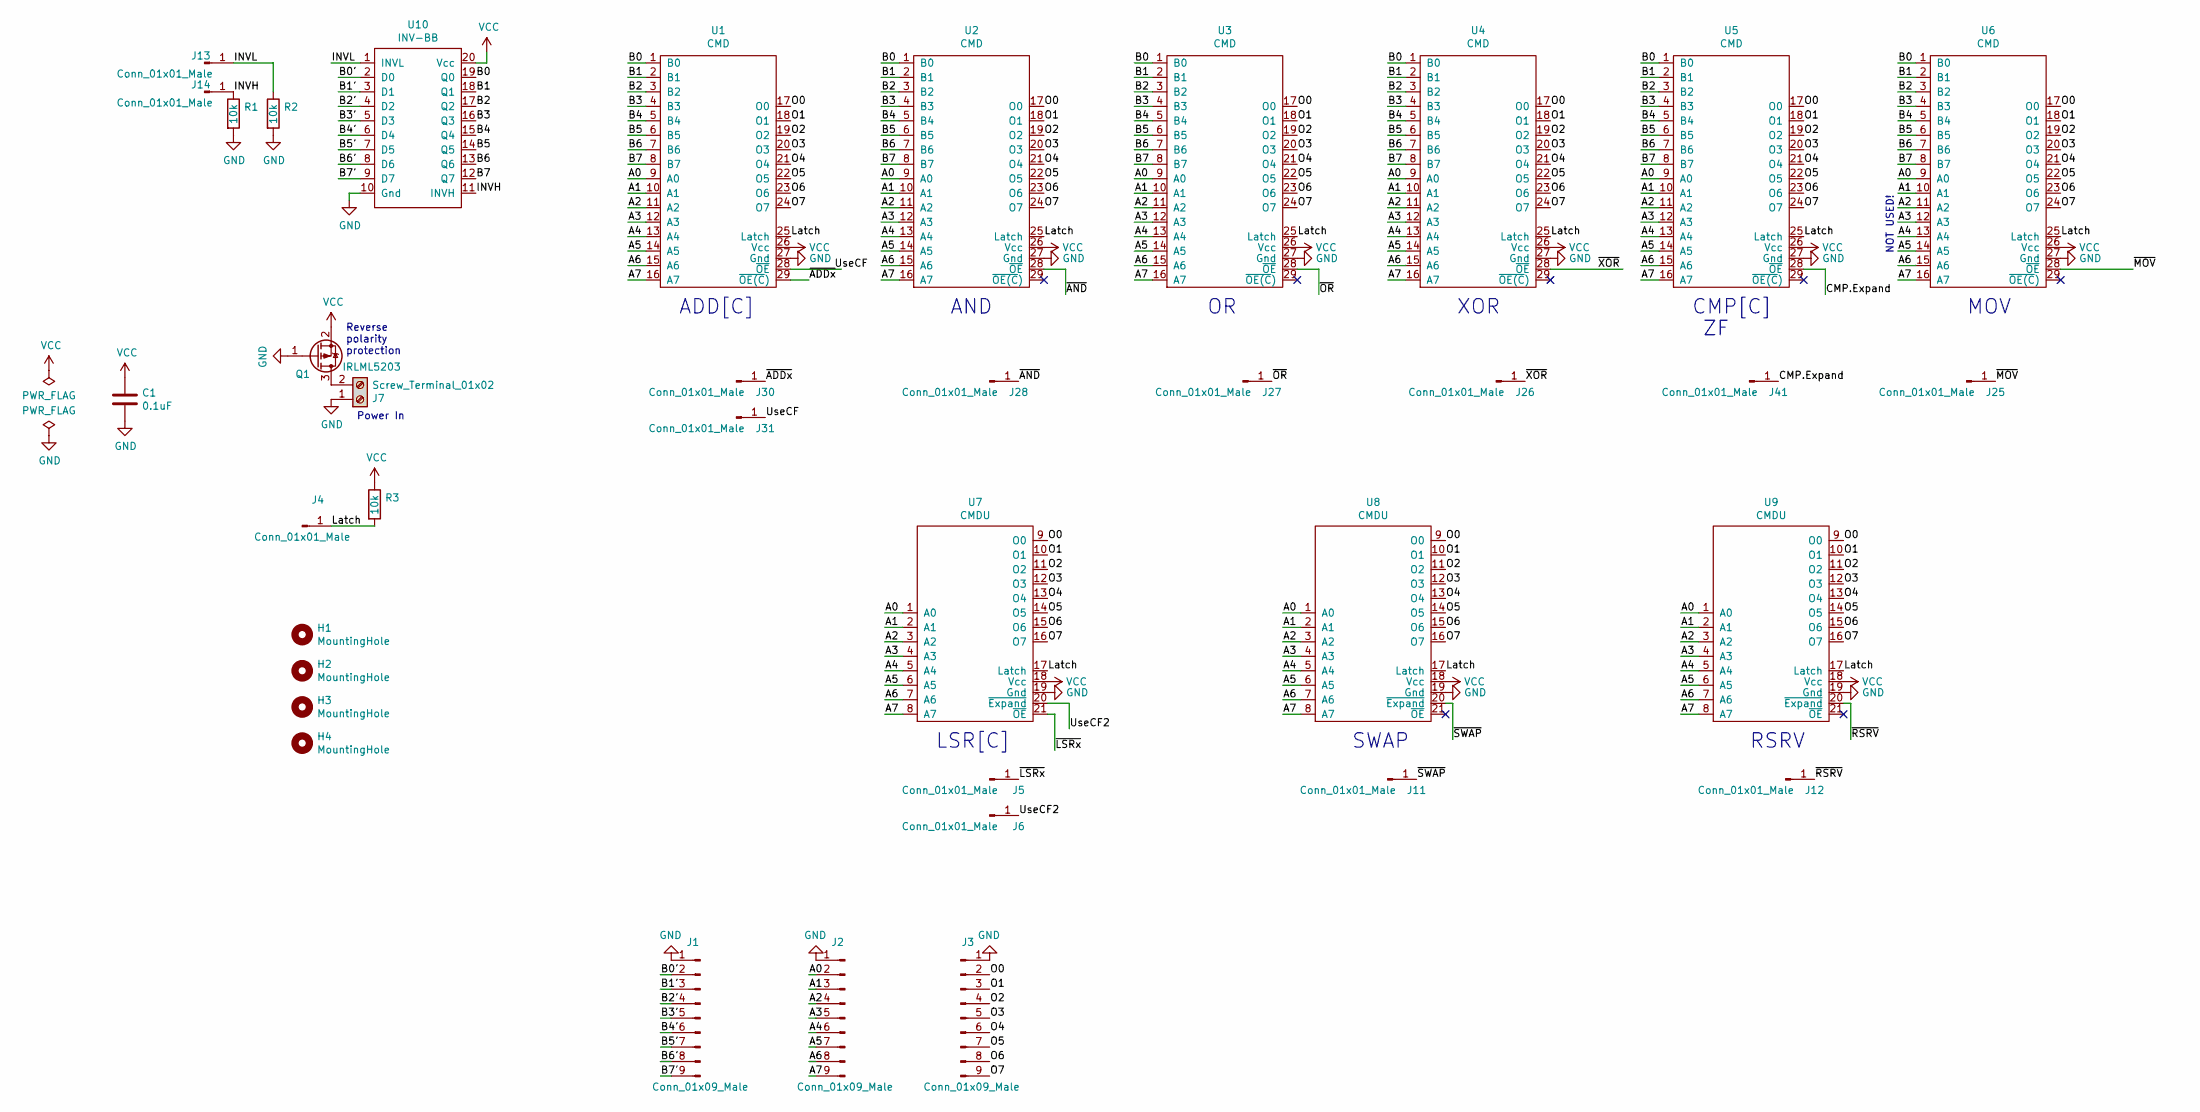
[picture p102: schematic ALU.sch]

Parts:
C1: 0.1uF; C_0805_2012Metric_Pad1.18x1.45mm_HandSolder
H1, H2, H3, H4: MountingHole; MountingHole_3.2mm_M3
J1, J2, J3: Conn_01x09_Male; PinHeader_1x09_P2.54mm_Vertical
J4, J5, J6, J11, J12, J13, J14, J25, J26, J27, J28, J30, J31, J41: Conn_01x01_Male; PinHeader_1x01_P2.54mm_Vertical
J7: Screw_Terminal_01x02; TerminalBlock_Phoenix_MKDS-1,5-2_1x02_P5.00mm_Horizontal
Q1: IRLML5203; SOT-23
R1, R2, R3: 10k; R_0805_2012Metric_Pad1.20x1.40mm_HandSolder
U1, U2, U3, U4, U5, U6: CMD
U7, U8, U9: CMDU
U10: INV-BB; INV-B

Connections:
/A0: J2.2, U1.9 (A0), U2.9 (A0), U3.9 (A0), U4.9 (A0), U5.9 (A0), U6.9 (A0), U7.1 (A0), U8.1 (A0), U9.1 (A0)
/A1: J2.3, U1.10 (A1), U2.10 (A1), U3.10 (A1), U4.10 (A1), U5.10 (A1), U6.10 (A1), U7.2 (A1), U8.2 (A1), U9.2 (A1)
/A2: J2.4, U1.11 (A2), U2.11 (A2), U3.11 (A2), U4.11 (A2), U5.11 (A2), U6.11 (A2), U7.3 (A2), U8.3 (A2), U9.3 (A2)
/A3: J2.5, U1.12 (A3), U2.12 (A3), U3.12 (A3), U4.12 (A3), U5.12 (A3), U6.12 (A3), U7.4 (A3), U8.4 (A3), U9.4 (A3)
/A4: J2.6, U1.13 (A4), U2.13 (A4), U3.13 (A4), U4.13 (A4), U5.13 (A4), U6.13 (A4), U7.5 (A4), U8.5 (A4), U9.5 (A4)
/A5: J2.7, U1.14 (A5), U2.14 (A5), U3.14 (A5), U4.14 (A5), U5.14 (A5), U6.14 (A5), U7.6 (A5), U8.6 (A5), U9.6 (A5)
/A6: J2.8, U1.15 (A6), U2.15 (A6), U3.15 (A6), U4.15 (A6), U5.15 (A6), U6.15 (A6), U7.7 (A6), U8.7 (A6), U9.7 (A6)
/A7: J2.9, U1.16 (A7), U2.16 (A7), U3.16 (A7), U4.16 (A7), U5.16 (A7), U6.16 (A7), U7.8 (A7), U8.8 (A7), U9.8 (A7)
/B0: U1.1 (B0), U2.1 (B0), U3.1 (B0), U4.1 (B0), U5.1 (B0), U6.1 (B0), U10.19 (Q0)
/B0': J1.2, U10.2 (D0)
/B1: U1.2 (B1), U2.2 (B1), U3.2 (B1), U4.2 (B1), U5.2 (B1), U6.2 (B1), U10.18 (Q1)
/B1': J1.3, U10.3 (D1)
/B2: U1.3 (B2), U2.3 (B2), U3.3 (B2), U4.3 (B2), U5.3 (B2), U6.3 (B2), U10.17 (Q2)
/B2': J1.4, U10.4 (D2)
/B3: U1.4 (B3), U2.4 (B3), U3.4 (B3), U4.4 (B3), U5.4 (B3), U6.4 (B3), U10.16 (Q3)
/B3': J1.5, U10.5 (D3)
/B4: U1.5 (B4), U2.5 (B4), U3.5 (B4), U4.5 (B4), U5.5 (B4), U6.5 (B4), U10.15 (Q4)
/B4': J1.6, U10.6 (D4)
/B5: U1.6 (B5), U2.6 (B5), U3.6 (B5), U4.6 (B5), U5.6 (B5), U6.6 (B5), U10.14 (Q5)
/B5': J1.7, U10.7 (D5)
/B6: U1.7 (B6), U2.7 (B6), U3.7 (B6), U4.7 (B6), U5.7 (B6), U6.7 (B6), U10.13 (Q6)
/B6': J1.8, U10.8 (D6)
/B7: U1.8 (B7), U2.8 (B7), U3.8 (B7), U4.8 (B7), U5.8 (B7), U6.8 (B7), U10.12 (Q7)
/B7': J1.9, U10.9 (D7)
/CMP.Expand: J41.1, U5.28 (~OE)
/INVH: J14.1, R1.1, U10.11 (INVH)
/INVL: J13.1, R2.1, U10.1 (INVL)
/Latch: J4.1, R3.2, U1.25 (Latch), U2.25 (Latch), U3.25 (Latch), U4.25 (Latch), U5.25 (Latch), U6.25 (Latch), U7.17 (Latch), U8.17 (Latch), U9.17 (Latch)
/O0: J3.2, U1.17 (O0), U2.17 (O0), U3.17 (O0), U4.17 (O0), U5.17 (O0), U6.17 (O0), U7.9 (O0), U8.9 (O0), U9.9 (O0)
/O1: J3.3, U1.18 (O1), U2.18 (O1), U3.18 (O1), U4.18 (O1), U5.18 (O1), U6.18 (O1), U7.10 (O1), U8.10 (O1), U9.10 (O1)
/O2: J3.4, U1.19 (O2), U2.19 (O2), U3.19 (O2), U4.19 (O2), U5.19 (O2), U6.19 (O2), U7.11 (O2), U8.11 (O2), U9.11 (O2)
/O3: J3.5, U1.20 (O3), U2.20 (O3), U3.20 (O3), U4.20 (O3), U5.20 (O3), U6.20 (O3), U7.12 (O3), U8.12 (O3), U9.12 (O3)
/O4: J3.6, U1.21 (O4), U2.21 (O4), U3.21 (O4), U4.21 (O4), U5.21 (O4), U6.21 (O4), U7.13 (O4), U8.13 (O4), U9.13 (O4)
/O5: J3.7, U1.22 (O5), U2.22 (O5), U3.22 (O5), U4.22 (O5), U5.22 (O5), U6.22 (O5), U7.14 (O5), U8.14 (O5), U9.14 (O5)
/O6: J3.8, U1.23 (O6), U2.23 (O6), U3.23 (O6), U4.23 (O6), U5.23 (O6), U6.23 (O6), U7.15 (O6), U8.15 (O6), U9.15 (O6)
/O7: J3.9, U1.24 (O7), U2.24 (O7), U3.24 (O7), U4.24 (O7), U5.24 (O7), U6.24 (O7), U7.16 (O7), U8.16 (O7), U9.16 (O7)
/UseCF: J31.1, U1.28 (~OE)
/UseCF2: J6.1, U7.20 (~Expand)
/~ADDx: J30.1, U1.29 (~OE(C))
/~AND: J28.1, U2.28 (~OE)
/~LSRx: J5.1, U7.21 (~OE)
/~MOV: J25.1, U6.28 (~OE)
/~OR: J27.1, U3.28 (~OE)
/~RSRV: J12.1, U9.20 (~Expand)
/~SWAP: J11.1, U8.20 (~Expand)
/~XOR: J26.1, U4.28 (~OE)
GND: C1.2, J1.1, J2.1, J3.1, J7.1, Q1.1 (G), R1.2, R2.2, U1.27 (Gnd), U2.27 (Gnd), U3.27 (Gnd), U4.27 (Gnd), U5.27 (Gnd), U6.27 (Gnd), U7.19 (Gnd), U8.19 (Gnd), U9.19 (Gnd), U10.10 (Gnd)
unnamed: J7.2, Q1.3 (D)
VCC: C1.1, Q1.2 (S), R3.1, U1.26 (Vcc), U2.26 (Vcc), U3.26 (Vcc), U4.26 (Vcc), U5.26 (Vcc), U6.26 (Vcc), U7.18 (Vcc), U8.18 (Vcc), U9.18 (Vcc), U10.20 (Vcc)

Notes on the sheet:
ADD[C]
AND
XOR
CMP[C]
LSR[C]
MOV
NOT USED!
SWAP
Power In
Reverse polarity protection
RSRV
