TheJustMoose/74HC-CPU/hard/!ALU/ALU_PCB/ALU.kicad_pcb

## KiCad design hard/!ALU/ALU_PCB/ALU.kicad_pcb (continued)

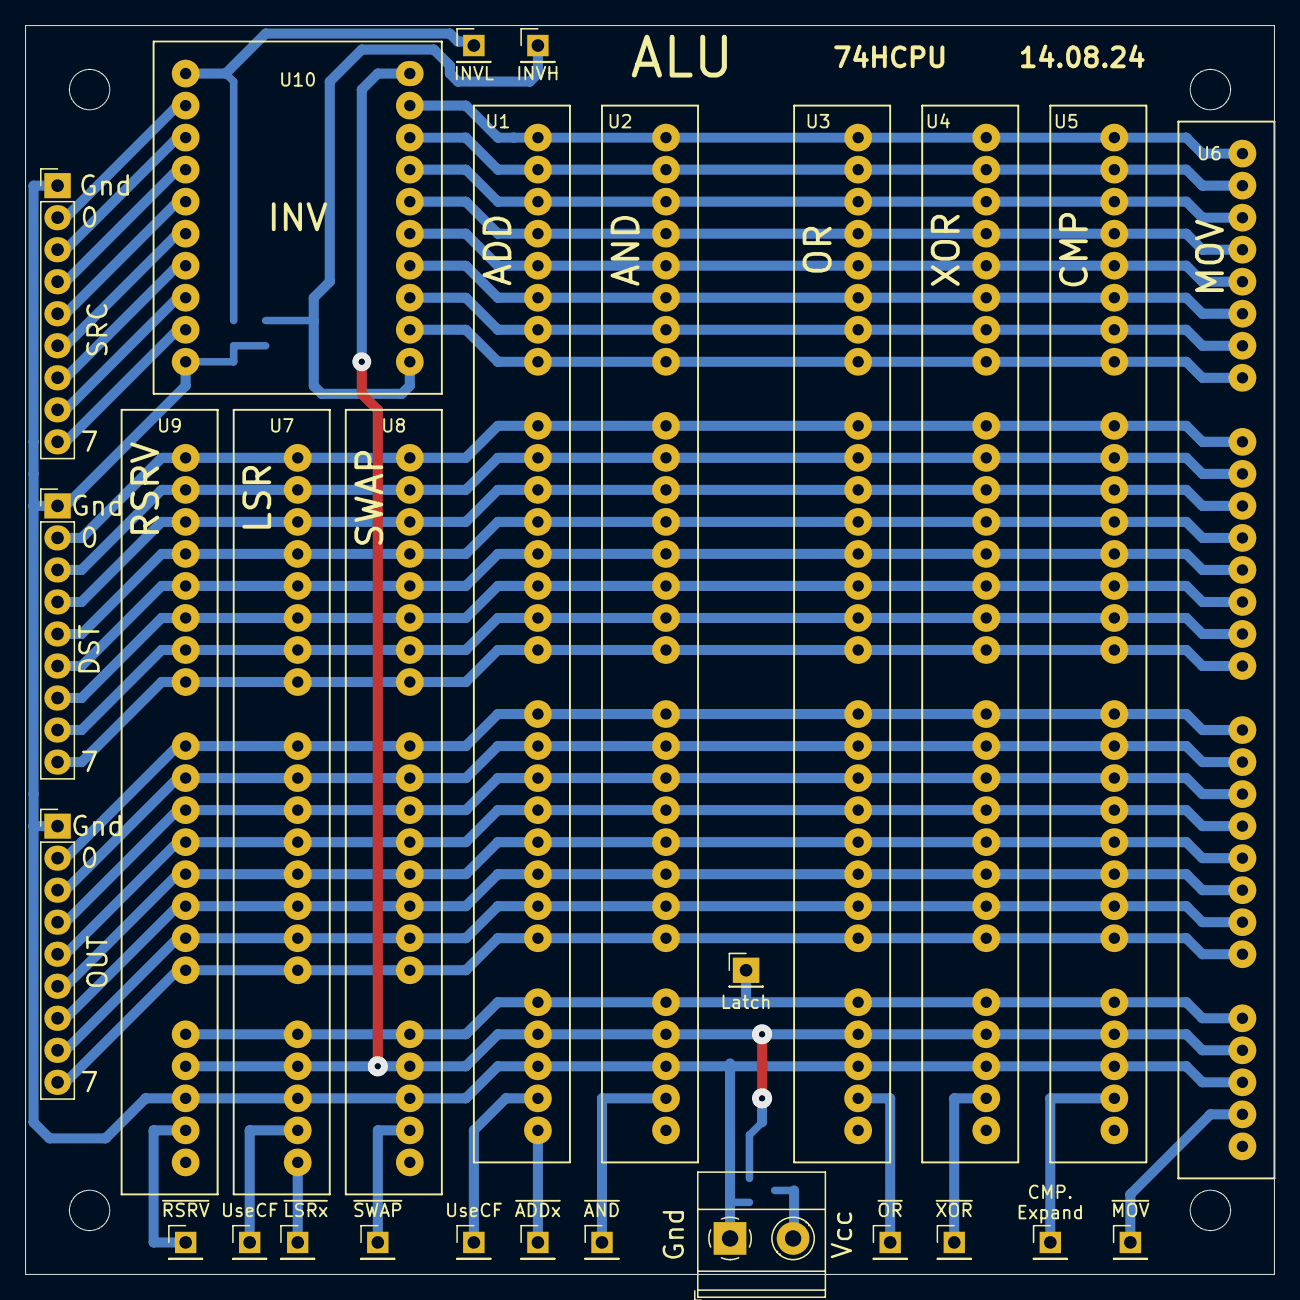
[picture p103: board ALU.kicad_pcb from above]

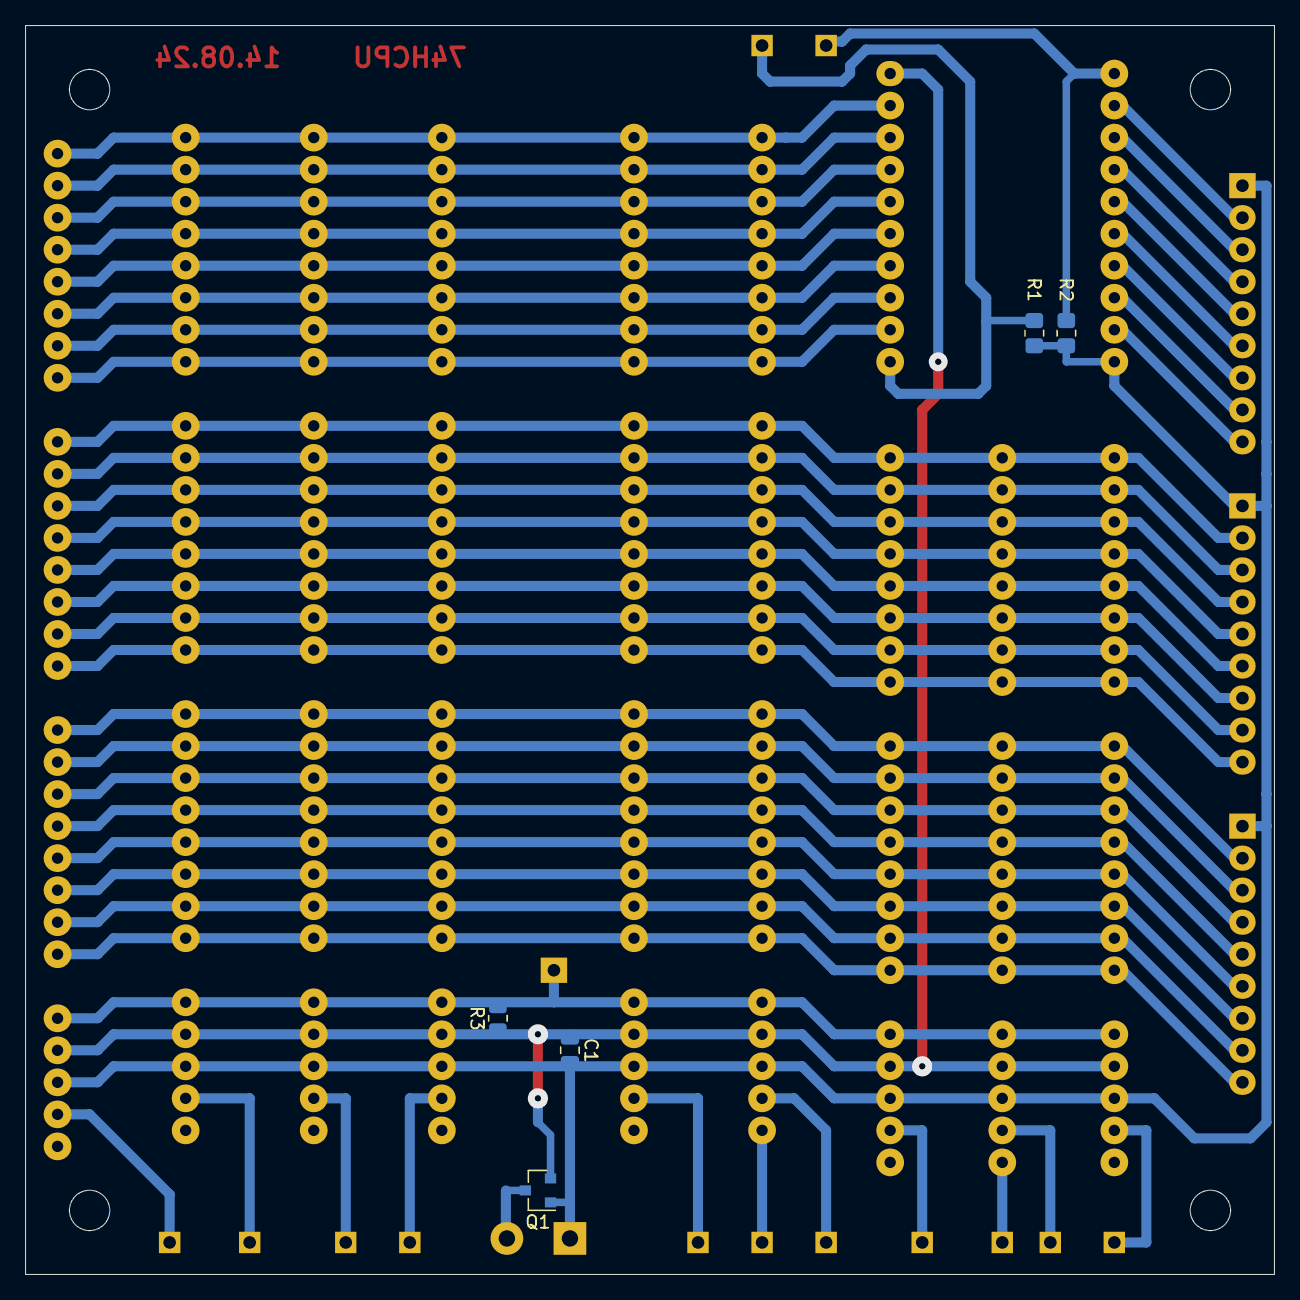
[picture p104: board ALU.kicad_pcb from below]

Board: 2 copper layers, 99.1 x 99.1 mm, 37 parts (5 on the bottom side), 49 nets.
