TheJustMoose/74HC-CPU/hard/!Ports/Ports/Ports.kicad_pcb

## KiCad design hard/!Ports/Ports/Ports.kicad_pcb (2024-08-16)

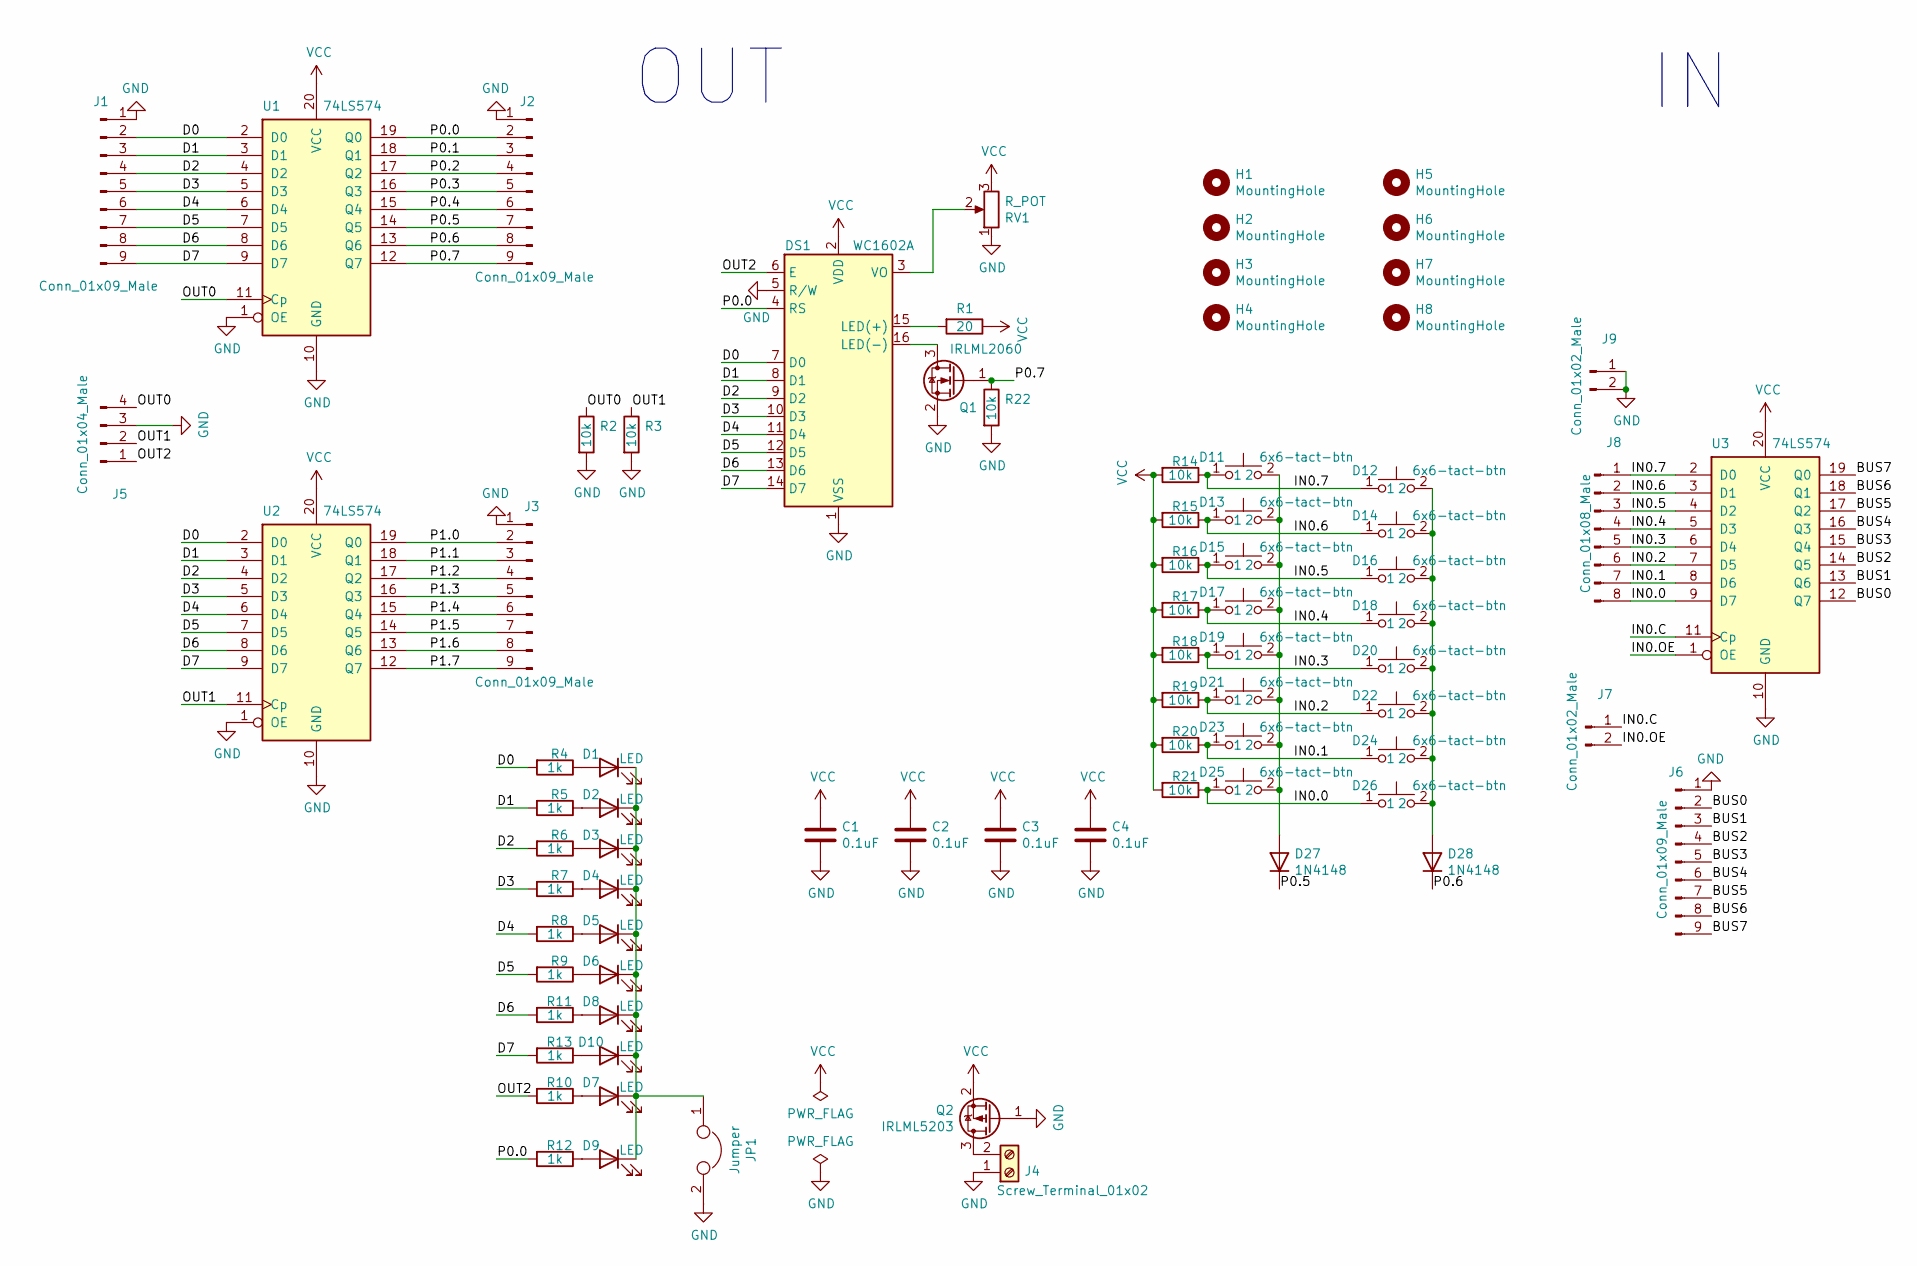
[picture p105: schematic Ports.sch]

Parts:
C1, C2, C3: 0.1uF; C_Axial_L3.8mm_D2.6mm_P22.86mm_Horizontal
C4: 0.1uF; C_Disc_D7.0mm_W2.5mm_P5.00mm
D1, D2, D3, D4, D5, D6, D7, D8, D9, D10: LED; LED_Rectangular_W5.0mm_H2.0mm
D11, D12, D13, D14, D15, D16, D17, D18, D19, D20, D21, D22, D23, D24, D25, D26: 6x6-tact-btn; SW_PUSH_6mm_H4.3mm
D27, D28: 1N4148; D_DO-35_SOD27_P10.16mm_Horizontal
DS1: WC1602A; WH1602-2-holes
H1, H2, H3, H4, H5, H6, H7, H8: MountingHole; MountingHole_3.2mm_M3
J1, J2, J3, J6: Conn_01x09_Male; PinHeader_1x09_P2.54mm_Vertical
J4: Screw_Terminal_01x02; TerminalBlock_Phoenix_PT-1,5-2-5.0-H_1x02_P5.00mm_Horizontal
J5: Conn_01x04_Male; PinHeader_1x04_P2.54mm_Vertical
J7, J9: Conn_01x02_Male; PinHeader_1x02_P2.54mm_Vertical
J8: Conn_01x08_Male; PinHeader_1x08_P2.54mm_Vertical
JP1: Jumper; SolderJumper-2_P1.3mm_Open_RoundedPad1.0x1.5mm
Q1: IRLML2060; SOT-23
Q2: IRLML5203; SOT-23
R1: 20; R_Axial_DIN0207_L6.3mm_D2.5mm_P15.24mm_Horizontal
R2, R3, R14, R15, R16, R17, R18, R19, R20, R21, R22: 10k; R_0805_2012Metric_Pad1.20x1.40mm_HandSolder
R4, R5, R6, R7, R8, R9, R10, R11, R12, R13: 1k; R_0805_2012Metric_Pad1.20x1.40mm_HandSolder
RV1: R_POT; pot-5x5
U1, U2, U3: 74LS574; DIP-20_W7.62mm

Connections:
/BUS0: J6.2, U3.12 (Q7)
/BUS1: J6.3, U3.13 (Q6)
/BUS2: J6.4, U3.14 (Q5)
/BUS3: J6.5, U3.15 (Q4)
/BUS4: J6.6, U3.16 (Q3)
/BUS5: J6.7, U3.17 (Q2)
/BUS6: J6.8, U3.18 (Q1)
/BUS7: J6.9, U3.19 (Q0)
/D0: DS1.7 (D0), J1.2, R4.2, U1.2 (D0), U2.2 (D0)
/D1: DS1.8 (D1), J1.3, R5.2, U1.3 (D1), U2.3 (D1)
/D2: DS1.9 (D2), J1.4, R6.2, U1.4 (D2), U2.4 (D2)
/D3: DS1.10 (D3), J1.5, R7.2, U1.5 (D3), U2.5 (D3)
/D4: DS1.11 (D4), J1.6, R8.2, U1.6 (D4), U2.6 (D4)
/D5: DS1.12 (D5), J1.7, R9.2, U1.7 (D5), U2.7 (D5)
/D6: DS1.13 (D6), J1.8, R11.2, U1.8 (D6), U2.8 (D6)
/D7: DS1.14 (D7), J1.9, R13.2, U1.9 (D7), U2.9 (D7)
/IN0.0: D25.1, D26.1, J8.8, R21.1, U3.9 (D7)
/IN0.1: D23.1, D24.1, J8.7, R20.1, U3.8 (D6)
/IN0.2: D21.1, D22.1, J8.6, R19.1, U3.7 (D5)
/IN0.3: D19.1, D20.1, J8.5, R18.1, U3.6 (D4)
/IN0.4: D17.1, D18.1, J8.4, R17.1, U3.5 (D3)
/IN0.5: D15.1, D16.1, J8.3, R16.1, U3.4 (D2)
/IN0.6: D13.1, D14.1, J8.2, R15.1, U3.3 (D1)
/IN0.7: D11.1, D12.1, J8.1, R14.1, U3.2 (D0)
/IN0.C: J7.1, U3.11 (Cp)
/IN0.OE: J7.2, U3.1 (OE)
/OUT0: J5.4, R2.1, U1.11 (Cp)
/OUT1: J5.2, R3.1, U2.11 (Cp)
/OUT2: DS1.6 (E), J5.1, R10.2
/P0.0: DS1.4 (RS), J2.2, R12.2, U1.19 (Q0)
/P0.1: J2.3, U1.18 (Q1)
/P0.2: J2.4, U1.17 (Q2)
/P0.3: J2.5, U1.16 (Q3)
/P0.4: J2.6, U1.15 (Q4)
/P0.5: D27.1 (K), J2.7, U1.14 (Q5)
/P0.6: D28.1 (K), J2.8, U1.13 (Q6)
/P0.7: J2.9, Q1.1 (G), R22.1, U1.12 (Q7)
/P1.0: J3.2, U2.19 (Q0)
/P1.1: J3.3, U2.18 (Q1)
/P1.2: J3.4, U2.17 (Q2)
/P1.3: J3.5, U2.16 (Q3)
/P1.4: J3.6, U2.15 (Q4)
/P1.5: J3.7, U2.14 (Q5)
/P1.6: J3.8, U2.13 (Q6)
/P1.7: J3.9, U2.12 (Q7)
GND: C1.2, C2.2, C3.2, C4.2, DS1.1 (VSS), DS1.5 (R/W), J1.1, J2.1, J3.1, J4.1, J5.3, J6.1, J9.1, J9.2, JP1.2, Q1.2 (S), Q2.1 (G), R2.2, R3.2, R22.2, RV1.1, U1.1 (OE), U1.10 (GND), U2.1 (OE), U2.10 (GND), U3.10 (GND)
unnamed: D1.1 (K), D2.1 (K), D3.1 (K), D4.1 (K), D5.1 (K), D6.1 (K), D7.1 (K), D8.1 (K), D9.1 (K), D10.1 (K), JP1.1
unnamed: D1.2 (A), R4.1
unnamed: D2.2 (A), R5.1
unnamed: D3.2 (A), R6.1
unnamed: D4.2 (A), R7.1
unnamed: D5.2 (A), R8.1
unnamed: D6.2 (A), R9.1
unnamed: D7.2 (A), R10.1
unnamed: D8.2 (A), R11.1
unnamed: D9.2 (A), R12.1
unnamed: D10.2 (A), R13.1
unnamed: D11.2, D13.2, D15.2, D17.2, D19.2, D21.2, D23.2, D25.2, D27.2 (A)
unnamed: D12.2, D14.2, D16.2, D18.2, D20.2, D22.2, D24.2, D26.2, D28.2 (A)
unnamed: DS1.3 (VO), RV1.2
unnamed: DS1.15 (LED(+)), R1.2
unnamed: DS1.16 (LED(-)), Q1.3 (D)
unnamed: J4.2, Q2.3 (D)
VCC: C1.1, C2.1, C3.1, C4.1, DS1.2 (VDD), Q2.2 (S), R1.1, R14.2, R15.2, R16.2, R17.2, R18.2, R19.2, R20.2, R21.2, RV1.3, U1.20 (VCC), U2.20 (VCC), U3.20 (VCC)

Notes on the sheet:
OUT

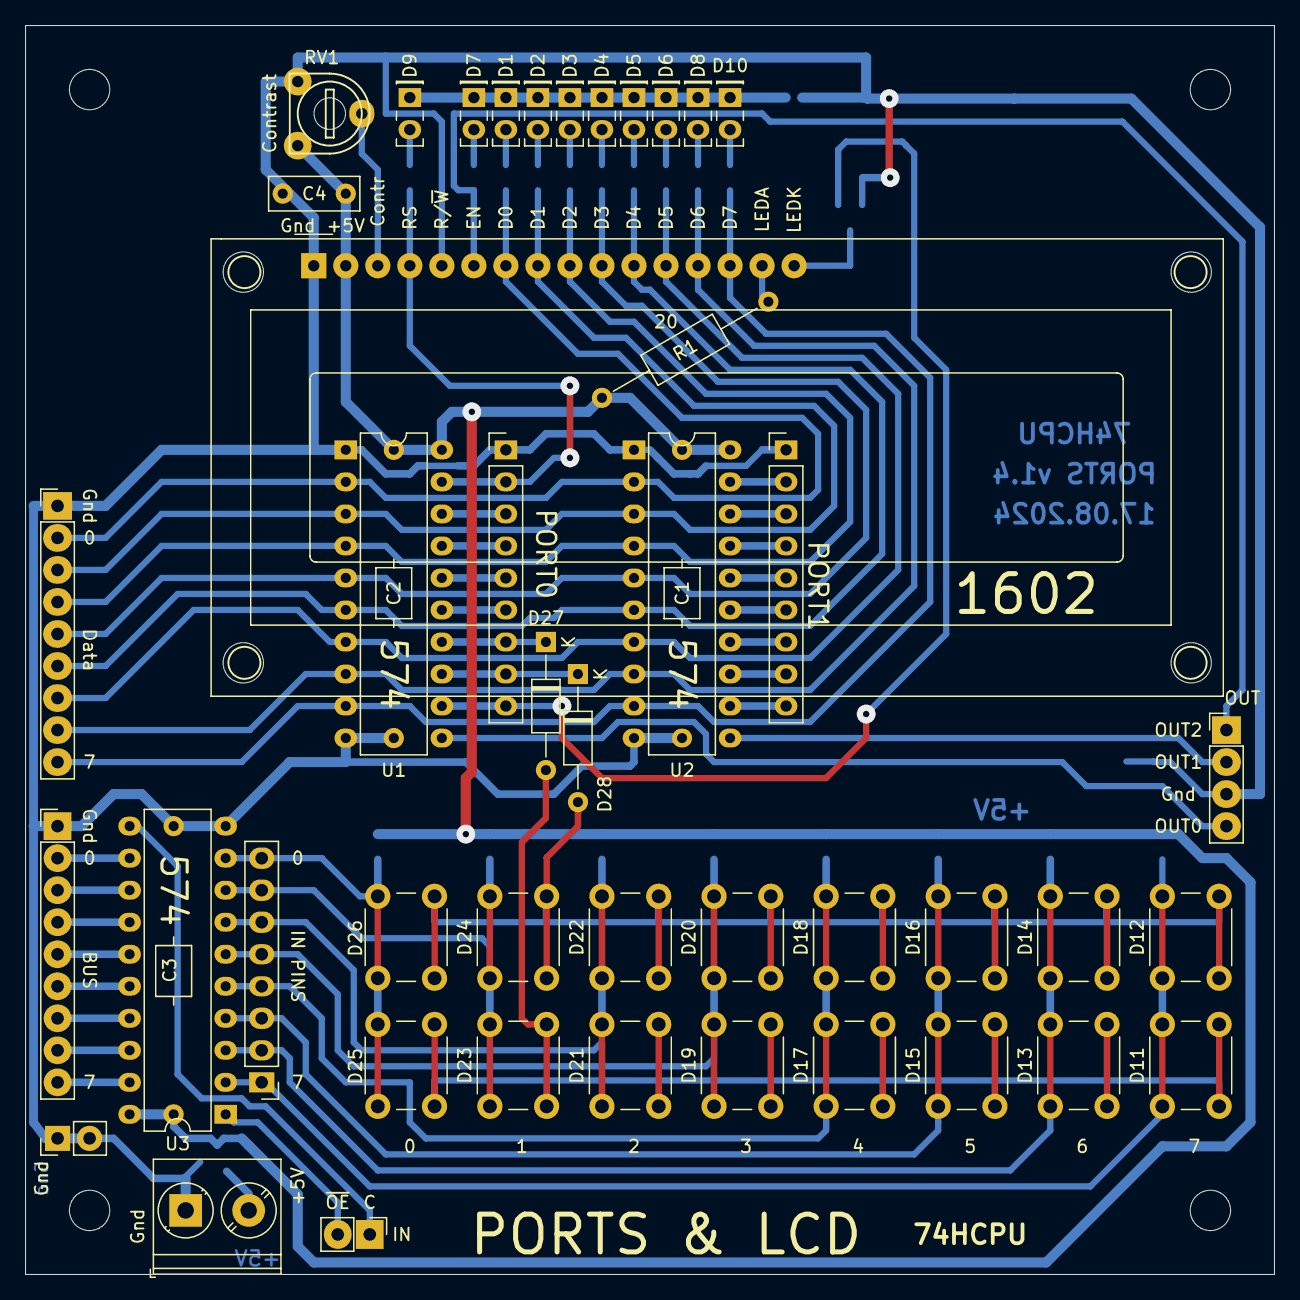
[picture p106: board Ports.kicad_pcb from above]

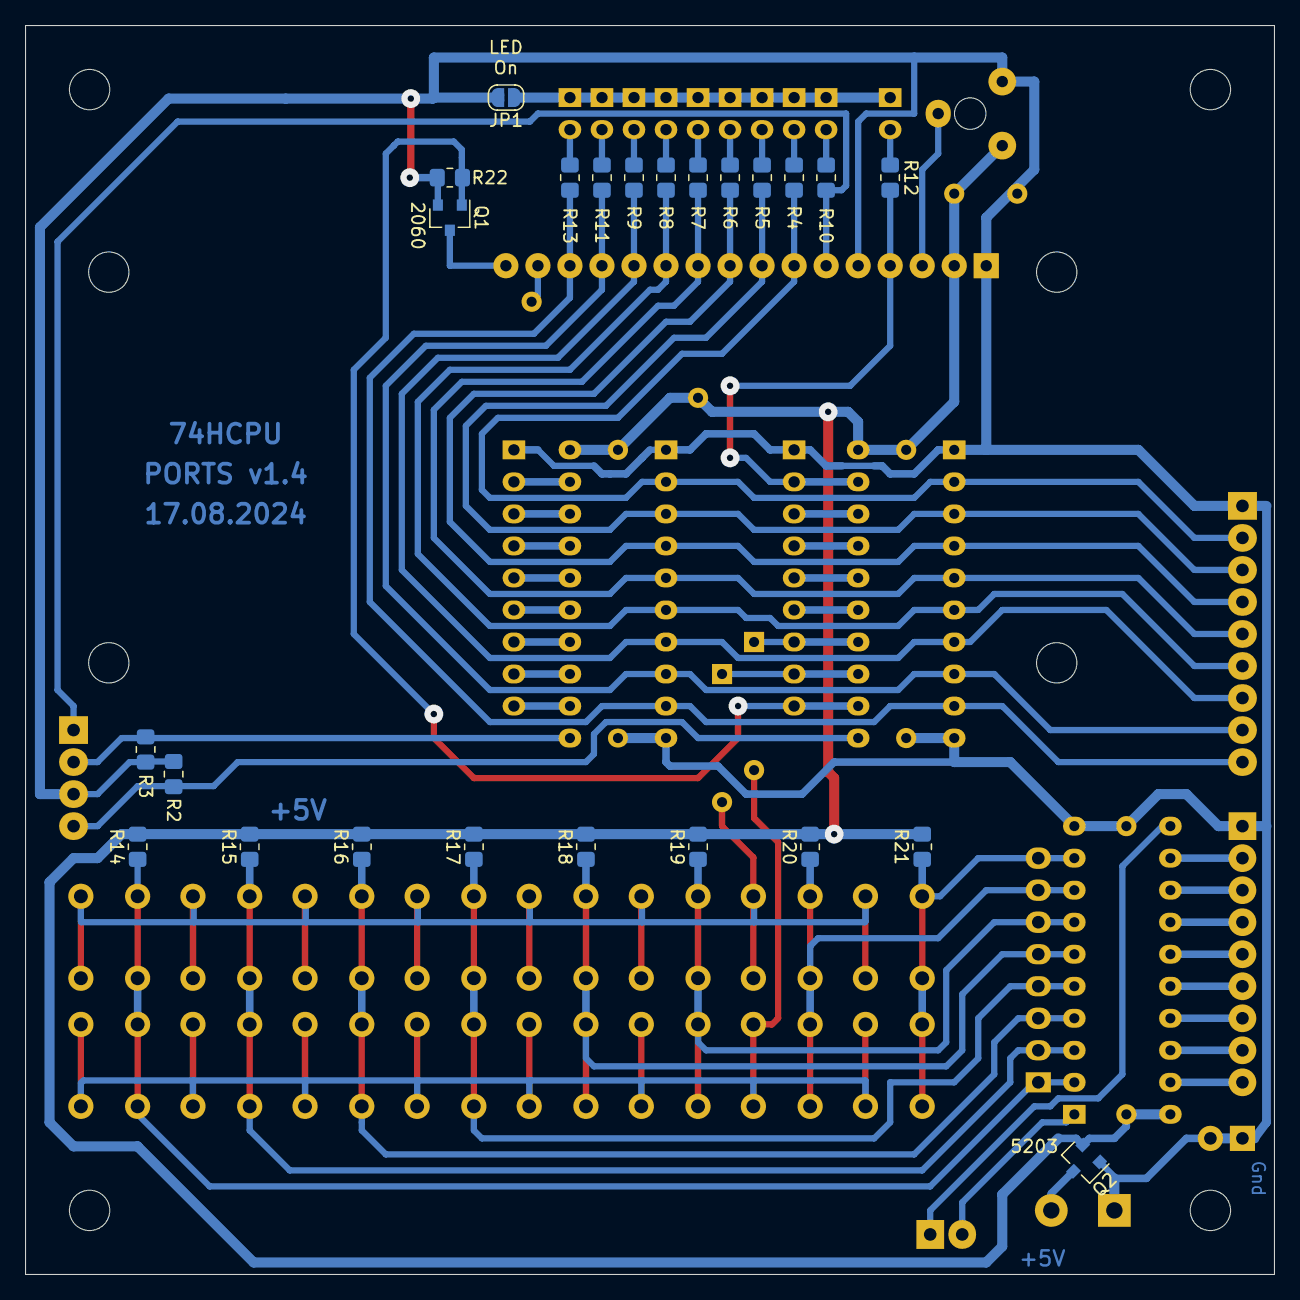
[picture p107: board Ports.kicad_pcb from below]

Board: 2 copper layers, 99.1 x 99.1 mm, 79 parts (24 on the bottom side), 64 nets.
