TheJustMoose/74HC-CPU/hard/!ADDR_CNT/MUX16bitAndAddrCnt/MUX16bit.kicad_pcb

## KiCad design hard/!ADDR_CNT/MUX16bitAndAddrCnt/MUX16bit.kicad_pcb (2024-06-20)

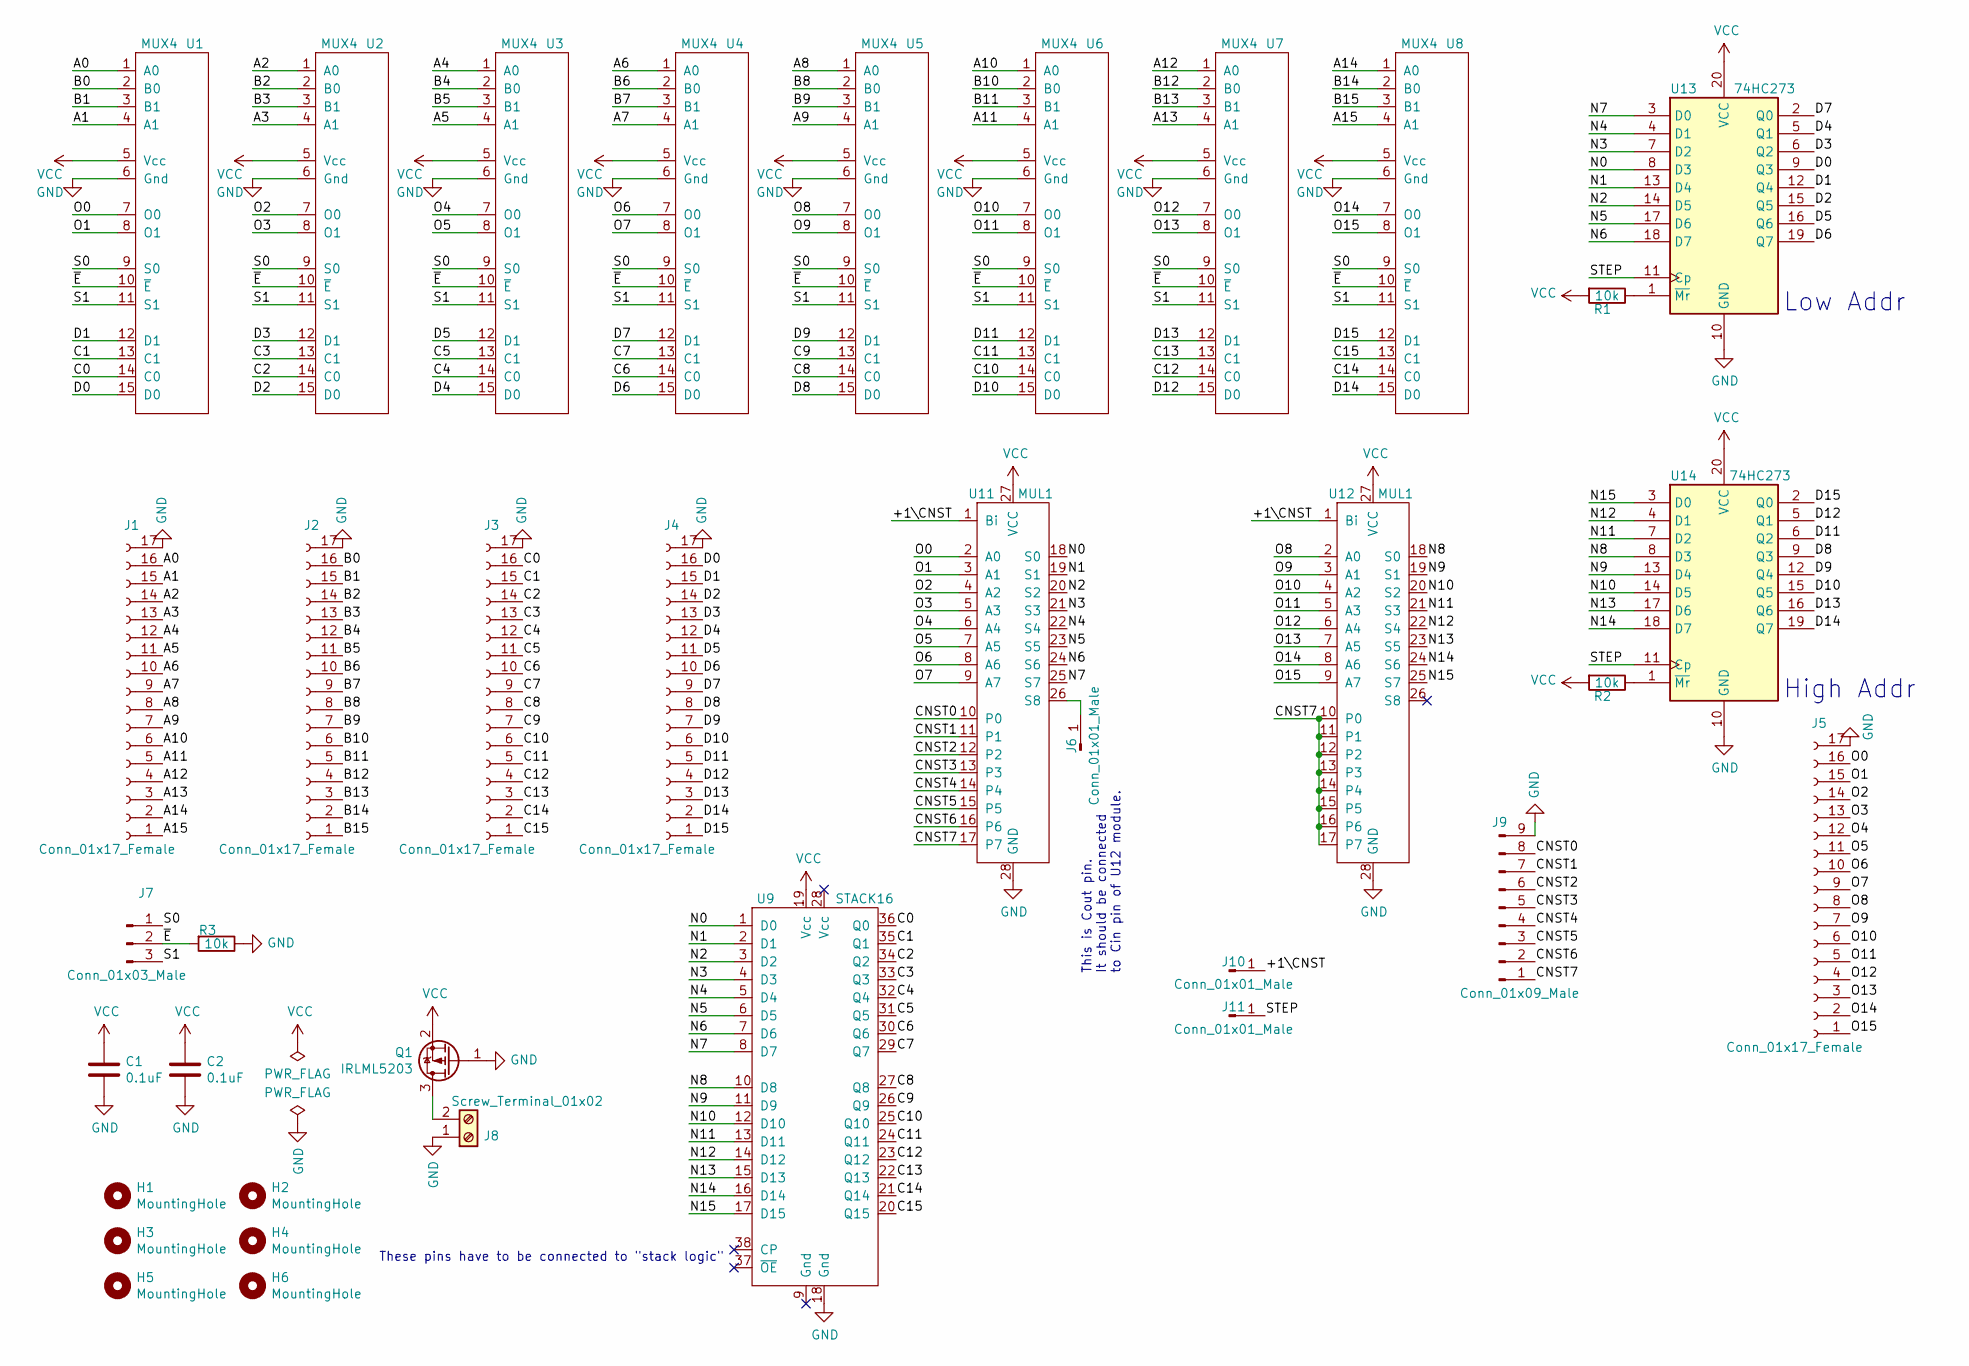
[picture p108: schematic MUX16bit.sch]

Parts:
C1, C2: 0.1uF; C_0805_2012Metric_Pad1.18x1.45mm_HandSolder
H1, H2, H3, H4, H5, H6: MountingHole; MountingHole_3.2mm_M3
J1, J2, J3, J4, J5: Conn_01x17_Female; PinSocket_1x17_P2.54mm_Vertical
J6, J10, J11: Conn_01x01_Male; PinHeader_1x01_P2.54mm_Vertical
J7: Conn_01x03_Male; PinHeader_1x03_P2.54mm_Vertical
J8: Screw_Terminal_01x02; TerminalBlock_Phoenix_PT-1,5-2-5.0-H_1x02_P5.00mm_Horizontal
J9: Conn_01x09_Male; PinHeader_1x09_P2.54mm_Vertical
Q1: IRLML5203; SOT-23
R1, R2, R3: 10k; R_0805_2012Metric_Pad1.20x1.40mm_HandSolder
U1, U2, U3, U4, U5, U6, U7, U8: MUX4; MUX1
U9: STACK16
U11, U12: MUL1
U13, U14: 74HC273; DIP-20_W7.62mm

Connections:
/+1\CNST: J10.1, U11.1 (Bi), U12.1 (Bi)
/A0: J1.16, U1.1 (A0)
/A1: J1.15, U1.4 (A1)
/A2: J1.14, U2.1 (A0)
/A3: J1.13, U2.4 (A1)
/A4: J1.12, U3.1 (A0)
/A5: J1.11, U3.4 (A1)
/A6: J1.10, U4.1 (A0)
/A7: J1.9, U4.4 (A1)
/A8: J1.8, U5.1 (A0)
/A9: J1.7, U5.4 (A1)
/A10: J1.6, U6.1 (A0)
/A11: J1.5, U6.4 (A1)
/A12: J1.4, U7.1 (A0)
/A13: J1.3, U7.4 (A1)
/A14: J1.2, U8.1 (A0)
/A15: J1.1, U8.4 (A1)
/B0: J2.16, U1.2 (B0)
/B1: J2.15, U1.3 (B1)
/B2: J2.14, U2.2 (B0)
/B3: J2.13, U2.3 (B1)
/B4: J2.12, U3.2 (B0)
/B5: J2.11, U3.3 (B1)
/B6: J2.10, U4.2 (B0)
/B7: J2.9, U4.3 (B1)
/B8: J2.8, U5.2 (B0)
/B9: J2.7, U5.3 (B1)
/B10: J2.6, U6.2 (B0)
/B11: J2.5, U6.3 (B1)
/B12: J2.4, U7.2 (B0)
/B13: J2.3, U7.3 (B1)
/B14: J2.2, U8.2 (B0)
/B15: J2.1, U8.3 (B1)
/C0: J3.16, U1.14 (C0), U9.36 (Q0)
/C1: J3.15, U1.13 (C1), U9.35 (Q1)
/C2: J3.14, U2.14 (C0), U9.34 (Q2)
/C3: J3.13, U2.13 (C1), U9.33 (Q3)
/C4: J3.12, U3.14 (C0), U9.32 (Q4)
/C5: J3.11, U3.13 (C1), U9.31 (Q5)
/C6: J3.10, U4.14 (C0), U9.30 (Q6)
/C7: J3.9, U4.13 (C1), U9.29 (Q7)
/C8: J3.8, U5.14 (C0), U9.27 (Q8)
/C9: J3.7, U5.13 (C1), U9.26 (Q9)
/C10: J3.6, U6.14 (C0), U9.25 (Q10)
/C11: J3.5, U6.13 (C1), U9.24 (Q11)
/C12: J3.4, U7.14 (C0), U9.23 (Q12)
/C13: J3.3, U7.13 (C1), U9.22 (Q13)
/C14: J3.2, U8.14 (C0), U9.21 (Q14)
/C15: J3.1, U8.13 (C1), U9.20 (Q15)
/CNST0: J9.8, U11.10 (P0)
/CNST1: J9.7, U11.11 (P1)
/CNST2: J9.6, U11.12 (P2)
/CNST3: J9.5, U11.13 (P3)
/CNST4: J9.4, U11.14 (P4)
/CNST5: J9.3, U11.15 (P5)
/CNST6: J9.2, U11.16 (P6)
/CNST7: J9.1, U11.17 (P7), U12.10 (P0), U12.11 (P1), U12.12 (P2), U12.13 (P3), U12.14 (P4), U12.15 (P5), U12.16 (P6), U12.17 (P7)
/D0: J4.16, U1.15 (D0), U13.9 (Q3)
/D1: J4.15, U1.12 (D1), U13.12 (Q4)
/D2: J4.14, U2.15 (D0), U13.15 (Q5)
/D3: J4.13, U2.12 (D1), U13.6 (Q2)
/D4: J4.12, U3.15 (D0), U13.5 (Q1)
/D5: J4.11, U3.12 (D1), U13.16 (Q6)
/D6: J4.10, U4.15 (D0), U13.19 (Q7)
/D7: J4.9, U4.12 (D1), U13.2 (Q0)
/D8: J4.8, U5.15 (D0), U14.9 (Q3)
/D9: J4.7, U5.12 (D1), U14.12 (Q4)
/D10: J4.6, U6.15 (D0), U14.15 (Q5)
/D11: J4.5, U6.12 (D1), U14.6 (Q2)
/D12: J4.4, U7.15 (D0), U14.5 (Q1)
/D13: J4.3, U7.12 (D1), U14.16 (Q6)
/D14: J4.2, U8.15 (D0), U14.19 (Q7)
/D15: J4.1, U8.12 (D1), U14.2 (Q0)
/N0: U9.1 (D0), U11.18 (S0), U13.8 (D3)
/N1: U9.2 (D1), U11.19 (S1), U13.13 (D4)
/N2: U9.3 (D2), U11.20 (S2), U13.14 (D5)
/N3: U9.4 (D3), U11.21 (S3), U13.7 (D2)
/N4: U9.5 (D4), U11.22 (S4), U13.4 (D1)
/N5: U9.6 (D5), U11.23 (S5), U13.17 (D6)
/N6: U9.7 (D6), U11.24 (S6), U13.18 (D7)
/N7: U9.8 (D7), U11.25 (S7), U13.3 (D0)
/N8: U9.10 (D8), U12.18 (S0), U14.8 (D3)
/N9: U9.11 (D9), U12.19 (S1), U14.13 (D4)
/N10: U9.12 (D10), U12.20 (S2), U14.14 (D5)
/N11: U9.13 (D11), U12.21 (S3), U14.7 (D2)
/N12: U9.14 (D12), U12.22 (S4), U14.4 (D1)
/N13: U9.15 (D13), U12.23 (S5), U14.17 (D6)
/N14: U9.16 (D14), U12.24 (S6), U14.18 (D7)
/N15: U9.17 (D15), U12.25 (S7), U14.3 (D0)
/O0: J5.16, U1.7 (O0), U11.2 (A0)
/O1: J5.15, U1.8 (O1), U11.3 (A1)
/O2: J5.14, U2.7 (O0), U11.4 (A2)
/O3: J5.13, U2.8 (O1), U11.5 (A3)
/O4: J5.12, U3.7 (O0), U11.6 (A4)
/O5: J5.11, U3.8 (O1), U11.7 (A5)
/O6: J5.10, U4.7 (O0), U11.8 (A6)
/O7: J5.9, U4.8 (O1), U11.9 (A7)
/O8: J5.8, U5.7 (O0), U12.2 (A0)
/O9: J5.7, U5.8 (O1), U12.3 (A1)
/O10: J5.6, U6.7 (O0), U12.4 (A2)
/O11: J5.5, U6.8 (O1), U12.5 (A3)
/O12: J5.4, U7.7 (O0), U12.6 (A4)
/O13: J5.3, U7.8 (O1), U12.7 (A5)
/O14: J5.2, U8.7 (O0), U12.8 (A6)
/O15: J5.1, U8.8 (O1), U12.9 (A7)
/S0: J7.1, U1.9 (S0), U2.9 (S0), U3.9 (S0), U4.9 (S0), U5.9 (S0), U6.9 (S0), U7.9 (S0), U8.9 (S0)
/S1: J7.3, U1.11 (S1), U2.11 (S1), U3.11 (S1), U4.11 (S1), U5.11 (S1), U6.11 (S1), U7.11 (S1), U8.11 (S1)
/STEP: J11.1, U13.11 (Cp), U14.11 (Cp)
/~E: J7.2, R3.2, U1.10 (~E), U2.10 (~E), U3.10 (~E), U4.10 (~E), U5.10 (~E), U6.10 (~E), U7.10 (~E), U8.10 (~E)
GND: C1.2, C2.2, J1.17, J2.17, J3.17, J4.17, J5.17, J8.1, J9.9, Q1.1 (G), R3.1, U1.6 (Gnd), U2.6 (Gnd), U3.6 (Gnd), U4.6 (Gnd), U5.6 (Gnd), U6.6 (Gnd), U7.6 (Gnd), U8.6 (Gnd), U9.18 (Gnd), U11.28 (GND), U12.28 (GND), U13.10 (GND), U14.10 (GND)
unnamed: J6.1, U11.26 (S8)
unnamed: J8.2, Q1.3 (D)
unnamed: R1.1, U13.1 (~Mr)
unnamed: R2.1, U14.1 (~Mr)
VCC: C1.1, C2.1, Q1.2 (S), R1.2, R2.2, U1.5 (Vcc), U2.5 (Vcc), U3.5 (Vcc), U4.5 (Vcc), U5.5 (Vcc), U6.5 (Vcc), U7.5 (Vcc), U8.5 (Vcc), U9.19 (Vcc), U11.27 (VCC), U12.27 (VCC), U13.20 (VCC), U14.20 (VCC)

Notes on the sheet:
Low Addr
High Addr
This is Cout pin. It should be connected to Cin pin of U12 module.
These pins have to be connected to "stack logic"

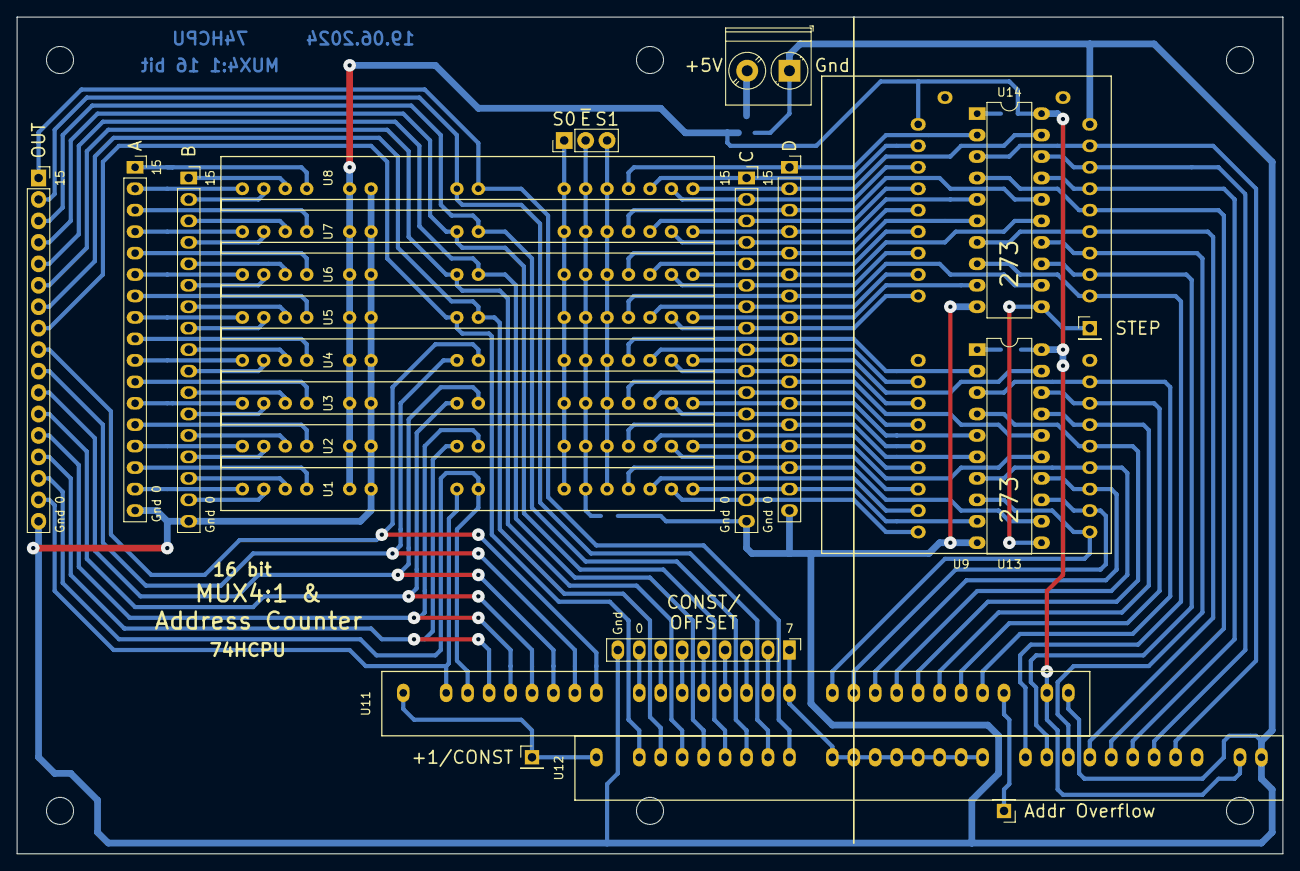
[picture p109: board MUX16bit.kicad_pcb from above]

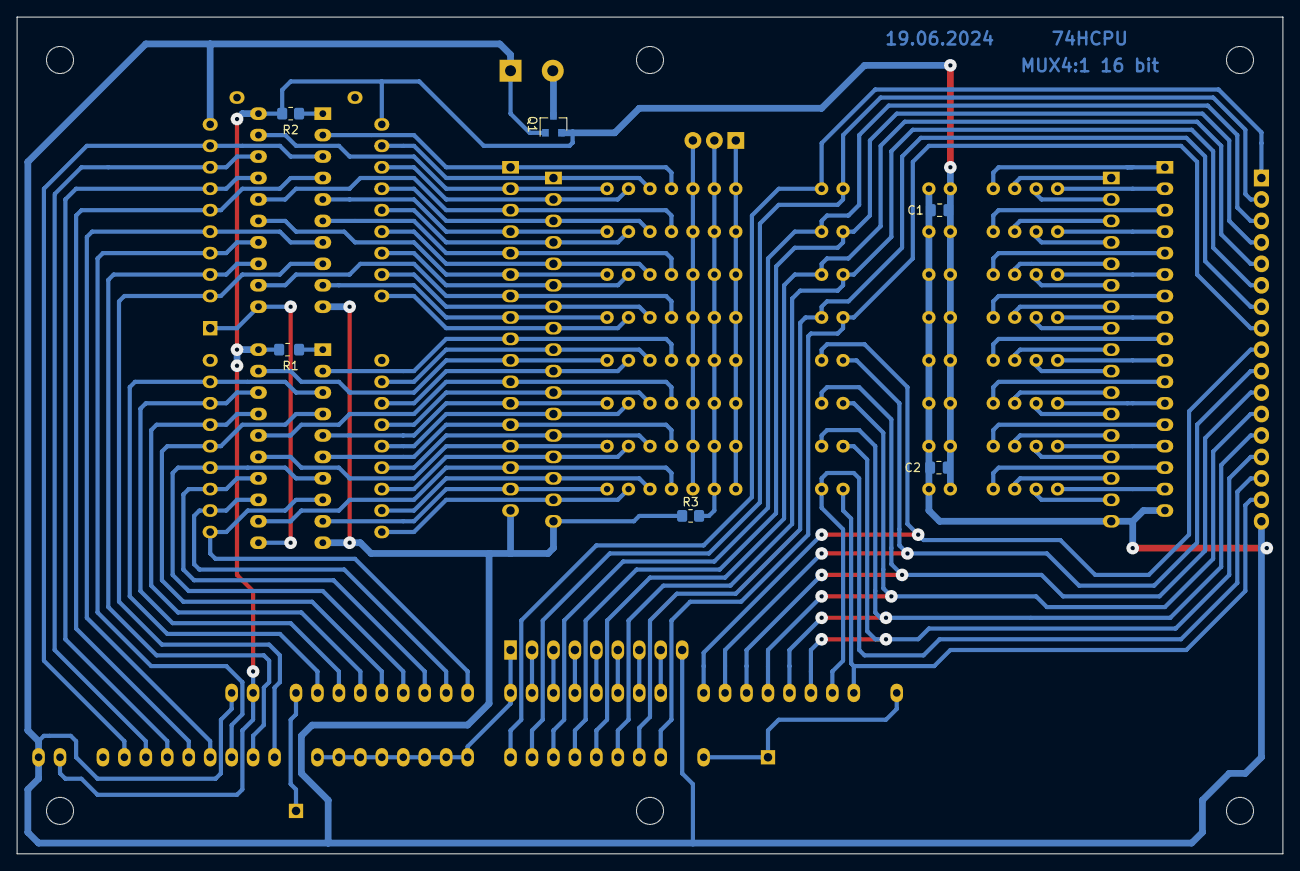
[picture p110: board MUX16bit.kicad_pcb from below]

Board: 2 copper layers, 149.9 x 99.1 mm, 36 parts (6 on the bottom side), 115 nets.
