TheJustMoose/74HC-CPU/hard/Proto/LED8narrow/LED8.kicad_pcb

## KiCad design hard/Proto/LED8narrow/LED8.kicad_pcb (2023-01-11)

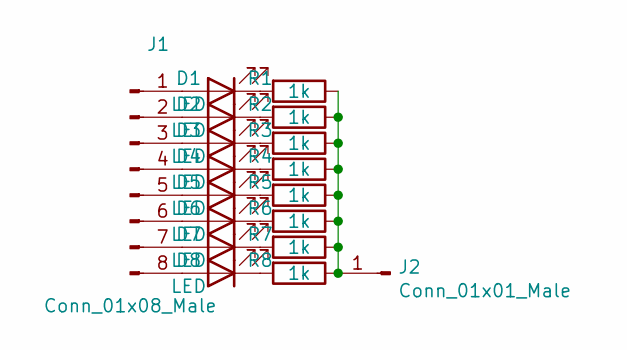
[picture p111: schematic LED8.sch]

Parts:
D1, D2, D3, D4, D5, D6, D7, D8: LED; LED_0805_2012Metric_Pad1.15x1.40mm_HandSolder
J1: Conn_01x08_Male; PinHeader_1x08_P2.54mm_Vertical
J2: Conn_01x01_Male; PinHeader_1x01_P2.54mm_Vertical
R1, R2, R3, R4, R5, R6, R7, R8: 1k; R_0805_2012Metric_Pad1.20x1.40mm_HandSolder

Connections:
unnamed: D1.1 (K), R1.2
unnamed: D1.2 (A), J1.1
unnamed: D2.1 (K), R2.2
unnamed: D2.2 (A), J1.2
unnamed: D3.1 (K), R3.2
unnamed: D3.2 (A), J1.3
unnamed: D4.1 (K), R4.2
unnamed: D4.2 (A), J1.4
unnamed: D5.1 (K), R5.2
unnamed: D5.2 (A), J1.5
unnamed: D6.1 (K), R6.2
unnamed: D6.2 (A), J1.6
unnamed: D7.1 (K), R7.2
unnamed: D7.2 (A), J1.7
unnamed: D8.1 (K), R8.2
unnamed: D8.2 (A), J1.8
unnamed: J2.1, R1.1, R2.1, R3.1, R4.1, R5.1, R6.1, R7.1, R8.1

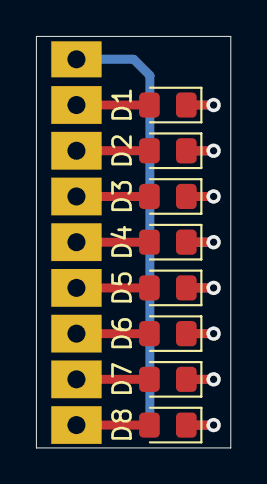
[picture p112: board LED8.kicad_pcb from above]

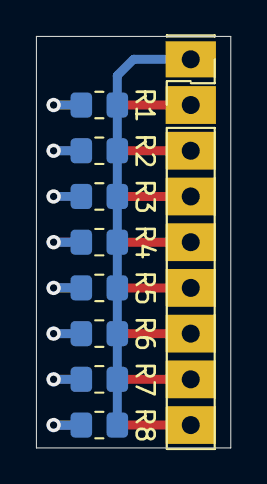
[picture p113: board LED8.kicad_pcb from below]

Board: 2 copper layers, 10.8 x 22.9 mm, 18 parts (10 on the bottom side), 17 nets.
