TheJustMoose/74HC-CPU/hard/!CMD_DEC/JMPS/JMPS.kicad_pcb

## KiCad design hard/!CMD_DEC/JMPS/JMPS.kicad_pcb (2023-02-26)

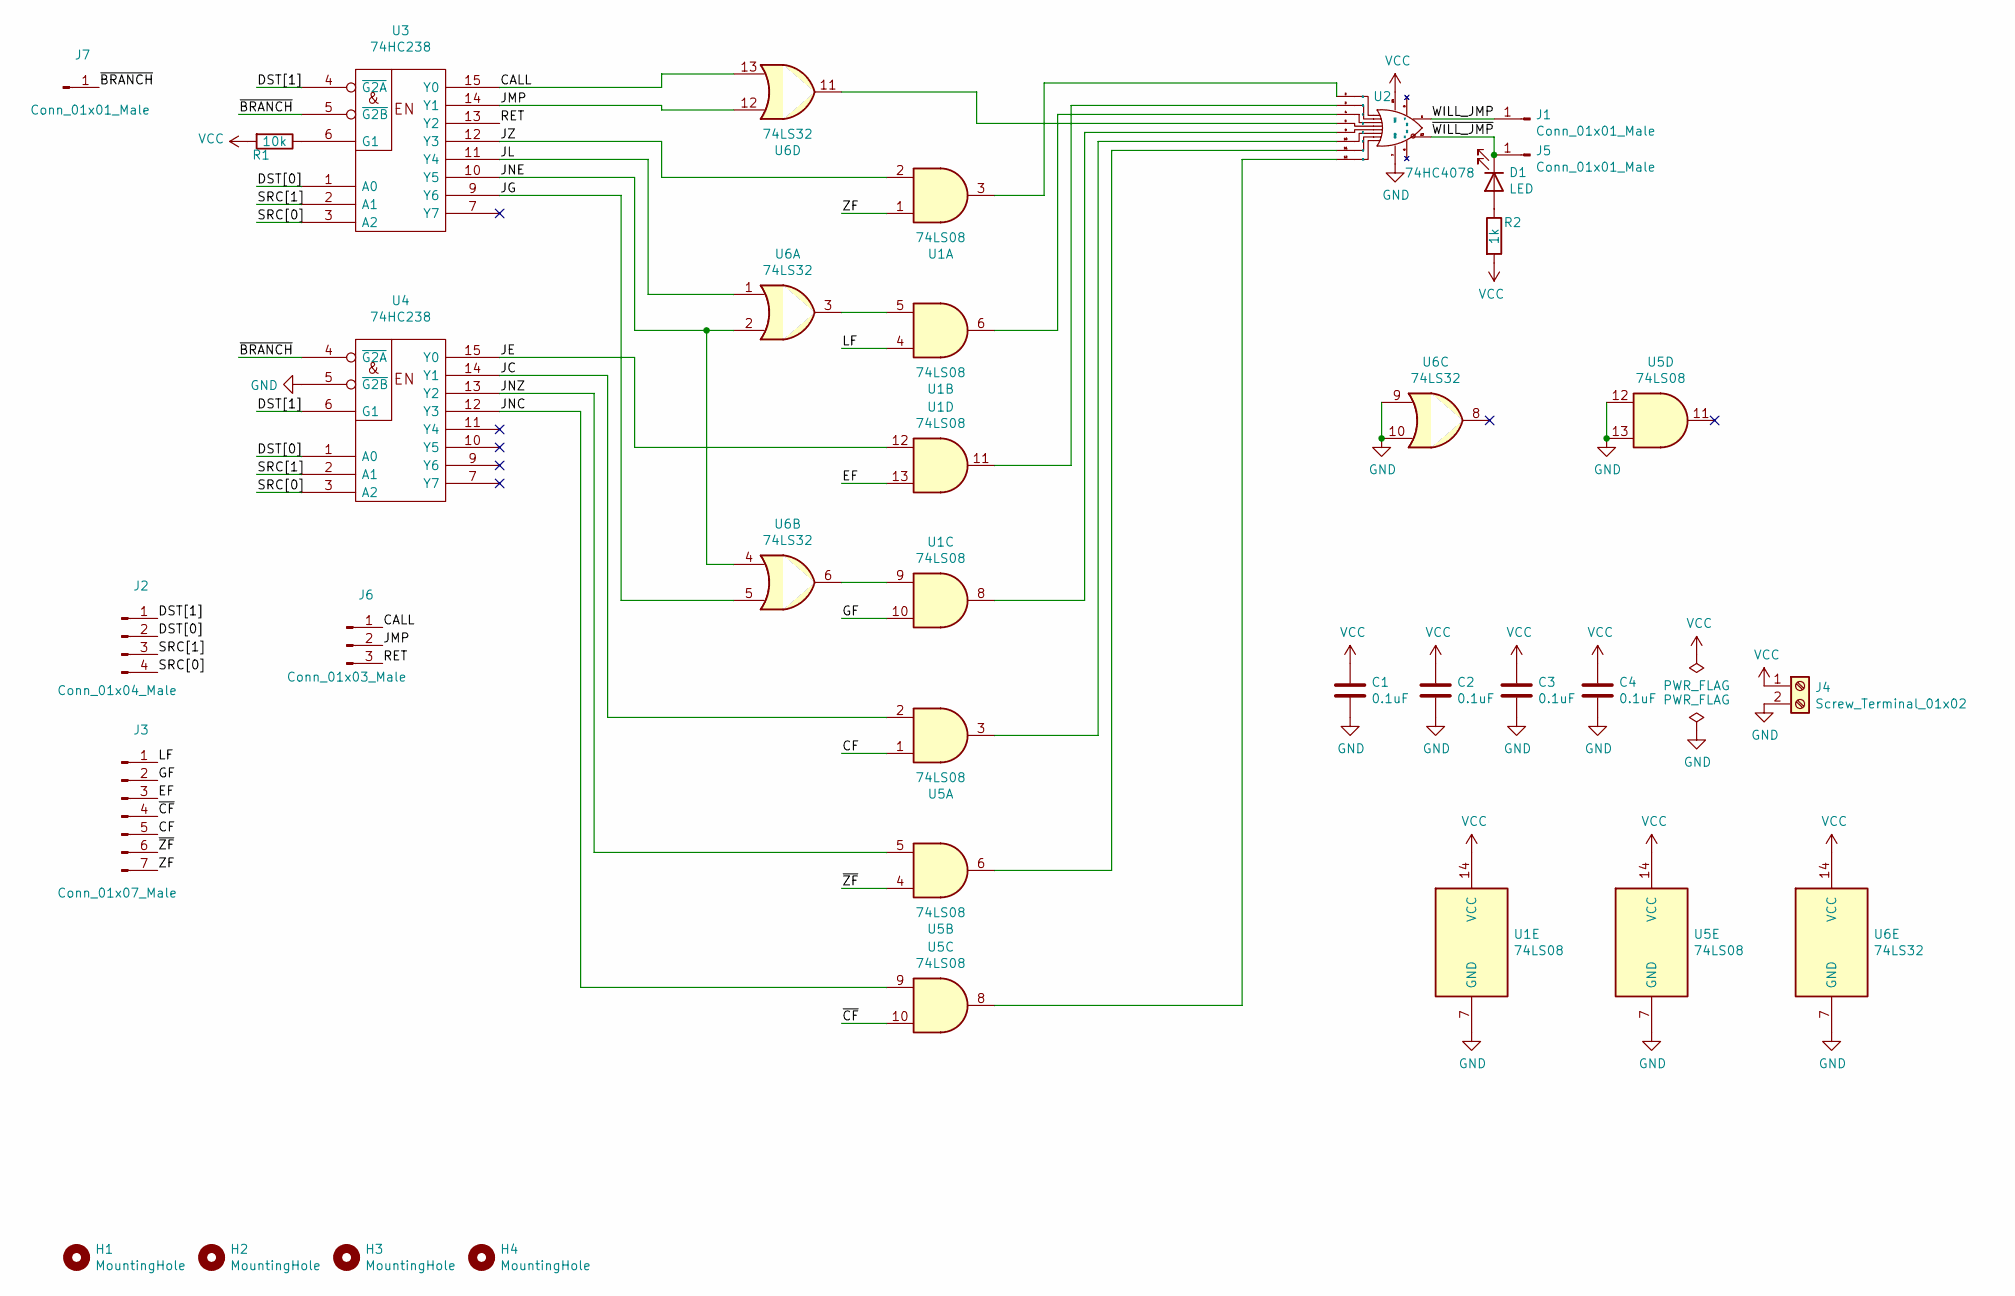
[picture p116: schematic JMPS.sch]

Parts:
C1, C2, C3, C4: 0.1uF; C_0805_2012Metric_Pad1.18x1.45mm_HandSolder
D1: LED; LED_D5.0mm
H1, H2, H3, H4: MountingHole; MountingHole_3.2mm_M3
J1, J5, J7: Conn_01x01_Male; PinHeader_1x01_P2.54mm_Vertical
J2: Conn_01x04_Male; PinHeader_1x04_P2.54mm_Vertical
J3: Conn_01x07_Male; PinHeader_1x07_P2.54mm_Vertical
J4: Screw_Terminal_01x02; TerminalBlock_Phoenix_MKDS-1,5-2_1x02_P5.00mm_Horizontal
J6: Conn_01x03_Male; PinHeader_1x03_P2.54mm_Vertical
R1: 10k; R_0805_2012Metric_Pad1.20x1.40mm_HandSolder
R2: 1k; R_0805_2012Metric_Pad1.20x1.40mm_HandSolder
U1, U5: 74LS08; DIP-14_W7.62mm_Socket
U2: 74HC4078; DIP-14_W7.62mm_Socket
U3, U4: 74HC238; DIP-16_W7.62mm_Socket
U6: 74LS32; DIP-14_W7.62mm_Socket

Connections:
/CALL: J6.1, U3.15 (Y0), U6.13
/CF: J3.5, U5.1
/DST[0]: J2.2, U3.1 (A0), U4.1 (A0)
/DST[1]: J2.1, U3.4 (~G2A), U4.6 (G1)
/EF: J3.3, U1.13
/GF: J3.2, U1.10
/JC: U4.14 (Y1), U5.2
/JE: U1.12, U4.15 (Y0)
/JG: U3.9 (Y6), U6.5
/JL: U3.11 (Y4), U6.1
/JMP: J6.2, U3.14 (Y1), U6.12
/JNC: U4.12 (Y3), U5.9
/JNE: U3.10 (Y5), U6.2, U6.4
/JNZ: U4.13 (Y2), U5.5
/JZ: U1.2, U3.12 (Y3)
/LF: J3.1, U1.4
/RET: J6.3, U3.13 (Y2)
/SRC[0]: J2.4, U3.3 (A2), U4.3 (A2)
/SRC[1]: J2.3, U3.2 (A1), U4.2 (A1)
/WILL_JMP: J1.1, U2.1 (Y)
/ZF: J3.7, U1.1
/~BRANCH: J7.1, U3.5 (~G2B), U4.4 (~G2A)
/~CF: J3.4, U5.10
/~WILL_JMP: D1.1 (K), J5.1, U2.13 (X)
/~ZF: J3.6, U5.4
GND: C1.2, C2.2, C3.2, C4.2, J4.2, U1.7 (GND), U2.7 (GND), U3.8 (GND), U4.5 (~G2B), U4.8 (GND), U5.7 (GND), U5.12, U5.13, U6.7 (GND), U6.9, U6.10
unnamed: D1.2 (A), R2.1
unnamed: R1.1, U3.6 (G1)
unnamed: U1.3, U2.2 (A)
unnamed: U1.5, U6.3
unnamed: U1.6, U2.4 (C)
unnamed: U1.8, U2.9 (E)
unnamed: U1.9, U6.6
unnamed: U1.11, U2.3 (B)
unnamed: U2.5 (D), U6.11
unnamed: U2.10 (F), U5.3
unnamed: U2.11 (G), U5.6
unnamed: U2.12 (H), U5.8
VCC: C1.1, C2.1, C3.1, C4.1, J4.1, R1.2, R2.2, U1.14 (VCC), U2.14 (VCC), U3.16 (VCC), U4.16 (VCC), U5.14 (VCC), U6.14 (VCC)

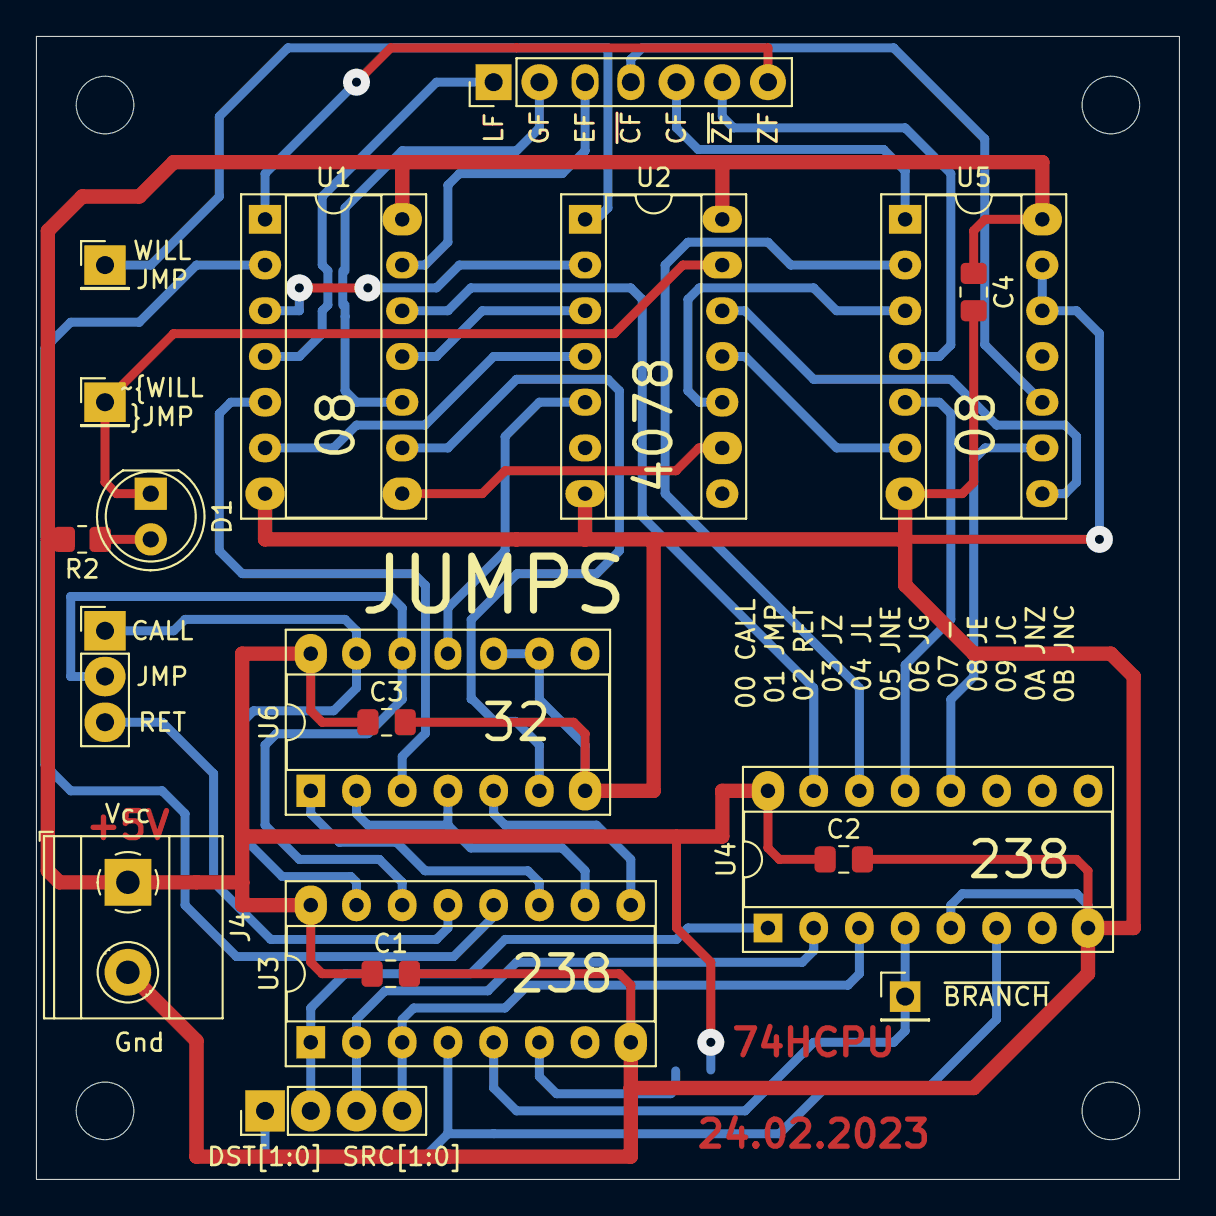
[picture p117: board JMPS.kicad_pcb from above]

Board: 2 copper layers, 63.5 x 63.5 mm, 24 parts (1 on the bottom side), 39 nets.
