TheJustMoose/74HC-CPU/hard/!ALU/LSR/LSR.kicad_pcb

## KiCad design hard/!ALU/LSR/LSR.kicad_pcb (2023-02-18)

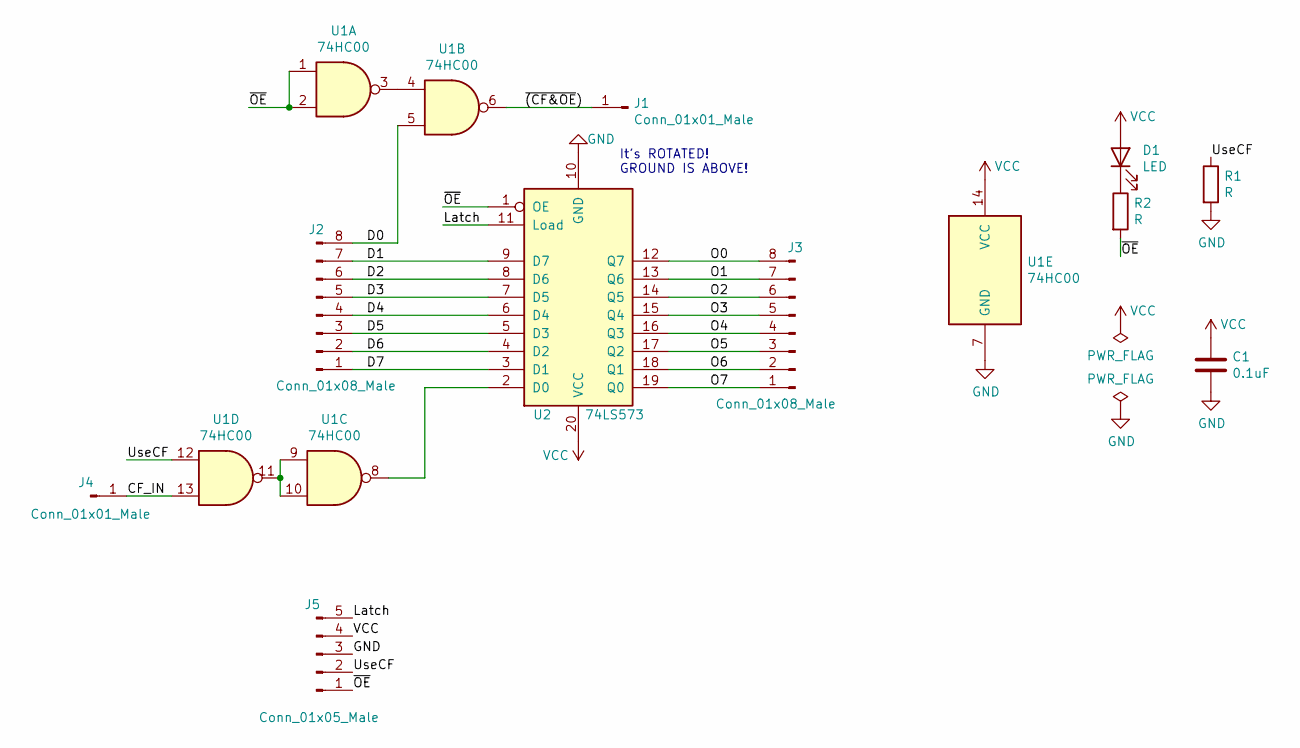
[picture p118: schematic LSR.sch]

Parts:
C1: 0.1uF; C_0805_2012Metric_Pad1.18x1.45mm_HandSolder
D1: LED; LED_0805_2012Metric_Pad1.15x1.40mm_HandSolder
J1, J4: Conn_01x01_Male; PinHeader_1x01_P2.54mm_Vertical
J2, J3: Conn_01x08_Male; PinHeader_1x08_P2.54mm_Horizontal
J5: Conn_01x05_Male; PinHeader_1x05_P2.54mm_Horizontal
R1, R2: R; R_0805_2012Metric_Pad1.20x1.40mm_HandSolder
U1: 74HC00; SO-14_3.9x8.65mm_P1.27mm
U2: 74LS573; SOIC-20W_7.5x12.8mm_P1.27mm

Connections:
/CF_IN: J4.1, U1.13
/D0: J2.8, U1.5
/D1: J2.7, U2.9 (D7)
/D2: J2.6, U2.8 (D6)
/D3: J2.5, U2.7 (D5)
/D4: J2.4, U2.6 (D4)
/D5: J2.3, U2.5 (D3)
/D6: J2.2, U2.4 (D2)
/D7: J2.1, U2.3 (D1)
/Latch: J5.5, U2.11 (Load)
/O0: J3.8, U2.12 (Q7)
/O1: J3.7, U2.13 (Q6)
/O2: J3.6, U2.14 (Q5)
/O3: J3.5, U2.15 (Q4)
/O4: J3.4, U2.16 (Q3)
/O5: J3.3, U2.17 (Q2)
/O6: J3.2, U2.18 (Q1)
/O7: J3.1, U2.19 (Q0)
/UseCF: J5.2, R1.1, U1.12
/~(CF&OE): J1.1, U1.6
/~OE: J5.1, R2.2, U1.1, U1.2, U2.1 (OE)
GND: C1.2, J5.3, R1.2, U1.7 (GND), U2.10 (GND)
unnamed: D1.1 (K), R2.1
unnamed: U1.3, U1.4
unnamed: U1.8, U2.2 (D0)
unnamed: U1.9, U1.10, U1.11
VCC: C1.1, D1.2 (A), J5.4, U1.14 (VCC), U2.20 (VCC)

Notes on the sheet:
It's ROTATED! GROUND IS ABOVE!

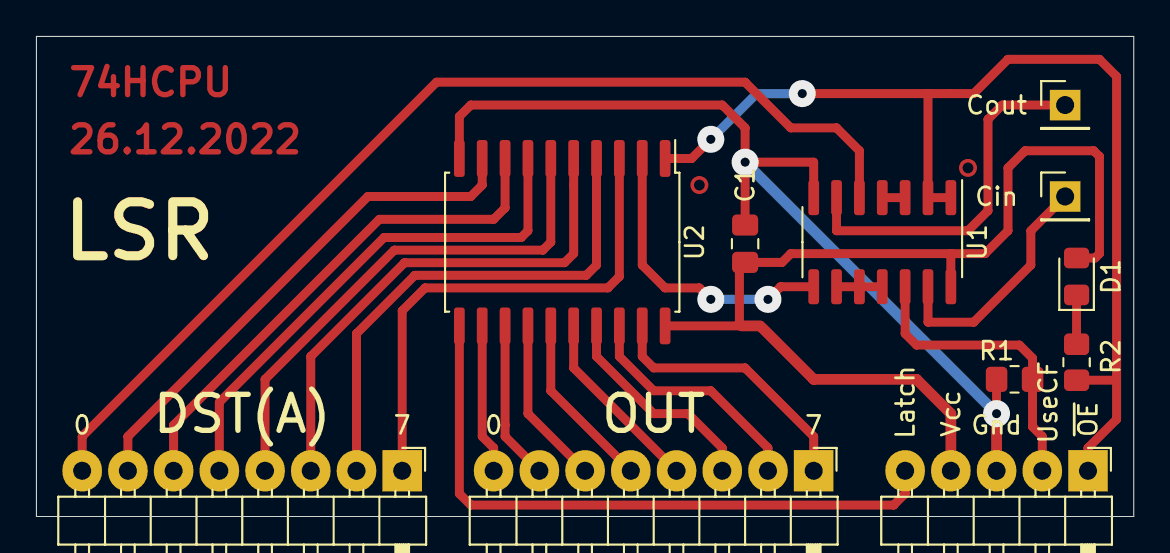
[picture p119: board LSR.kicad_pcb from above]

Board: 2 copper layers, 61.0 x 26.7 mm, 11 parts (0 on the bottom side), 27 nets.
