TheJustMoose/74HC-CPU/Trash/LSL/LSL.sch

## KiCad design Trash/LSL/LSL.sch (2022-12-26)

Schematic: LSL.sch

Parts:
C1: 0.1uF; C_0805_2012Metric_Pad1.18x1.45mm_HandSolder
D1: LED; LED_0805_2012Metric_Pad1.15x1.40mm_HandSolder
J1, J4: Conn_01x01_Male; PinHeader_1x01_P2.54mm_Vertical
J2, J3: Conn_01x08_Male; PinHeader_1x08_P2.54mm_Horizontal
J5: Conn_01x05_Male; PinHeader_1x05_P2.54mm_Horizontal
R1, R2: R; R_0805_2012Metric_Pad1.20x1.40mm_HandSolder
U1: 74HC00; SO-14_3.9x8.65mm_P1.27mm
U2: 74LS573; SOIC-20W_7.5x12.8mm_P1.27mm

Notes on the sheet:
It's ROTATED! GROUND IS ABOVE!
