TheJustMoose/74HC-CPU/Trash/MUL1_SMD/MUL1_SMD.sch

## KiCad design Trash/MUL1_SMD/MUL1_SMD.sch (2024-03-12)

Schematic: MUL1_SMD.sch

Parts:
C1, C2: 0.1uF; C_Axial_L3.8mm_D2.6mm_P12.50mm_Horizontal
J1, J3: Conn_01x08_Male; PinHeader_1x08_P2.54mm_Horizontal
J2: Conn_01x09_Male; PinHeader_1x09_P2.54mm_Horizontal
J4: Conn_01x01_Male; PinHeader_1x01_P2.54mm_Horizontal
J5: Conn_01x02_Male; PinHeader_1x02_P2.54mm_Horizontal
J6: Conn_01x01_Male; PinHeader_1x01_P2.54mm_Vertical
R1: 10k; R_0805_2012Metric_Pad1.20x1.40mm_HandSolder
U1, U3: 74LS08; SOIC-14_3.9x8.7mm_P1.27mm
U2, U4: 74LS283; SOP-16_3.9x9.9mm_P1.27mm

Notes on the sheet:
B[i]
