TheJustMoose/74HC-CPU/Trash/MUX8x1-v5/MUX8x1-v5.sch

## KiCad design Trash/MUX8x1-v5/MUX8x1-v5.sch (2023-07-28)

Schematic: MUX8x1-v5.sch

Parts:
C1, C2, C3, C4, C5, C6, C7, C8, C9: 0.1uF; C_Axial_L5.1mm_D3.1mm_P15.00mm_Horizontal
D1, D2, D3: LED; LED_0805_2012Metric_Pad1.15x1.40mm_HandSolder
H1, H2, H3, H4: MountingHole; MountingHole_3.2mm_M3
J1, J2, J3, J4, J5, J6, J8, J11, J12, J14, J15, J16, J18, J21: Conn_01x09_Male; PinHeader_1x09_P2.54mm_Vertical
J7, J13, J20: Conn_01x01_Male; PinHeader_1x01_P2.54mm_Vertical
J9: Screw_Terminal_01x02; TerminalBlock_Phoenix_MKDS-1,5-2_1x02_P5.00mm_Horizontal
J10: Conn_01x03_Male; PinHeader_1x03_P2.54mm_Vertical
R1, R2, R3, R7: 10k; R_0805_2012Metric_Pad1.20x1.40mm_HandSolder
R4, R5, R6: 1k; R_0805_2012Metric_Pad1.20x1.40mm_HandSolder
U1, U2, U3, U4, U5, U6, U7, U8: 74LS151; DIP-16_W7.62mm_Socket
U9: 74HC245; DIP-20_W7.62mm_Socket
