TheJustMoose/74HC-CPU/Trash/MUX/MUX.sch

## KiCad design Trash/MUX/MUX.sch (2022-05-20)

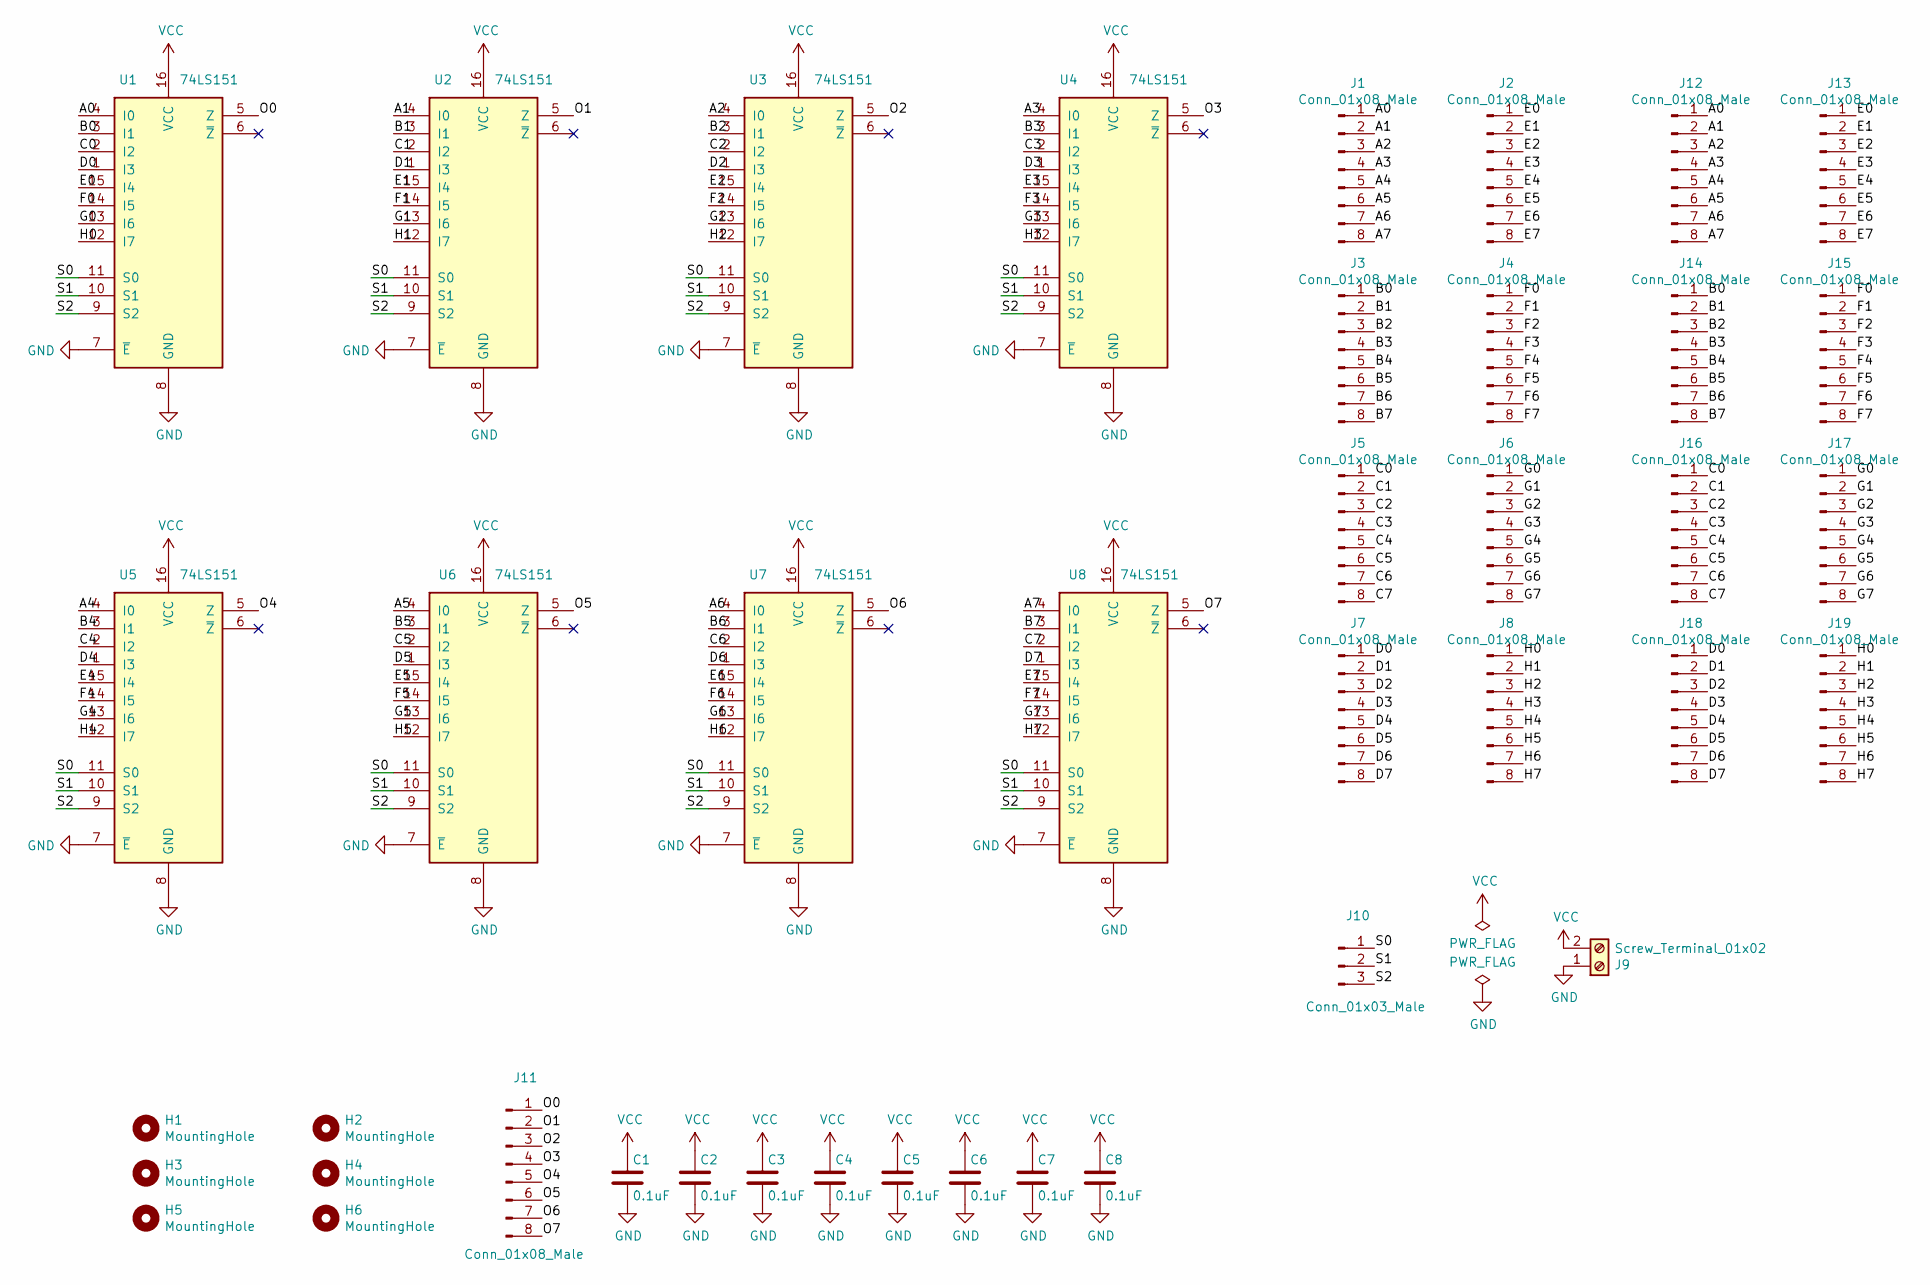
[picture p120: schematic MUX.sch]

Parts:
C1, C2, C3, C4, C5, C6, C7, C8: 0.1uF; C_0805_2012Metric_Pad1.18x1.45mm_HandSolder
H1, H2, H3, H4, H5, H6: MountingHole; MountingHole_3.2mm_M3
J1, J2, J3, J4, J5, J6, J7, J8, J11, J12, J13, J14, J15, J16, J17, J18, J19: Conn_01x08_Male; PinHeader_1x08_P2.54mm_Vertical
J9: Screw_Terminal_01x02; TerminalBlock_Phoenix_MKDS-1,5-2_1x02_P5.00mm_Horizontal
J10: Conn_01x03_Male; PinHeader_1x03_P2.54mm_Vertical
U1, U2, U3, U4, U5, U6, U7, U8: 74LS151; DIP-16_W7.62mm_Socket

Connections:
A0: J1.1, J12.1, U1.4 (I0)
A1: J1.2, J12.2, U2.4 (I0)
A2: J1.3, J12.3, U3.4 (I0)
A3: J1.4, J12.4, U4.4 (I0)
A4: J1.5, J12.5, U5.4 (I0)
A5: J1.6, J12.6, U6.4 (I0)
A6: J1.7, J12.7, U7.4 (I0)
A7: J1.8, J12.8, U8.4 (I0)
B0: J3.1, J14.1, U1.3 (I1)
B1: J3.2, J14.2, U2.3 (I1)
B2: J3.3, J14.3, U3.3 (I1)
B3: J3.4, J14.4, U4.3 (I1)
B4: J3.5, J14.5, U5.3 (I1)
B5: J3.6, J14.6, U6.3 (I1)
B6: J3.7, J14.7, U7.3 (I1)
B7: J3.8, J14.8, U8.3 (I1)
C0: J5.1, J16.1, U1.2 (I2)
C1: J5.2, J16.2, U2.2 (I2)
C2: J5.3, J16.3, U3.2 (I2)
C3: J5.4, J16.4, U4.2 (I2)
C4: J5.5, J16.5, U5.2 (I2)
C5: J5.6, J16.6, U6.2 (I2)
C6: J5.7, J16.7, U7.2 (I2)
C7: J5.8, J16.8, U8.2 (I2)
D0: J7.1, J18.1, U1.1 (I3)
D1: J7.2, J18.2, U2.1 (I3)
D2: J7.3, J18.3, U3.1 (I3)
D3: J7.4, J18.4, U4.1 (I3)
D4: J7.5, J18.5, U5.1 (I3)
D5: J7.6, J18.6, U6.1 (I3)
D6: J7.7, J18.7, U7.1 (I3)
D7: J7.8, J18.8, U8.1 (I3)
E0: J2.1, J13.1, U1.15 (I4)
E1: J2.2, J13.2, U2.15 (I4)
E2: J2.3, J13.3, U3.15 (I4)
E3: J2.4, J13.4, U4.15 (I4)
E4: J2.5, J13.5, U5.15 (I4)
E5: J2.6, J13.6, U6.15 (I4)
E6: J2.7, J13.7, U7.15 (I4)
E7: J2.8, J13.8, U8.15 (I4)
F0: J4.1, J15.1, U1.14 (I5)
F1: J4.2, J15.2, U2.14 (I5)
F2: J4.3, J15.3, U3.14 (I5)
F3: J4.4, J15.4, U4.14 (I5)
F4: J4.5, J15.5, U5.14 (I5)
F5: J4.6, J15.6, U6.14 (I5)
F6: J4.7, J15.7, U7.14 (I5)
F7: J4.8, J15.8, U8.14 (I5)
G0: J6.1, J17.1, U1.13 (I6)
G1: J6.2, J17.2, U2.13 (I6)
G2: J6.3, J17.3, U3.13 (I6)
G3: J6.4, J17.4, U4.13 (I6)
G4: J6.5, J17.5, U5.13 (I6)
G5: J6.6, J17.6, U6.13 (I6)
G6: J6.7, J17.7, U7.13 (I6)
G7: J6.8, J17.8, U8.13 (I6)
GND: C1.2, C2.2, C3.2, C4.2, C5.2, C6.2, C7.2, C8.2, J9.1, U1.7 (~E), U1.8 (GND), U2.7 (~E), U2.8 (GND), U3.7 (~E), U3.8 (GND), U4.7 (~E), U4.8 (GND), U5.7 (~E), U5.8 (GND), U6.7 (~E), U6.8 (GND), U7.7 (~E), U7.8 (GND), U8.7 (~E), U8.8 (GND)
H0: J8.1, J19.1, U1.12 (I7)
H1: J8.2, J19.2, U2.12 (I7)
H2: J8.3, J19.3, U3.12 (I7)
H3: J8.4, J19.4, U4.12 (I7)
H4: J8.5, J19.5, U5.12 (I7)
H5: J8.6, J19.6, U6.12 (I7)
H6: J8.7, J19.7, U7.12 (I7)
H7: J8.8, J19.8, U8.12 (I7)
O0: J11.1, U1.5 (Z)
O1: J11.2, U2.5 (Z)
O2: J11.3, U3.5 (Z)
O3: J11.4, U4.5 (Z)
O4: J11.5, U5.5 (Z)
O5: J11.6, U6.5 (Z)
O6: J11.7, U7.5 (Z)
O7: J11.8, U8.5 (Z)
S0: J10.1, U1.11 (S0), U2.11 (S0), U3.11 (S0), U4.11 (S0), U5.11 (S0), U6.11 (S0), U7.11 (S0), U8.11 (S0)
S1: J10.2, U1.10 (S1), U2.10 (S1), U3.10 (S1), U4.10 (S1), U5.10 (S1), U6.10 (S1), U7.10 (S1), U8.10 (S1)
S2: J10.3, U1.9 (S2), U2.9 (S2), U3.9 (S2), U4.9 (S2), U5.9 (S2), U6.9 (S2), U7.9 (S2), U8.9 (S2)
VCC: C1.1, C2.1, C3.1, C4.1, C5.1, C6.1, C7.1, C8.1, J9.2, U1.16 (VCC), U2.16 (VCC), U3.16 (VCC), U4.16 (VCC), U5.16 (VCC), U6.16 (VCC), U7.16 (VCC), U8.16 (VCC)
