TheJustMoose/74HC-CPU/Trash/Regs-v3/Regs-v3.sch

## KiCad design Trash/Regs-v3/Regs-v3.sch (2024-01-21)

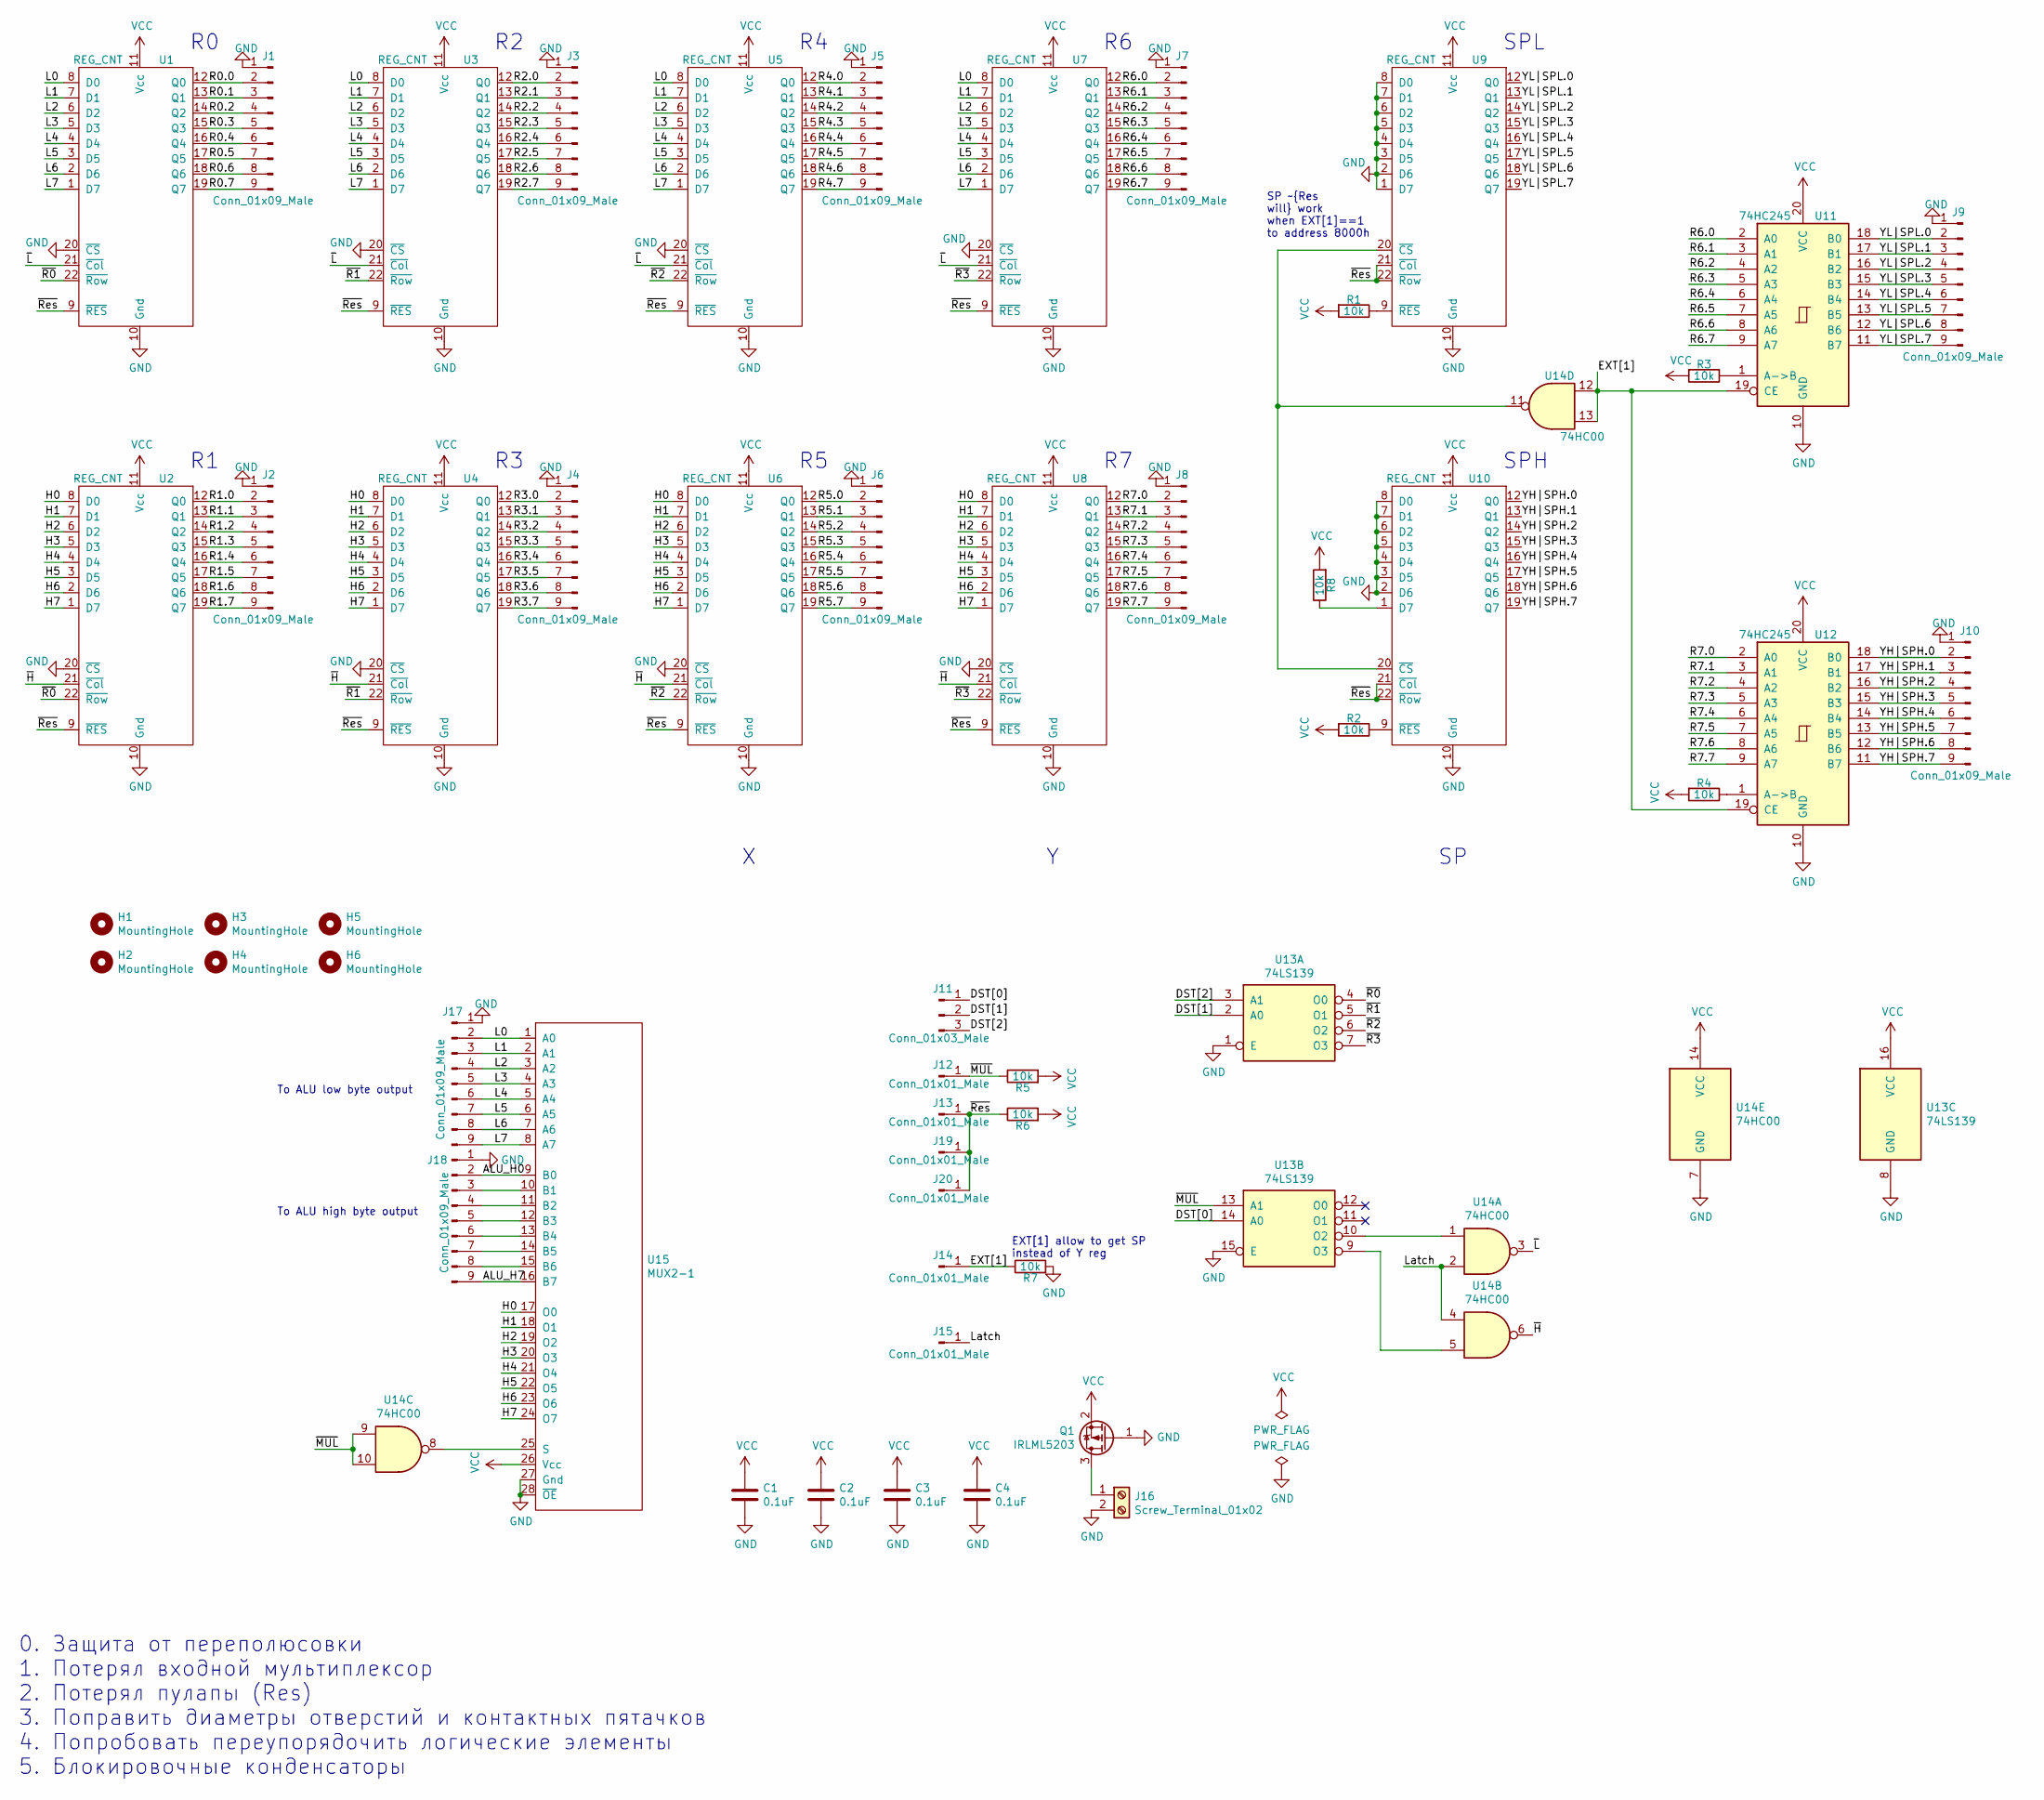
[picture p121: schematic Regs-v3.sch]

Parts:
C1, C2, C3, C4: 0.1uF; C_0805_2012Metric_Pad1.18x1.45mm_HandSolder
H1, H2, H3, H4, H5, H6: MountingHole; MountingHole_3.2mm_M3
J1, J2, J3, J4, J5, J6, J7, J8, J9, J10, J17, J18: Conn_01x09_Male; PinHeader_1x09_P2.54mm_Vertical
J11: Conn_01x03_Male; PinHeader_1x03_P2.54mm_Vertical
J12, J13, J14, J15, J19, J20: Conn_01x01_Male; PinHeader_1x01_P2.54mm_Vertical
J16: Screw_Terminal_01x02; TerminalBlock_Phoenix_MKDS-1,5-2_1x02_P5.00mm_Horizontal
Q1: IRLML5203; SOT-23
R1, R2, R3, R4, R5, R6, R7, R8: 10k; R_0805_2012Metric_Pad1.20x1.40mm_HandSolder
U1, U2, U3, U4, U5, U6, U7, U8, U9, U10: REG_CNT
U11, U12: 74HC245; DIP-20_W7.62mm_Socket
U13: 74LS139; DIP-16_W7.62mm_Socket
U14: 74HC00; DIP-14_W7.62mm_Socket
U15: MUX2-1; CMDwoC

Connections:
ALU_H0: J18.2, U15.9 (B0)
ALU_H7: J18.9, U15.16 (B7)
DST[0]: J11.1, U13.14 (A0)
DST[1]: J11.2, U13.2 (A0)
DST[2]: J11.3, U13.3 (A1)
EXT[1]: J14.1, R7.1, U11.19 (CE), U12.19 (CE), U14.12, U14.13
GND: C1.2, C2.2, C3.2, C4.2, J1.1, J2.1, J3.1, J4.1, J5.1, J6.1, J7.1, J8.1, J9.1, J10.1, J16.2, J17.1, J18.1, Q1.1 (G), R7.2, U1.10 (Gnd), U1.20 (~CS), U2.10 (Gnd), U2.20 (~CS), U3.10 (Gnd), U3.20 (~CS), U4.10 (Gnd), U4.20 (~CS), U5.10 (Gnd), U5.20 (~CS), U6.10 (Gnd), U6.20 (~CS), U7.10 (Gnd), U7.20 (~CS), U8.10 (Gnd), U8.20 (~CS), U9.1 (D7), U9.2 (D6), U9.3 (D5), U9.4 (D4), U9.5 (D3), U9.6 (D2), U9.7 (D1), U9.8 (D0), U9.10 (Gnd), U10.2 (D6), U10.3 (D5), U10.4 (D4), U10.5 (D3), U10.6 (D2), U10.7 (D1), U10.8 (D0), U10.10 (Gnd), U11.10 (GND), U12.10 (GND), U13.1 (E), U13.8 (GND), U13.15 (E), U14.7 (GND), U15.27 (Gnd), U15.28 (~OE)
H0: U2.8 (D0), U4.8 (D0), U6.8 (D0), U8.8 (D0), U15.17 (O0)
H1: U2.7 (D1), U4.7 (D1), U6.7 (D1), U8.7 (D1), U15.18 (O1)
H2: U2.6 (D2), U4.6 (D2), U6.6 (D2), U8.6 (D2), U15.19 (O2)
H3: U2.5 (D3), U4.5 (D3), U6.5 (D3), U8.5 (D3), U15.20 (O3)
H4: U2.4 (D4), U4.4 (D4), U6.4 (D4), U8.4 (D4), U15.21 (O4)
H5: U2.3 (D5), U4.3 (D5), U6.3 (D5), U8.3 (D5), U15.22 (O5)
H6: U2.2 (D6), U4.2 (D6), U6.2 (D6), U8.2 (D6), U15.23 (O6)
H7: U2.1 (D7), U4.1 (D7), U6.1 (D7), U8.1 (D7), U15.24 (O7)
L0: J17.2, U1.8 (D0), U3.8 (D0), U5.8 (D0), U7.8 (D0), U15.1 (A0)
L1: J17.3, U1.7 (D1), U3.7 (D1), U5.7 (D1), U7.7 (D1), U15.2 (A1)
L2: J17.4, U1.6 (D2), U3.6 (D2), U5.6 (D2), U7.6 (D2), U15.3 (A2)
L3: J17.5, U1.5 (D3), U3.5 (D3), U5.5 (D3), U7.5 (D3), U15.4 (A3)
L4: J17.6, U1.4 (D4), U3.4 (D4), U5.4 (D4), U7.4 (D4), U15.5 (A4)
L5: J17.7, U1.3 (D5), U3.3 (D5), U5.3 (D5), U7.3 (D5), U15.6 (A5)
L6: J17.8, U1.2 (D6), U3.2 (D6), U5.2 (D6), U7.2 (D6), U15.7 (A6)
L7: J17.9, U1.1 (D7), U3.1 (D7), U5.1 (D7), U7.1 (D7), U15.8 (A7)
Latch: J15.1, U14.2, U14.4
unnamed: J16.1, Q1.3 (D)
unnamed: J18.3, U15.10 (B1)
unnamed: J18.4, U15.11 (B2)
unnamed: J18.5, U15.12 (B3)
unnamed: J18.6, U15.13 (B4)
unnamed: J18.7, U15.14 (B5)
unnamed: J18.8, U15.15 (B6)
unnamed: R1.1, U9.9 (~RES)
unnamed: R2.1, U10.9 (~RES)
unnamed: R3.1, U11.1 (A->B)
unnamed: R4.1, U12.1 (A->B)
unnamed: R8.1, U10.1 (D7)
unnamed: U9.20 (~CS), U10.20 (~CS), U14.11
unnamed: U13.9 (O3), U14.5
unnamed: U13.10 (O2), U14.1
unnamed: U14.8, U15.25 (S)
R0.0: J1.2, U1.12 (Q0)
R0.1: J1.3, U1.13 (Q1)
R0.2: J1.4, U1.14 (Q2)
R0.3: J1.5, U1.15 (Q3)
R0.4: J1.6, U1.16 (Q4)
R0.5: J1.7, U1.17 (Q5)
R0.6: J1.8, U1.18 (Q6)
R0.7: J1.9, U1.19 (Q7)
R1.0: J2.2, U2.12 (Q0)
R1.1: J2.3, U2.13 (Q1)
R1.2: J2.4, U2.14 (Q2)
R1.3: J2.5, U2.15 (Q3)
R1.4: J2.6, U2.16 (Q4)
R1.5: J2.7, U2.17 (Q5)
R1.6: J2.8, U2.18 (Q6)
R1.7: J2.9, U2.19 (Q7)
R2.0: J3.2, U3.12 (Q0)
R2.1: J3.3, U3.13 (Q1)
R2.2: J3.4, U3.14 (Q2)
R2.3: J3.5, U3.15 (Q3)
R2.4: J3.6, U3.16 (Q4)
R2.5: J3.7, U3.17 (Q5)
R2.6: J3.8, U3.18 (Q6)
R2.7: J3.9, U3.19 (Q7)
R3.0: J4.2, U4.12 (Q0)
R3.1: J4.3, U4.13 (Q1)
R3.2: J4.4, U4.14 (Q2)
R3.3: J4.5, U4.15 (Q3)
R3.4: J4.6, U4.16 (Q4)
R3.5: J4.7, U4.17 (Q5)
R3.6: J4.8, U4.18 (Q6)
R3.7: J4.9, U4.19 (Q7)
R4.0: J5.2, U5.12 (Q0)
R4.1: J5.3, U5.13 (Q1)
R4.2: J5.4, U5.14 (Q2)
R4.3: J5.5, U5.15 (Q3)
R4.4: J5.6, U5.16 (Q4)
R4.5: J5.7, U5.17 (Q5)
R4.6: J5.8, U5.18 (Q6)
R4.7: J5.9, U5.19 (Q7)
R5.0: J6.2, U6.12 (Q0)
R5.1: J6.3, U6.13 (Q1)
R5.2: J6.4, U6.14 (Q2)
R5.3: J6.5, U6.15 (Q3)
R5.4: J6.6, U6.16 (Q4)
R5.5: J6.7, U6.17 (Q5)
R5.6: J6.8, U6.18 (Q6)
R5.7: J6.9, U6.19 (Q7)
R6.0: J7.2, U7.12 (Q0), U11.2 (A0)
R6.1: J7.3, U7.13 (Q1), U11.3 (A1)
R6.2: J7.4, U7.14 (Q2), U11.4 (A2)
R6.3: J7.5, U7.15 (Q3), U11.5 (A3)
R6.4: J7.6, U7.16 (Q4), U11.6 (A4)
R6.5: J7.7, U7.17 (Q5), U11.7 (A5)
R6.6: J7.8, U7.18 (Q6), U11.8 (A6)
R6.7: J7.9, U7.19 (Q7), U11.9 (A7)
R7.0: J8.2, U8.12 (Q0), U12.2 (A0)
R7.1: J8.3, U8.13 (Q1), U12.3 (A1)
R7.2: J8.4, U8.14 (Q2), U12.4 (A2)
R7.3: J8.5, U8.15 (Q3), U12.5 (A3)
R7.4: J8.6, U8.16 (Q4), U12.6 (A4)
R7.5: J8.7, U8.17 (Q5), U12.7 (A5)
R7.6: J8.8, U8.18 (Q6), U12.8 (A6)
R7.7: J8.9, U8.19 (Q7), U12.9 (A7)
VCC: C1.1, C2.1, C3.1, C4.1, Q1.2 (S), R1.2, R2.2, R3.2, R4.2, R5.2, R6.2, R8.2, U1.11 (Vcc), U2.11 (Vcc), U3.11 (Vcc), U4.11 (Vcc), U5.11 (Vcc), U6.11 (Vcc), U7.11 (Vcc), U8.11 (Vcc), U9.11 (Vcc), U10.11 (Vcc), U11.20 (VCC), U12.20 (VCC), U13.16 (VCC), U14.14 (VCC), U15.26 (Vcc)
YH|SPH.0: J10.2, U10.12 (Q0), U12.18 (B0)
YH|SPH.1: J10.3, U10.13 (Q1), U12.17 (B1)
YH|SPH.2: J10.4, U10.14 (Q2), U12.16 (B2)
YH|SPH.3: J10.5, U10.15 (Q3), U12.15 (B3)
YH|SPH.4: J10.6, U10.16 (Q4), U12.14 (B4)
YH|SPH.5: J10.7, U10.17 (Q5), U12.13 (B5)
YH|SPH.6: J10.8, U10.18 (Q6), U12.12 (B6)
YH|SPH.7: J10.9, U10.19 (Q7), U12.11 (B7)
YL|SPL.0: J9.2, U9.12 (Q0), U11.18 (B0)
YL|SPL.1: J9.3, U9.13 (Q1), U11.17 (B1)
YL|SPL.2: J9.4, U9.14 (Q2), U11.16 (B2)
YL|SPL.3: J9.5, U9.15 (Q3), U11.15 (B3)
YL|SPL.4: J9.6, U9.16 (Q4), U11.14 (B4)
YL|SPL.5: J9.7, U9.17 (Q5), U11.13 (B5)
YL|SPL.6: J9.8, U9.18 (Q6), U11.12 (B6)
YL|SPL.7: J9.9, U9.19 (Q7), U11.11 (B7)
~H: U2.21 (~Col), U4.21 (~Col), U6.21 (~Col), U8.21 (~Col), U14.6
~L: U1.21 (~Col), U3.21 (~Col), U5.21 (~Col), U7.21 (~Col), U14.3
~MUL: J12.1, R5.1, U13.13 (A1), U14.9, U14.10
~R0: U1.22 (~Row), U2.22 (~Row), U13.4 (O0)
~R1: U3.22 (~Row), U4.22 (~Row), U13.5 (O1)
~R2: U5.22 (~Row), U6.22 (~Row), U13.6 (O2)
~R3: U7.22 (~Row), U8.22 (~Row), U13.7 (O3)
~Res: J13.1, J19.1, J20.1, R6.1, U1.9 (~RES), U2.9 (~RES), U3.9 (~RES), U4.9 (~RES), U5.9 (~RES), U6.9 (~RES), U7.9 (~RES), U8.9 (~RES), U9.21 (~Col), U9.22 (~Row), U10.21 (~Col), U10.22 (~Row)

Notes on the sheet:
SPL
SPH
0. Защита от переполюсовки 1. Потерял входной мультиплексор 2. Потерял пулапы (Res) 3. Поправить диаметры отверстий и контактных пятачков 4. Попробовать переупорядочить логические элементы 5. Блокировочные конденсаторы
To ALU low byte output
To ALU high byte output
EXT[1] allow to get SP instead of Y reg
SP ~Res will work when EXT[1]==1 to address 8000h
