TheJustMoose/74HC-CPU/Trash/STACK1/STACK1.sch

## KiCad design Trash/STACK1/STACK1.sch (2023-01-12)

Schematic: STACK1.sch

Parts:
C1: 0.1uF; C_0805_2012Metric_Pad1.18x1.45mm_HandSolder
D1, D2, D3, D4, D5, D6, D7, D8: LED; LED_0805_2012Metric_Pad1.15x1.40mm_HandSolder
J1, J2: Conn_01x09_Male; PinHeader_1x09_P2.54mm_Vertical
J3, J4: Conn_01x01_Male; PinHeader_1x01_P2.54mm_Horizontal
R1, R2, R3, R4, R5, R6, R7, R8: 1k; R_0805_2012Metric_Pad1.20x1.40mm_HandSolder
R9: 10k; R_0805_2012Metric_Pad1.20x1.40mm_HandSolder
U1: 74LS574; SO-20_12.8x7.5mm_P1.27mm
