TheJustMoose/74HC-CPU/soft/asm/assm.cc

///////////////////////////////////////////////////////////////////////////////
/*

Ассемблер для моего 74HCPU под новую систему команд:

|----------------------------------------------|f|
|   4   +   3 + 1 + 3  +    5    = 16          |l|
|   HIGH BYTE   |    LOW BYTE    |  HIGH BYTE  |a| * - меняем CF, HCF, ZF (результат сложения) == A-FLAGS (Arithm)
|0 1 2 3  4 5 6 7 8 9 A B C D E F|   (again)   |g| + - меняем LF, EQ, GF (результат сравнения) == C-FLAGS (Compare)
|----------------------------------------------|s|
|   ADD |  DST |C| SRC |-|Z|z|I|i| 00 0000 0000|*| ADDI  R0, 1    // INC R0;
|  ADDC |  DST |C| SRC |F|Z|z|I|i| 10 0001 0000|*| ADDCI R1, 0    // INCC R1;    // бит F нужен для команд -INC-, -DEC-, SUB, -INV-, NEG
|   AND |  DST |C| SRC |-|Z|z|I|i| 20 0010 0000|*| ANDI R2, 0x0F  // здесь есть свободный бит, и вместо F туда можно положить S[WAP] или S[HIFT]
|    OR |  DST |C| SRC |-|Z|z|I|i| 30 0011 0000|*| ORI R3, 2      // в любом случае, сдвиг старшего нибла на место младшего кажется полезным
|   XOR |  DST |C| SRC |-|Z|z|I|i| 40 0100 0000|*| XORI R4, 4     // кстати, в этом случае можно ещё и от команды SWAP избавиться
|   MUL |  DST |C| SRC |-|Z|z|I|i| 50 0101 0000|*| MULI R6, 10    // R7:R6 := R6*10
|   UNO |  DST |0|-|TYP|F|-|-|-|-| 60 0110 0000|*| унарные команды не используют операнд SRC, поэтому нельзя использовать инверторы и отдельные нибблы
|   MOV |  DST |0| SRC |*|Z|z|I|i| 70 0111 0000| | MOVI R5, 5     // LDI R5, 5       // * - можно использовать, чтобы пихать адрес в SPL/SPH (правда, только из других регистров), или для того, чтобы сделать MOVW
|   LPM |  DST |W|EXT|D|U|OFFSET4| 80 1000 0000| | LPM R0, [IX]   // LPM R1, [X+1]   // LPM R1, [DX-1]  // W - читать слово (1) или байт (0)
|    LD |  DST |0|EXT|D|U|OFFSET4| 90 1001 0000| | LD R1, [-Y]    // LD R3, [+SP-1] ; POP R3  // ноль на месте бита C можно использовать как пятый бит OFFSET-а
|    IN |  DST |  PORT   |Z|z|I|i| A0 1010 0000| | IN R2, PIN1    // IN R2, ~PIN1 ; Ii - инвертировать порт перед чтением, Zz - занулять ниббл при чтении (или сделать отдельный IMASK?)
|--------------|7-8-9-A-B|-------|-------------|-| всё что ниже - не модифицирует регистры
|   OUT |  SRC |  PORT   |O|o|X|x| B0 1011 0000| | OUT PORT0, R2  // XOUT PORT0, R2 (вместо Oo можно сделать вчетверо больше регистров!)
|    ST |  SRC |0|EXT|D|U|OFFSET4| C0 1100 0000| | ST [Y], R2     // ST [IX], R2     // ST [Y+2], R2   // ST [-SP], R2 ; PUSH R2
|   CMP |  DST |C| SRC |-|   -   | D0 1101 0000|+| CMPI R3, 10    // CMP  R0, R2
|  CMPC |  DST |C| SRC |-|   -   | E0 1110 0000|+| CMPCI R4, 10   // CMPC R1, R3
| BRNCH |  CALL  | 8 bit OFFSET  | F0 1111 0000| | переход в +-127 команды, значение прибавляется к текущему счётчику команд
| BRNCH |   JMP  | 8 bit OFFSET  | F1 1111 0001| | <- COP low nibble
| BRNCH |   RET  | 8 bit +STACK  | F2 1111 0010| | на сколько байт переместить указатель стека данных, дабы пропустить запушенные параметры
| BRNCH |  RETI  | 8 bit OFFSET  | F3 1111 0011| | RETI           // однако, у меня нет механизма для переставления SP на несколько байт за команду RET
| BRNCH |    JL  | 8 bit OFFSET  | F4 1111 0100| | if (v < w)     // поэтому вместо константы можно воткнуть сюда битик указания на RETI, вместо RET
| BRNCH |    JE  | 8 bit OFFSET  | F5 1111 0101| | if (v == w)    // а не правильней ли будет сделать JLE вдобавок к отдельным JL + JE ?
| BRNCH |   JNE  | 8 bit OFFSET  | F6 1111 0110| | if (v != w)
| BRNCH |    JG  | 8 bit OFFSET  | F7 1111 0111| | if (v > w)     // с другой стороны, эту инструкцию можно эмулировать программно
| BRNCH |    JZ  | 8 bit OFFSET  | F8 1111 1000| | if (v == 0)    // путём переставления регистров и использования JL
| BRNCH |   JNZ  | 8 bit OFFSET  | F9 1111 1001| | if (v != 0)
| BRNCH |    JC  | 8 bit OFFSET  | FA 1111 1010| | if (CF == 1)
| BRNCH |   JNC  | 8 bit OFFSET  | FB 1111 1011| | if (CF == 0)   // выкинуть инструкции, что реально не будут использоваться
| BRNCH |   JHC  | 8 bit OFFSET  | FC 1111 1100| | if (HCF == 1)  // вкрутить что-то вроде NJMP offset (хотя текущий JMP так и делает?)
| BRNCH |  JNHC  | 8 bit OFFSET  | FD 1111 1101| | if (HCF == 0)  // (и делать реальный переход на offset*16, к примеру)
| BRNCH | AFCALL | Hi 8 bit ADDR | FE 1111 1110| | Absolute Far Call - 8 bit ADDR кладём в старшие биты и зануляем младшие
| BRNCH |NOP/STOP|   1111 111x   | FF 1111 1111| | NOP - хорошо бы чтоб имел код 0xFF, это позволит думать, что не прошитая память заполнена NOP-ами
|----------------------------------------------|-| если младший бит 0, то это STOP (отладочный стоп), плюс 7 бит на полёт фантазии
*/
///////////////////////////////////////////////////////////////////////////////

#include <bitset>
#include <cctype>
#include <clocale>
#include <cstdlib>
#include <iomanip>
#include <iostream>
#include <fstream>
#include <limits>
#include <map>
#include <sstream>
#include <string>
#include <vector>

#include "assm.h"
#include "error_collector.h"
#include "file_reader.h"
#include "preprocessor.h"
#include "str_util.h"

using namespace std;

///////////////////////////////////////////////////////////////////////////////

struct ARITHM {
 public:
  uint16_t cop : 4;
  uint16_t dst : 3;
  uint16_t C : 1;
  uint16_t src : 3;
  uint16_t F : 1;
  uint16_t Z : 1;
  uint16_t z : 1;
  uint16_t I : 1;
  uint16_t i : 1;
};

OP_TYPE CopToType(COP cop) {
  if (cop == cNO_OP)
    return tNO_OP;
  else if (cop >= cADD && cop <= cMUL)
    return tBINARY;
  else if (cop == cMOV || cop == cCMP || cop == cCMPC)
    return tBINARY;
  else if (cop == cUNO)
    return tUNARY;
  else if (cop == cLPM || cop == cLPMW || cop == cLD || cop == cST)
    return tMEMORY;
  else if (cop == cIN || cop == cOUT || cop == cTOGL)
    return tIO;
  else if (cop >= bCALL && cop <= bNOP)
    return tBRANCH;
  else  // I don't know when this should work
    return tNO_OP;
}

map<string, uint16_t> unary_codes {
  { "INV", 0x00 },   // 00
  { "SWAP", 0x20 },  // 01
  { "LSR", 0x40 },   // 10
  { "LSRC", 0x60 },  // 11
};

map<string, COP> cop_names {
  { "ADD", cADD}, { "ADDC", cADDC},
  { "AND", cAND}, { "OR", cOR}, { "XOR", cXOR},
  { "MUL", cMUL},
  { "INV", cUNO}, { "SWAP", cUNO}, { "LSR", cUNO}, { "LSRC", cUNO},
  { "MOV", cMOV},
  { "LPM", cLPM}, { "LPMW", cLPMW}, { "LD", cLD}, { "LOAD", cLD},
  { "IN", cIN}, { "OUT", cOUT}, { "TOGL", cTOGL},
  { "ST", cST}, { "STORE", cST},
  { "CMP", cCMP}, { "CMPC", cCMPC},
  { "CALL", bCALL},
  { "JMP", bJMP },
  { "RET", bRET },
  { "RETI", bRETI },
  { "JL", bJL },
  { "JE", bJE },
  { "JNE", bJNE },
  { "JG", bJG },
  { "JZ", bJZ },
  { "JNZ", bJNZ },
  { "JC", bJC },
  { "JNC", bJNC },
  { "JHC", bJHC },
  { "JNHC", bJNHC },
  { "AFCALL", bAFCALL },
  { "NOP", bNOP },
  { "STOP", bSTOP },
};

map<string, REG> reg_names {
  { "R0", rR0 }, { "R1", rR1 }, { "R2", rR2 }, { "R3", rR3 }, { "R4", rR4 }, { "R5", rR5 }, { "R6", rR6 }, { "R7", rR7 },
// R0.L R0.H R1.L R1.H....
  { "XL", rXL}, { "XH", rXH}, { "YL", rYL}, { "YH", rYH}, { "ZL", rZL}, { "ZH", rZH}, { "SPL", rSPL}, { "SPH", rSPH},
};

map<string, PTR> ptr_names {
  { "X", rX }, { "Y", rY }, { "Z", rZ }, { "SP", rSP },
  { "XI", rXI }, { "YI", rYI }, { "ZI", rZI }, { "SPI", rSPI },
  { "XD", rXD }, { "YD", rYD }, { "ZD", rZD }, { "SPD", rSPD },
};

map<string, uint16_t> port_names {
  { "PORT0", 0 }, { "PINS0", 0 },
  { "OMASK0", 1 },
  { "PORT1", 2 }, { "PINS1", 2 },
  { "OMASK0", 3 },
  { "PORT2", 4 },
  { "PORT3", 5 }, { "PINS3", 5 },
  { "PORT4", 6 }, { "PINS4", 6 },
  { "PORT5", 7 }, { "PINS5", 7 },
  { "PORT6", 8 }, { "PINS6", 8 }, { "RAMP", 8 },
  { "PORT7", 9 }, { "PINS7", 9 }, { "MSW", 9 },
  { "PORT8", 10 }, { "PINS8", 10 }, { "FLAGS", 10 },
  { "PORT9", 11 }, { "PINS9", 11 }, { "DAC", 11 },
};

///////////////////////////////////////////////////////////////////////////////

COP Names::CopFromName(string name) {
  if (name.empty())
    return bNOP;

  if (cop_names.find(name) != cop_names.end())
    return cop_names[name];
  else
    return bERROR;
}

REG Names::RegFromName(string name) {
  if (name.empty())
    return rUnkReg;

  if (reg_names.find(name) != reg_names.end())
    return reg_names[name];
  else
    return rUnkReg;
}

PTR Names::PtrFromName(string name, bool* inc = nullptr, bool* dec = nullptr) {
  if (name.empty())
    return rUnkPtr;

  size_t len = 0;
  while (len < name.size() && isalpha(name[len]))
    len++;
  if (len != name.size())
    name.resize(len);

  PTR ptr {rUnkPtr};
  if (ptr_names.find(name) != ptr_names.end()) {
    ptr = ptr_names[name];
    if (inc)
      *inc = ptr & rInc;
    if (dec)
      *dec = ptr & rDec;
    return (PTR)(ptr & rMask);
  } else {
    return rUnkPtr;
  }
}

int Names::PortFromName(string name, string prefix) {
  if (name.empty())
    return -1;

  if (port_names.find(name) == port_names.end())
    return -1;

  return port_names[name];
}

///////////////////////////////////////////////////////////////////////////////

// ADD R0, R1
// ADD R2, 10
class BinaryCodeGen: public CodeGen {
 public:
  BinaryCodeGen(int line_number, COP cop, string left, string right)
    : CodeGen(line_number, cop), right_str_(right) {
    left_op_ = Names::RegFromName(left);
    if (left_op_ == rUnkReg)
      ErrorCollector::GetInstance().err("Unknown register: " + left, line_number);
    TryImmediate(right);
  }

  void TryImmediate(string right) {
    int t = 0;
    immediate_ = StrToInt(right, &t);  // MOV R1, 10
    if (immediate_) {
      if (t < 0)
        right_val_ = t & 0x00FF;
      else
        right_val_ = t;

      if (right_val_> 0xFF)
        ErrorCollector::GetInstance().err("Error. Immediate value should have 8 bit only (0 - 255). Got: " + right, line_number());
    }

    if (!immediate_) {  // not val, try to check register name
      right_op_ = Names::RegFromName(right);  // MOV R0, R1
      if (right_op_ == rUnkReg) {
        ErrorCollector::GetInstance().err("Unknown register: " + right_str_, line_number());
        ErrorCollector::GetInstance().err("You have to use Register name or immediate value as rval.", line_number());
      } else
        right_str_ = "";
    }
  }

  uint16_t Emit() {
    uint16_t cop = operation_;
    cop |= left_op_ << 9;  // don't forget about C bit
    if (immediate_) {
      cop |= right_val_;
      cop |= 0x0100;  // set C bit to 1
    }
    else
      cop |= right_op_ << 5;
    return cop;
  }

  void update_machine_code(const map<string, uint16_t>& name_to_address) {
    if (right_str_.empty())
      return;

    bool hi {false};
    if (right_str_.find("LO(") == 0)
      right_str_ = right_str_.substr(3, right_str_.size() - 4);
    else if (right_str_.find("HI(") == 0) {
      right_str_ = right_str_.substr(3, right_str_.size() - 4);
      hi = true;
    }

    map<string, uint16_t>::const_iterator it;
    for (it = name_to_address.begin(); it != name_to_address.end(); it++) {
      string t = ToUpper(it->first);
      if (t == right_str_)
        break;
    }

    if (it == name_to_address.end())
      return;

    ErrorCollector::GetInstance().clr(line_number());  // have to remove previous messages
                                         // cause RegFromName know nothing about labels and LO/HI macro
    ErrorCollector::GetInstance().rep("Replace " + it->first + " to " + to_string(it->second), line_number());

    right_val_ = it->second;
    if (hi)
      right_val_ >>= 8;
    right_val_ &= 0x00FF;
    immediate_ = true;
  }

  vector<int> get_blocks() {
    if (immediate_)
      //    COP dst C value
      return {4, 3, 1, 8};
    else
      //    COP dst C src F
      return {4, 3, 1, 3, 1};
  }

 private:
  REG left_op_ {rUnkReg};
  REG right_op_ {rUnkReg};
  uint16_t right_val_ {0};
  bool immediate_ {false};
  string right_str_ {};  // TODO: try to remove it later
};

// LSR R7
class UnaryCodeGen: public CodeGen {
 public:
  UnaryCodeGen(int line_number, string op_name, string reg)
    : CodeGen(line_number, cUNO), op_name_(op_name) {
    reg_ = Names::RegFromName(reg);
    if (reg_ == rUnkReg)
      ErrorCollector::GetInstance().err("Unknown register: " + reg, line_number);
    if (unary_codes.find(op_name) != unary_codes.end())
      ucode_ = unary_codes[op_name];
    else {
      ucode_ = 0;
      ErrorCollector::GetInstance().err("Unknown unary operation ", line_number);
    }
  }

  uint16_t Emit() {
    uint16_t cop = operation_;
    cop |= ucode_;
    cop |= reg_ << 9;  // don't forget about C bit
    return cop;
  }

  vector<int> get_blocks() {
    //    COP reg 0  - TYP F
    return {4, 3, 1, 1, 2, 1};
  }

 private:
  string op_name_;
  uint16_t ucode_ {0};
  REG reg_ {rUnkReg};
};

// LD R0, X
// LD R1, XI + 10
class MemoryCodeGen: public CodeGen {
 public:
  MemoryCodeGen(int line_number, COP cop, string left, string right)
    : CodeGen(line_number, cop) {
    if (cop == cLD || cop == cLPM || cop == cLPMW) {
      reg_ = Names::RegFromName(left);
      if (reg_ == rUnkReg)
        ErrorCollector::GetInstance().err("Unknown register: " + left, line_number);
      ptr_ = Names::PtrFromName(right, &inc_, &dec_);
      if (ptr_ == rUnkPtr)
        ErrorCollector::GetInstance().err("Unknown pointer register: " + right, line_number);
      offset_ = parse_offset(right);
    } else if (cop == cST) {
      ptr_ = Names::PtrFromName(left, &inc_, &dec_);
      if (ptr_ == rUnkPtr)
        ErrorCollector::GetInstance().err("Unknown pointer register: " + left, line_number);
      reg_ = Names::RegFromName(right);
      if (reg_ == rUnkReg)
        ErrorCollector::GetInstance().err("Unknown register: " + right, line_number);
      offset_ = parse_offset(left);
    } else {
      ErrorCollector::GetInstance().err("Unknown memory operation. Should be LD or ST or LPM.", line_number);
    }
  }

  uint16_t parse_offset(string tail) {
    if (tail.empty())
      return 0;

    while (tail.size() && isalpha(*tail.begin()))
      tail = tail.erase(0, 1);

    if (tail.empty())
      return 0;

    if (tail[0] != '+' && tail[0] != '-') {
      ErrorCollector::GetInstance().err("You can add or substract offset from pointer register. No other operations.", line_number());
      return 0;
    }

    if (tail.size() < 2) {
      ErrorCollector::GetInstance().err("You lost offset value.", line_number());
      return 0;
    }

    uint16_t res {0};
    int off = stoi(&tail[1], nullptr, 10);
    if (tail[0] == '-')
      off = -off;
    if (off > 7)
      ErrorCollector::GetInstance().err("Offset has to be <= 7.", line_number());
    else if (off < -8)
      ErrorCollector::GetInstance().err("Offset has to be >= -8.", line_number());
    else
      res = off & 0x0F;  // we need only 4 bits
    return res;
  }

  uint16_t Emit() {
    uint16_t cop = operation_;
    cop |= reg_ << 9;  // don't forget about C bit
    cop |= ptr_ << 6;
    cop |= dec_ << 5;
    cop |= inc_ << 4;
    cop |= offset_;
    return cop;
  }

  vector<int> get_blocks() {
    //    COP dst 0 EXT D  U  OFFSET
    return {4, 3, 1, 2, 1, 1, 4};
  }

 private:
  REG reg_ {rUnkReg};
  PTR ptr_ {rUnkPtr};
  bool inc_ {false};  // post increment ptr_
  bool dec_ {false};  // post decrement ptr_
  uint16_t offset_ {0};
};

// IN R0, PORT1
class IOCodeGen: public CodeGen {
 public:
  IOCodeGen(int line_number, COP cop, string left, string right)
    : CodeGen(line_number, cop) {
    if (cop == cIN) {
      reg_ = Names::RegFromName(left);
      if (reg_ == rUnkReg)
        ErrorCollector::GetInstance().err("Unknown register: " + left, line_number);

      int p = Names::PortFromName(right, "PIN");
      if (p == -1)
        ErrorCollector::GetInstance().err("Unknown port name: " + right, line_number);
      else if (p >= 32)
        ErrorCollector::GetInstance().err("Port number should be in range 0-31", line_number);
      else
        port_ = p;
    } else if (cop == cOUT || cop == cTOGL) {
      int p = Names::PortFromName(left, "PORT");
      if (p == -1)
        ErrorCollector::GetInstance().err("Unknown port name: " + left, line_number);
      else if (p >= 32)
        ErrorCollector::GetInstance().err("Port number should be in range 0-31", line_number);
      else
        port_ = p;

      reg_ = Names::RegFromName(right);
      if (reg_ == rUnkReg)
        ErrorCollector::GetInstance().err("Unknown register: " + right, line_number);
    } else {
      ErrorCollector::GetInstance().err("Unknown IO operation. Should be IN or OUT.", line_number);
    }
  }

  uint16_t Emit() {
    uint16_t cop = operation_;
    cop |= reg_ << 9;
    cop |= port_ << 4;
    return cop;
  }

  vector<int> get_blocks() {
    //   COP dst port -- Ii
    //   COP src port Oo Xx
    return {4, 3, 5, 2, 2};
  }

 private:
  REG reg_ {rUnkReg};
  uint16_t port_ {0};
};

class BranchCodeGen: public CodeGen {
 public:
  BranchCodeGen(int line_number, COP cop, string label)
    : CodeGen(line_number, cop), label_(label) {}

  uint16_t Emit() {
    uint16_t cop = operation_;
    cop |= (uint16_t)target_addr_;
    if (operation_ == bNOP)
      cop |= 0xFF;
    return cop;
  }

  void update_machine_code(const map<string, uint16_t>& name_to_address) {
    map<string, uint16_t>::const_iterator it;
    for (it = name_to_address.begin(); it != name_to_address.end(); it++) {
      if (ToUpper(it->first) == label_) {
        uint16_t label_addr = it->second;
        if (operation_ == bAFCALL) {
          if (label_addr % 256) {
            ErrorCollector::GetInstance().err(
                "Label address in far call must be a multiple of 256. Now addr: "
                + to_string(label_addr), line_number());
          }
          target_addr_ = label_addr >> 8;  // absolute address divided by 256
        } else {
          int offset = label_addr;
          offset -= address_;         // offset from current address
          if (offset > 127 || offset < -128)
            ErrorCollector::GetInstance().err(
                "Error: Label " + label_ + " is too far from this instruction: "
                + to_string(offset), line_number());
          else
            target_addr_ = offset & 0xFF;
        }
        //cout << "new target address: " << hex << target_addr_ << endl;
      }
    }
  }

  vector<int> get_blocks() {
    //    COP TYP offset/addr
    return {4, 4, 8};
  }

 private:
  string label_;
  uint16_t target_addr_ {0};
};

///////////////////////////////////////////////////////////////////////////////

CodeLine::CodeLine(int line_number, string line_text)
  : line_number_(line_number), line_text_(line_text) {

  size_t pos = line_text_.find(":");
  while (pos != string::npos) {
    string label = line_text_.substr(0, pos);
    if (!label.empty()) {
      labels_.push_back(label);
      //cout << "label: " << label << endl;
    }
    line_text_.erase(0, pos + 1);
    pos = line_text_.find(":");
  }
  //cout << "code line w/o label: " << line_text_ << endl;

  vector<string> cmd_parts = SplitToCmdParts(line_text_);
  if (cmd_parts.size() != 3) {
    cout << "Error. SplitToCmdParts should always return 3 items.";
    return;
  }

  string op_name( cmd_parts[0] );
  string left( cmd_parts[1] );
  string right( cmd_parts[2] );

  COP op = Names::CopFromName(op_name);
  if (op == bERROR) {
    ErrorCollector::GetInstance().err("Unknown operation: " + op_name, line_number);
    cout << "Error. Unknown operation: |" << op_name << "|" << endl;
    return;
  }

  OP_TYPE opt = CopToType(op);
  //cout << "Operation type: " << opt << endl;

  CodeGen* cg {nullptr};
  switch (opt) {
    case tBINARY: cg = new BinaryCodeGen(line_number_, op, left, right); break;
    case tUNARY: cg = new UnaryCodeGen(line_number_, op_name, left); break;
    case tMEMORY: cg = new MemoryCodeGen(line_number_, op, left, right); break;
    case tIO: cg = new IOCodeGen(line_number_, op, left, right); break;
    case tBRANCH: cg = new BranchCodeGen(line_number_, op, left); break;
    case tNO_OP:
    default:
      cout << "No operation is required" << endl;
  }

  code_gen_.reset(cg);

  //cout << "GOT: |" << op_name << "|" << left << "|" << right << "|" << endl;
}

uint16_t CodeLine::generate_machine_code() {
  if (!code_gen_)
    return bNOP | 0xFF;

  uint16_t cop = code_gen_->Emit();
  return cop;
}

void CodeLine::update_machine_code(const map<string, uint16_t>& name_to_address) {
  if (!code_gen_)
    return;
  code_gen_->update_machine_code(name_to_address);
}

string CodeLine::FormattedCOP() {
  if (!code_gen_)
    return {};
  return code_gen_->FormattedCOP();
}

///////////////////////////////////////////////////////////////////////////////

StringConst& StringConst::operator=(const StringConst& rval) {
  this->str_ = rval.str_;
  this->addr_ = rval.addr_;
  return *this;
}

uint16_t StringConst::get_size() const {
  if (str_.size() >= numeric_limits<uint16_t>::max()) {
    //ErrorCollector::GetInstance().err("String const is too long.");
    return 0;
  }

  return static_cast<uint16_t>(str_.size()) + 1;
}

void StringConst::set_addr(uint16_t addr) {
  if (addr > 0xFFFF) {
    cout << "Address is too much: " << addr;
    return;
  }

  addr_ = addr;
}

void StringConst::out_code() const {
  uint16_t addr = addr_;
  for (size_t i = 0; i < str_.size(); i++)
    cout << "     " << hex
       << setw(4) << setfill('0') << right << addr++ << ": "
       << setw(4) << setfill('0') << right << uint16_t(str_[i]) << " "
       << str_[i] << endl;

  cout << "     " << hex
       << setw(4) << setfill('0') << right << addr++ << ": "
       << setw(4) << setfill('0') << right << uint16_t(0) << " "
       << "Zero" << endl;
}

void StringConst::out_code(vector<uint16_t>& code) const {
  if (!str_.size())
    return;

  // string with str_.size() == 1 will store char at addr_
  // and trailing zero at address addr_ + 1, so:
  uint16_t max_str_addr = addr_ + static_cast<uint16_t>(str_.size());

  if (max_str_addr + 1 > code.size())
    code.resize(max_str_addr + 1, 0U);

  for (size_t i = 0; i < str_.size(); i++)
    code[addr_ + i] = str_[i];
  code[max_str_addr] = 0;
}

///////////////////////////////////////////////////////////////////////////////

int Assembler::process(string fname, bool show_preprocess_out) {
  FileReader fr;
  int res = fr.read_file(fname, &lines_);
  if (res != 0)
    return res;

  Preprocessor pre;
  pre.Preprocess(&lines_);

  if (show_preprocess_out)
    print_preprocessed();

  merge_code_with_labels();
  extract_orgs();
  extract_string();
  pass1();
  pass2();
  pass3();
  out_code();

  out_labels();
  out_orgs();

  return ErrorCollector::GetInstance().have_errors();
}

void Assembler::print_preprocessed() {
  cout << "-------- preprocessed source: --------" << endl;
  map<int, string>::iterator it;
  for (it = lines_.begin(); it != lines_.end(); it++)
    cout << it->second << endl;
  cout << "-------- end of preprocessed source --------" << endl;
}

void Assembler::merge_code_with_labels() {
  map<int, string>::iterator it, prev;
  for (it = lines_.begin(); it != lines_.end();) {
    prev = it;
    it++;
    if (*prev->second.rbegin() == ':' &&       // ok, label was found
        it != lines_.end()) {                  // and we have some code on the next line
      it->second = prev->second + it->second;  // move label to the next line
      lines_.erase(prev);                      // remove label from curent line
    }
  }
}

void Assembler::extract_orgs() {
  map<int, string>::iterator it;
  for (it = lines_.begin(); it != lines_.end();) {
    int line = it->first;
    string org = NormalizeLine(it->second);
    if (org.find(".org") == 0) {
      cout << line << ":" << org << endl;
      org.erase(0, sizeof(".org"));

      int val {0};
      string msg_err;
      if (StrToInt(ToUpper(org), &val, &msg_err)) {
        line_to_org_[line] = val;
        cout << "now line " << line << " has address " << val << endl;
      } else
        cout << "Can't convert org value to int" << endl << msg_err << endl;
      it = lines_.erase(it);  // now remove this directive from asm
    }
    else
      it++;
  }
}

void Assembler::extract_string() {
  map<int, string>::iterator it;
  for (it = lines_.begin(); it != lines_.end();) {
    string str = NormalizeLine(it->second);
    if (str.find(".str") == 0) {
      str.erase(0, sizeof(".str"));

      size_t pos = str.find(" ");
      if (pos == string::npos) {
        cout << "Error in string const: '" << it->second << "'" << endl;
        cout << "Line: " << it->first << ". String value not found" << endl;
      } else if (pos < str.size()) {
        string str_name = Trim(str.substr(0, pos));
        string str_val = RemoveQuotes(Trim(str.substr(pos + 1)));
        string_consts_[str_name] = StringConst(str_val);
        cout << "STR '" << str_name << "' = '" << str_val << "'" << endl;
      }
      it = lines_.erase(it);  // now remove this directive from asm
    }
    else
      it++;
  }
}

// generate machine code
void Assembler::pass1() {
  map<int, string>::iterator it;
  for (it = lines_.begin(); it != lines_.end(); it++) {
    string nl = NormalizeLine(it->second);
    if (nl.size() == 0)
      continue;
    code_.push_back(CodeLine(it->first, nl));
  }
}

// get real address of labels & string
void Assembler::pass2() {
  uint16_t addr = 0;
  vector<CodeLine>::iterator it;
  map<int, uint16_t>::iterator oit = line_to_org_.begin();
  for (it = code_.begin(); it != code_.end(); it++, addr++) {
    if (oit != line_to_org_.end() &&
        it->line_number() > oit->first) {
      cout << "***** org placed here *****" << endl;
      if (oit->second > addr) {
        addr = oit->second;
        cout << "move address to: " << addr << endl;
      }
      oit++;
    }

    it->set_address(addr);

    vector<string> labels = it->get_labels();
    vector<string>::iterator lit;
    for (lit = labels.begin(); lit != labels.end(); lit++)
      name_to_address_[*lit] = addr;
  }

  uint16_t max_addr = get_max_address();
  cout << "max_addr: " << max_addr << " (" << hex << max_addr << "h)" << endl;

  addr = max_addr + 1;
  for (auto& s : string_consts_) {
    s.second.set_addr(addr);
    name_to_address_[s.first] = addr;
    cout << "add to name_to_address_: " << s.first << " = " << to_string(addr) << endl;
    addr += s.second.get_size();
  }
}

// set real jump addresses
void Assembler::pass3() {
  vector<CodeLine>::iterator it;
  for (it = code_.begin(); it != code_.end(); it++)
    it->update_machine_code(name_to_address_);
}

uint16_t Assembler::get_max_address() {
  uint16_t max_addr {0};
  vector<CodeLine>::iterator it;
  for (it = code_.begin(); it != code_.end(); it++)
    if (max_addr < it->address())
      max_addr = it->address();
  return max_addr;
}

void Assembler::out_code() {
  cout << "STRINGS ADDR:" << endl;
  for (const auto& s : string_consts_)
    cout << s.first << ": " << s.second.addr() << endl;

  cout << "LINE ADDR: COP   ASM                       LABELS          FORMATTED_COP" << endl;
  vector<CodeLine>::iterator it;
  for (it = code_.begin(); it != code_.end(); it++) {
    cout << dec
         << setw(4) << setfill(' ') << right << it->line_number() << " "
         << hex
         << setw(4) << setfill('0') << right << it->address() << ": "
         << setw(4) << setfill('0') << right << it->generate_machine_code() << "  "
         << setw(24) << setfill(' ') << left << it->get_line_text() << "  "
         << setw(16) << setfill(' ') << left << it->get_labels_as_string()
         << setw(16) << setfill(' ') << left << it->FormattedCOP()
         << endl;

    string el = ErrorCollector::GetInstance().get(it->line_number());
    if (el.size())  // for (auto& e : el)
      cout << "         > " << el << endl;
  }

  cout << "STRINGS:" << endl;
  if (string_consts_.empty())
    cout << " empty" << endl;
  for (auto& s : string_consts_) {
    cout << s.first << ":" << endl;
    s.second.addr();
    s.second.out_code();
  }
}

void Assembler::out_code(vector<uint16_t>& code) {
  code.clear();

  uint16_t max_addr = get_max_address();
  if (!max_addr) {
    cout << "No code to output" << endl;
    return;
  }

  // numbers from 0 to 5 have 6 pcs (max + 1)
  code.resize(max_addr + 1, 0U);

  vector<CodeLine>::iterator it;
  for (it = code_.begin(); it != code_.end(); it++)
    code[it->address()] = it->generate_machine_code();

  // StringConst::out_code will resize 'code' if required
  for (auto& s : string_consts_)
    s.second.out_code(code);
}

void Assembler::write_binary(string fname) {
  vector<uint16_t> code;
  out_code(code);
  if (!code.size())
    return;

  ofstream f;
  f.open(fname, ios::binary);
  if (!f) {
    cout << "Error. Can't open file " << fname << endl;
    return;
  }

  f.write(reinterpret_cast<const char*>(code.data()),
          code.size()*sizeof(uint16_t));
  f.close();
}

void Assembler::out_labels() {
  cout << "LABELS:" << endl;
  if (name_to_address_.empty())
    cout << " empty" << endl;
  for (auto v : name_to_address_)
    //    line number        line code
    cout << v.first << " " << v.second << endl;
}

void Assembler::out_orgs() {
  cout << "ORGS:" << endl;
  if (line_to_org_.empty())
    cout << " empty" << endl;
  for (auto v : line_to_org_)
    cout << v.first << " " << v.second << endl;
}

///////////////////////////////////////////////////////////////////////////////
