TheJustMoose/74HC-CPU/soft/emul/emul.h

/*
  74hcpu Emulator
*/

#pragma once

#include <cstdint>
#include <memory>

#include "lcd.h"
#include "observer.h"
#include "consts.h"

typedef uint16_t RAM_ADDR;
typedef uint8_t RAM_DATA;
constexpr RAM_ADDR LAST_RAM_ADDR {0xFFFF};

typedef uint16_t ROM_ADDR;
typedef uint16_t ROM_DATA;

typedef uint8_t PORT_DATA;

class Instruction;
class CPU;

Cops GetCopFromMachineCode(uint16_t machine_code);
std::unique_ptr<Instruction> CreateFromMachineCode(ROM_DATA machine_code);

class Reg : public Subject {
public:
  Reg(std::string name) : name_(name) {}

  operator uint8_t() const {
    return value_;
  }

  operator int() const {
    return value_;
  }

  Reg& operator=(uint8_t v) {
    value_ = v;
    Notify();
    return *this;
  }

  std::string name() { return name_; }

private:
  uint8_t value_ {0};
  std::string name_ {};
};

class Bank {
public:
  Reg R0 {"R0"};
  Reg R1 {"R1"};
  Reg R2 {"R2"};
  Reg R3 {"R3"};
  Reg R4 {"R4"};
  Reg R5 {"R5"};
  Reg R6 {"R6"};
  Reg R7 {"R7"};

  Reg& GetRegByNum(uint8_t RegNum);  // RegNum: 0 - 7
};

class RAM {
public:
  RAM(uint8_t BitWidth = 8) {}
};

class ROM {
public:
  ROM() = default;

  ROM_ADDR GetMaxAddress() {
    return max_addr_;
  }

  ROM_DATA Read(ROM_ADDR addr) {
    // вообще, ROM_ADDR 16 битный, поэтому проверка не имеет смысла (кажется)
    if (addr >= max_addr_)  // хотя если размер меньше 2^16, то лучше проверить :)
      throw std::exception("ROM address out of bounds");
    return rom_[addr];
  }

  void Flash(std::vector<ROM_DATA>&& rom) {
    if (rom.size() >= 0x10000)
      throw std::exception("Firmware is too large");

    rom_ = rom;
    max_addr_ = static_cast<ROM_ADDR>(rom_.size());
  }

private:
  ROM_ADDR max_addr_ {0};
  std::vector<ROM_DATA> rom_;
};

class OutPort {
public:
  void Write(PORT_DATA);
};

class RegByNum {
public:
  RegByNum(CPU* cpu) : cpu_(cpu) {}

  Reg& operator[](uint8_t RegNum);

private:
  CPU* cpu_ {nullptr};
};

class CPU {
public:
  ROM rom;
  RAM ram;
  OutPort LCD_data;
  OutPort LCD_ctrl;
  OutPort port2;
  OutPort port3;
  Flags flags;

  CPU() {}

  void Step();

  void ActivateBank(int BankNum);  // 0 - Bank0, 1 - Bank1
  Bank& ActiveBank();

  RegByNum R {this};

private:
  Bank bank0;
  Bank bank1;

  ROM_ADDR IP{0};  // Instruction Pointer
  RAM_ADDR SP{LAST_RAM_ADDR};  // Stack Pointer

  int active_bank_num_ {0};
};

class System {
public:
  CPU cpu;
  LCD lcd;

  void Step();
};

class Instruction {
public:
  // 74hcpu has 16 bit instructions
  Instruction(ROM_DATA code) : code_(code) {}
  virtual void Execute(CPU* cpu) = 0;

//protected:
  ROM_DATA code() {
    return code_;
  }

private:
  ROM_DATA code_ {0};
};

class BinaryInstruction : public Instruction {
public:
  BinaryInstruction(ROM_DATA code) : Instruction(code) {}

  virtual std::string Name() {
    return {};
  }

  Reg& LeftOp(CPU*);
  uint8_t RightOp(CPU*);
};

class Add : public BinaryInstruction {
public:
  Add(ROM_DATA code) : BinaryInstruction(code) {}
  void Execute(CPU*) override;

  std::string Name() override { return "ADD"; }
};

class AddC : public BinaryInstruction {
public:
  AddC(ROM_DATA code) : BinaryInstruction(code) {}
  void Execute(CPU*) override;

  std::string Name() override { return "ADDC"; }
};

class And : public BinaryInstruction {
public:
  And(ROM_DATA code) : BinaryInstruction(code) {}
  void Execute(CPU*) override;

  std::string Name() override { return "AND"; }
};

class Or : public BinaryInstruction {
public:
  Or(ROM_DATA code) : BinaryInstruction(code) {}
  void Execute(CPU*) override;

  std::string Name() override { return "OR"; }
};

class Xor : public BinaryInstruction {
public:
  Xor(ROM_DATA code) : BinaryInstruction(code) {}
  void Execute(CPU*) override;

  std::string Name() override { return "XOR"; }
};

class Mul : public BinaryInstruction {
public:
  Mul(ROM_DATA code) : BinaryInstruction(code) {}
  void Execute(CPU*) override;

  std::string Name() override { return "MUL"; }
};

class Uno : public Instruction {
public:
  Uno(ROM_DATA code) : Instruction(code) {}
  void Execute(CPU*) override;
};

class Mov : public BinaryInstruction {
public:
  Mov(ROM_DATA code) : BinaryInstruction(code) {}
  void Execute(CPU*) override;

  std::string Name() override { return "MOV"; }
};

class Lpm : public Instruction {
public:
  Lpm(ROM_DATA code) : Instruction(code) {}
  void Execute(CPU*) override;
};

class Ld : public Instruction {
public:
  Ld(ROM_DATA code) : Instruction(code) {}
  void Execute(CPU*) override;
};

class In : public Instruction {
public:
  In(ROM_DATA code) : Instruction(code) {}
  void Execute(CPU*) override;
};

class Out : public Instruction {
public:
  Out(ROM_DATA code) : Instruction(code) {}
  void Execute(CPU*) override;
};

class St : public Instruction {
public:
  St(ROM_DATA code) : Instruction(code) {}
  void Execute(CPU*) override;
};

class Cmp : public BinaryInstruction {
public:
  Cmp(ROM_DATA code) : BinaryInstruction(code) {}
  void Execute(CPU*) override;

  std::string Name() override { return "CMP"; }
};

class CmpC : public BinaryInstruction {
public:
  CmpC(ROM_DATA code) : BinaryInstruction(code) {}
  void Execute(CPU*) override;

  std::string Name() override { return "CMPC"; }
};
