TheJustMoose/74HC-CPU/soft/uC/lexer.cc

#include "lexer.h"

#include <iostream>
#include <cctype>
#include "num.h"
#include "real.h"
#include "tag.h"
#include "token.h"
#include "type.h"
#include "word.h"

using namespace std;

// static
int Lexer::line_ {1};
map<string, shared_ptr<Word>> Lexer::words_ {};
vector<shared_ptr<Token>> Lexer::tokens_ {};

Lexer::Lexer(istream& is)
  : is_(is) {
  reserve( shared_ptr<Word>(new Word( "if", Tag::tIF )) );
  reserve( shared_ptr<Word>(new Word( "else", Tag::tELSE )) );
  reserve( shared_ptr<Word>(new Word( "while", Tag::tWHILE )) );
  reserve( shared_ptr<Word>(new Word( "do", Tag::tDO )) );
  reserve( shared_ptr<Word>(new Word( "break", Tag::tBREAK )) );

  reserve( shared_ptr<Word>(new Word( "true", Tag::tTRUE )) );
  reserve( shared_ptr<Word>(new Word( "false", Tag::tFALSE )) );

  reserve( shared_ptr<Word>(new Type( "int", Tag::tBASIC, 4 )) );
  reserve( shared_ptr<Word>(new Type( "float", Tag::tBASIC, 8 )) );
  reserve( shared_ptr<Word>(new Type( "char", Tag::tBASIC, 1 )) );
  reserve( shared_ptr<Word>(new Type( "bool", Tag::tBASIC, 1 )) );

  reserve( shared_ptr<Word>(new Word( "&&", Tag::tAND )) );
  reserve( shared_ptr<Word>(new Word( "||", Tag::tOR )) );
  reserve( shared_ptr<Word>(new Word( "==", Tag::tEQ )) );
  reserve( shared_ptr<Word>(new Word( "!=", Tag::tNE )) );
  reserve( shared_ptr<Word>(new Word( "<=", Tag::tLE )) );
  reserve( shared_ptr<Word>(new Word( ">=", Tag::tGE )) );
  reserve( shared_ptr<Word>(new Word( "minus", Tag::tMINUS )) );
  reserve( shared_ptr<Word>(new Word( "#t", Tag::tTEMP )) );
}

Lexer::~Lexer() {
}

// static
Word* Lexer::get_word(std::string word) {
  if (words_.find(word) == words_.end())
    return nullptr;

  return words_[word].get();
}

void Lexer::reserve(shared_ptr<Word> w) {
  if (!w) {
    cerr << "Word is NULL" << endl;
    return;
  }

  // w will be removed during return cause ref count will become zero
  if (words_.find(w->lexeme()) != words_.end())
    return;

  words_[w->lexeme()] = w;
}

Token* Lexer::reserve(Token* t) {
  shared_ptr<Token> tmp(t);
  tokens_.push_back(tmp);
  return tokens_.rbegin()->get();
}

void Lexer::readch() {
  if (!is_.get(peek_))
    peek_ = 0;
}

bool Lexer::readch(char c) {
  readch();
  if (peek_ != c)
   return false;

  peek_ = ' ';
  return true;
}

Token* Lexer::scan() {
  for( ; ; readch() ) {
    if (peek_ == ' ' || peek_ == '\t' || peek_ == '\r')
      continue;
    else if (peek_ == '\n')
      line_++;
    else if (peek_ == 0)
      return new NullToken();
    else
      break;
  }

  switch (peek_) {
    case '&':
      if( readch('&') ) return get_word("&&");  else return reserve(new Token('&'));
    case '|':
      if( readch('|') ) return get_word("||");  else return reserve(new Token('|'));
    case '=':
      if( readch('=') ) return get_word("==");  else return reserve(new Token('='));
    case '!':
      if( readch('=') ) return get_word("!=");  else return reserve(new Token('!'));
    case '<':
      if( readch('=') ) return get_word("<=");  else return reserve(new Token('<'));
    case '>':
      if( readch('=') ) return get_word(">=");  else return reserve(new Token('>'));
  }

  if (isdigit(peek_)) {
    int v = 0;
    do {
      v = 10*v + int(peek_ - '0');
      readch();
    } while(peek_ && isdigit(peek_) );

    if( peek_ != '.' )
      return reserve(new Num(v));

    float x = v;
    float d = 10;
    for (;;) {
      readch();
      if (! isdigit(peek_))
        break;
      x = x + int(peek_ - '0') / d;
      d *= 10;
    }
    return reserve(new Real(x));
  }

  // IDs should start from letter or underscore
  if (isalpha(peek_) || (peek_ == '_')) {
    string b;
    do {
      b += peek_;
      readch();
    } while (isalpha(peek_) || isdigit(peek_) || (peek_ == '_'));
    // and may contain digit

    if (words_.find(b) != words_.end())
      return words_[b].get();

    shared_ptr<Word> w(new Word(b, Tag::tID));
    words_[b] = w;
    return get_word(b);
  } 

  if (peek_ == 0)
    return new NullToken();

  Token* tok = reserve(new Token(peek_));
  peek_ = ' ';
  return tok;
}
