TheJustMoose/74HC-CPU/soft/asm/unit_tests_cop.cc

#define DOCTEST_CONFIG_IMPLEMENT_WITH_MAIN
#include <doctest.h>

#include <string>

#include "assm.h"
#include "str_util.h"

using namespace std;

TEST_CASE("check arithm COPs") {
  CodeLine cl1(1, "NOP");
  CHECK(cl1.generate_machine_code() == 0xFFFF);

  // 0000 000 0 000 00000
  CodeLine cl2(1, "ADD R0, R0");
  CHECK(cl2.generate_machine_code() == 0x0000);

  // 0000 001 0 010 00000
  CodeLine cl3(1, "ADD R1, R2");
  CHECK(cl3.generate_machine_code() == 0x0240);

  // 0000 010 0 011 00000
  CodeLine cl4(1, "ADD R2, R3");
  CHECK(cl4.generate_machine_code() == 0x0460);

  // 0001 010 0 011 00000
  CodeLine cl5(1, "ADDC R2, R3");
  CHECK(cl5.generate_machine_code() == 0x1460);

  // 0010 011 0 100 00000
  CodeLine cl6(1, "AND R3, R4");
  CHECK(cl6.generate_machine_code() == 0x2680);

  // 0011 100 0 101 00000
  CodeLine cl7(1, "OR R4, R5");
  CHECK(cl7.generate_machine_code() == 0x38A0);

  // 0100 101 0 110 00000
  CodeLine cl8(1, "XOR R5, R6");
  CHECK(cl8.generate_machine_code() == 0x4AC0);

  // 0101 110 0 111 00000
  CodeLine cl9(1, "MUL R6, R7");
  CHECK(cl9.generate_machine_code() == 0x5CE0);

  // 0110 111 0 000 00000
  CodeLine clB(1, "INV R7");
  CHECK(clB.generate_machine_code() == 0x6E00);

  // 0110 111 0 001 00000
  CodeLine clA(1, "SWAP R7");
  CHECK(clA.generate_machine_code() == 0x6E20);

  // 0110 111 0 010 00000
  CodeLine clC(1, "LSR R7");
  CHECK(clC.generate_machine_code() == 0x6E40);

  // 0110 111 0 011 00000
  CodeLine clD(1, "LSRC R7");
  CHECK(clD.generate_machine_code() == 0x6E60);

  // 0111 000 0 111 00000
  CodeLine clE(1, "MOV R0, R7");
  CHECK(clE.generate_machine_code() == 0x70E0);
}

TEST_CASE("check ROM COPs") {
  // LPM  DST W SR DU OFST
  // 1000 000 0 00 00 0000
  CodeLine cl1(1, "LPM R0, X");
  CHECK(cl1.generate_machine_code() == 0x8000);

  // 1000 101 0 00 00 0000
  CodeLine cl2(1, "LPM R5, X");
  CHECK(cl2.generate_machine_code() == 0x8A00);

  // 1000 000 0 01 00 0000
  CodeLine cl3(1, "LPM R0, Y");
  CHECK(cl3.generate_machine_code() == 0x8040);

  // 1000 000 0 10 00 0000
  CodeLine cl4(1, "LPM R0, Z");  // R0 = *Z;
  CHECK(cl4.generate_machine_code() == 0x8080);

  // 1000 000 0 11 00 0000
  CodeLine cl5(1, "LPM R0, SP");
  CHECK(cl5.generate_machine_code() == 0x80C0);

  // 1000 110 0 11 00 0001
  CodeLine cl6(1, "LPM R6, SP+1");  // R6 = *(SP + 1);
  CHECK(cl6.generate_machine_code() == 0x8CC1);

  // 1000 110 0 11 00 0111
  CodeLine cl7(1, "LPM R6, SP+7");  // R6 = *(SP + 7);
  CHECK(cl7.generate_machine_code() == 0x8CC7);

  // 1000 110 0 11 00 1111
  CodeLine cl8(1, "LPM R6, SP-1");
  CHECK(cl8.generate_machine_code() == 0x8CCF);

  // 1000 110 0 11 00 1110
  CodeLine cl9(1, "LPM R6, SP-2");
  CHECK(cl9.generate_machine_code() == 0x8CCE);

  // 1000 110 0 11 00 1001
  CodeLine clA(1, "LPM R6, SP-7");
  CHECK(clA.generate_machine_code() == 0x8CC9);

  // 1000 110 0 11 00 1000
  CodeLine clB(1, "LPM R6, SP-8");
  CHECK(clB.generate_machine_code() == 0x8CC8);

  // LPM  DST W SR DU OFST
  // 1000 101 0 00 01 0000
  CodeLine clC(1, "LPM R5, XI");  // R5 = *X++; in C++ notation (Load with post-increment)
  CHECK(clC.generate_machine_code() == 0x8A10);

  // 1000 101 0 00 10 0000
  CodeLine clD(1, "LPM R5, XD");  // R5 = *X--; in C++ notation (Load with post-decrement)
  CHECK(clD.generate_machine_code() == 0x8A20);

  // 1000 101 0 00 10 0001
  CodeLine clE(1, "LPM R5, XD+1");  // R5 = *(X + 1); X--;  in C++ notation (Load with post-decrement and displacement)
  CHECK(clE.generate_machine_code() == 0x8A21);
}

TEST_CASE("check RAM COPs") {
  // LD   DST - SR DU OFST
  // 1001 000 0 00 00 0000
  CodeLine cl1(1, "LD R0, X");
  CHECK(cl1.generate_machine_code() == 0x9000);

  // ST   SRC - DS DU OFST
  // 1100 000 0 00 00 0000
  CodeLine cl2(1, "ST X, R0");
  CHECK(cl2.generate_machine_code() == 0xC000);

  // 1100 000 0 00 00 0101
  CodeLine cl3(1, "ST X+5, R0");
  CHECK(cl3.generate_machine_code() == 0xC005);

  // 1100 111 0 01 00 0000
  CodeLine cl4(1, "ST Y, R7");
  CHECK(cl4.generate_machine_code() == 0xCE40);
}

TEST_CASE("check I/O COPs") {
  // IN   DST  PORT ZzIi
  // 1010 011 00010 0000
  CodeLine cl1(1, "IN R3, PINS1");
  CHECK(cl1.generate_machine_code() == 0xA620);

  // OUT  SRC  PORT OoXx
  // 1011 111 01011 0000  // PORT9 have number 11, see port_names
  CodeLine cl2(1, "OUT PORT9, R7");
  CHECK(cl2.generate_machine_code() == 0xBEB0);
}

TEST_CASE("check branches COPs") {
  // 1111 0010 00000000
  CodeLine cl1(1, "LBL: RET");
  CHECK(cl1.generate_machine_code() == 0xF200);
  // 1111 0000 00000000
  CodeLine cl2(2, "CALL LBL");  // fortunately, LBL address is 0
  CHECK(cl2.generate_machine_code() == 0xF000);

  // 1111 0001 00001010
  CodeLine cl3(1, "JMP LBL");
  // Try to set LBL offset (from current address)
  cl3.update_machine_code( map<string, uint16_t> { {"LBL", 10} } );
  CHECK(cl3.generate_machine_code() == 0xF10A);

  // 1111 0001 11111111
  CodeLine cl4(1, "JMP LBL");
  cl4.set_address(0x0010u);
  // Try to set LBL offset (from current address)
  cl4.update_machine_code( map<string, uint16_t> { { "LBL", 0x000Fu } } );
  CHECK(cl4.generate_machine_code() == 0xF1FF);  // jmp to previous instruction

  // 1111 0010 00000000
  CodeLine cl5(1, "RET");
  CHECK(cl5.generate_machine_code() == 0xF200);

  // 1111 0011 00000000
  CodeLine cl6(1, "RETI");
  CHECK(cl6.generate_machine_code() == 0xF300);

  // 1111 0100 00000000
  CodeLine cl7(1, "JL TST");
  CHECK(cl7.generate_machine_code() == 0xF400);

  // 1111 0101 00000000
  CodeLine cl8(1, "JE TST");
  CHECK(cl8.generate_machine_code() == 0xF500);

  // 1111 0110 00000000
  CodeLine cl9(1, "JNE TST");
  CHECK(cl9.generate_machine_code() == 0xF600);

  // 1111 0111 00000000
  CodeLine clA(1, "JG TST");
  CHECK(clA.generate_machine_code() == 0xF700);

  // 1111 1000 00000000
  CodeLine clB(1, "JZ TST");
  CHECK(clB.generate_machine_code() == 0xF800);

  // 1111 1001 00000000
  CodeLine clC(1, "JNZ TST");
  CHECK(clC.generate_machine_code() == 0xF900);

  // 1111 1010 00000000
  CodeLine clD(1, "JC TST");
  CHECK(clD.generate_machine_code() == 0xFA00);

  // 1111 1011 00000000
  CodeLine clE(1, "JNC TST");
  CHECK(clE.generate_machine_code() == 0xFB00);

  // 1111 1100 00000000
  CodeLine clF(1, "JHC TST");
  CHECK(clF.generate_machine_code() == 0xFC00);

  // 1111 1101 00000000
  CodeLine clG(1, "JNHC TST");
  CHECK(clG.generate_machine_code() == 0xFD00);

  // 1111 1110 00000000
  CodeLine clH(1, "AFCALL TST");
  CHECK(clH.generate_machine_code() == 0xFE00);

  // 1111 1111 11111111
  CodeLine clI(1, "NOP");
  CHECK(clI.generate_machine_code() == 0xFFFF);

  // 1111 1111 11111110
  CodeLine clJ(1, "STOP");
  CHECK(clJ.generate_machine_code() == 0xFFFE);
}

TEST_CASE("check jump distance") {
  // 1111 0001 00000000
  CodeLine cl1(1, "JMP L1");
  // Try to set L1 label offset (from current address)
  cl1.update_machine_code( map<string, uint16_t> { {"L1", 0} } );  // no jmp (jmp to same command)
  CHECK(cl1.generate_machine_code() == 0xF100);

  // 1111 0001 11111111
  CodeLine cl2(1, "JMP L1");
  cl2.set_address(0x000Au);
  // Try to set L1 label offset (from current address)
  cl2.update_machine_code( map<string, uint16_t> { { "L1", 0x0009u } } );  // jmp to previous cmd
  CHECK(cl2.generate_machine_code() == 0xF1FF);

  // 1111 0001 11111110
  CodeLine cl3(1, "JMP L1");
  cl3.set_address(0x000Au);
  // Try to set L1 label offset (from current address)
  cl3.update_machine_code( map<string, uint16_t> { { "L1", 0x0008u } } );  // jmp two cmd back
  CHECK(cl3.generate_machine_code() == 0xF1FE);
}
