TheJustMoose/74HC-CPU/soft/asm/str_util.h

#pragma once

#include <string>
#include <vector>

std::string ToUpper(std::string);
std::string NormalizeLine(std::string);
std::string RemoveQuotes(std::string);

bool StrToInt(std::string val, int* pout, std::string* err = nullptr);

bool IsSpace(char);
bool IsDelimeter(char);

std::vector<std::string> Split(std::string);
std::vector<std::string> SplitToCmdParts(std::string);

std::string TrimRight(std::string s);
std::string TrimLeft(std::string s);
std::string Trim(std::string s);

std::string Join(std::vector<std::string> v, char del = '|');
